RobertPHeller/ESP32-LCC/AtlasLightBoardWiFiLCCTraction_Sound/firmware/doc/Images/LEDPolarity.png

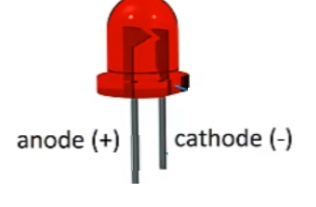
AtlasLightBoardWiFiLCCTraction_Sound/firmware/doc/Images/LEDPolarity.png
