RobertPHeller/ESP32-LCC/AtlasLightBoardWiFiLCCTraction_Sound/firmware/doc/Images/LEDPolaritySymbol.png

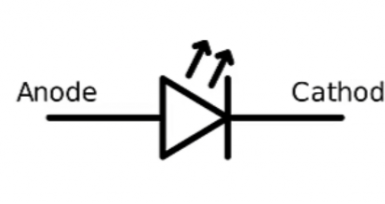
AtlasLightBoardWiFiLCCTraction_Sound/firmware/doc/Images/LEDPolaritySymbol.png
