RobertPHeller/ESP32-LCC/ESP32-Feather-6B6L-SMD/ESP32-Feather-6B6L-SMD.png

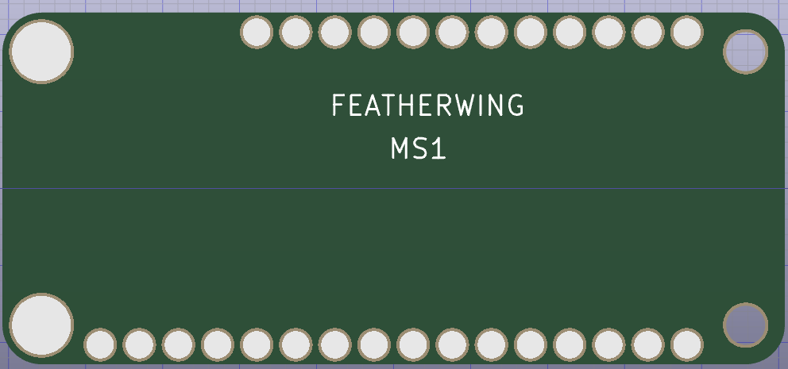
ESP32-Feather-6B6L-SMD/ESP32-Feather-6B6L-SMD.png
