RobertPHeller/ESP32-LCC/ESP32-Mini32-OctalBuffer/KitBooklet/images/8ballsignhookup.png

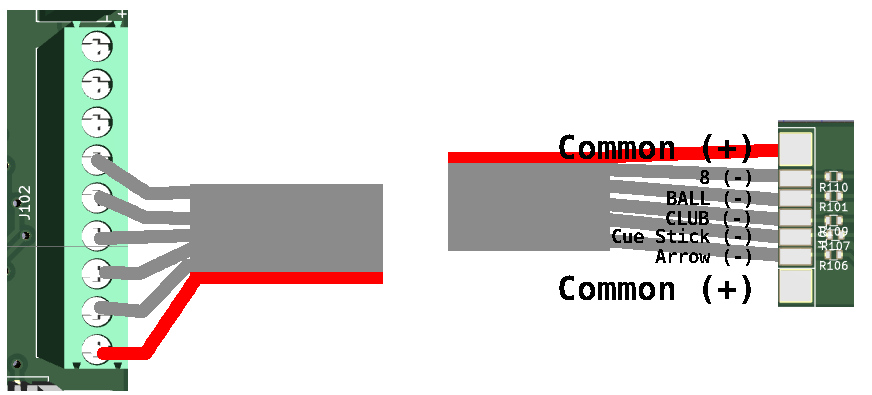
ESP32-Mini32-OctalBuffer/KitBooklet/images/8ballsignhookup.png
