RobertPHeller/ESP32-LCC/ESP32-T7S3-ArduinoBase/firmware/doc/images/StandardRes1Track.png

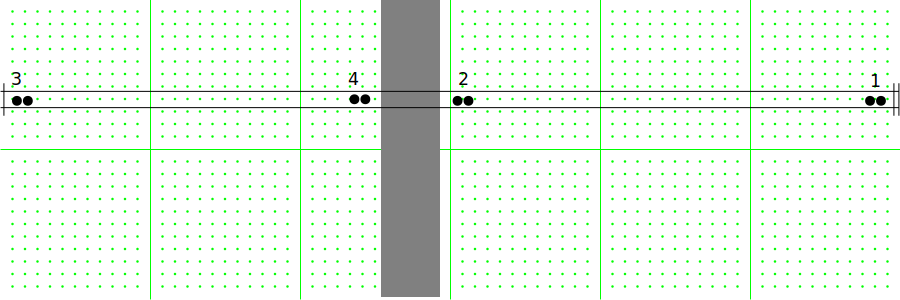
ESP32-T7S3-ArduinoBase/firmware/doc/images/StandardRes1Track.png
