RobertPHeller/ESP32-LCC/ESP32-T7S3-TextDisplaySign/firmware/doc/images/ESP32-T7S3-TextDisplaySign-cut.png

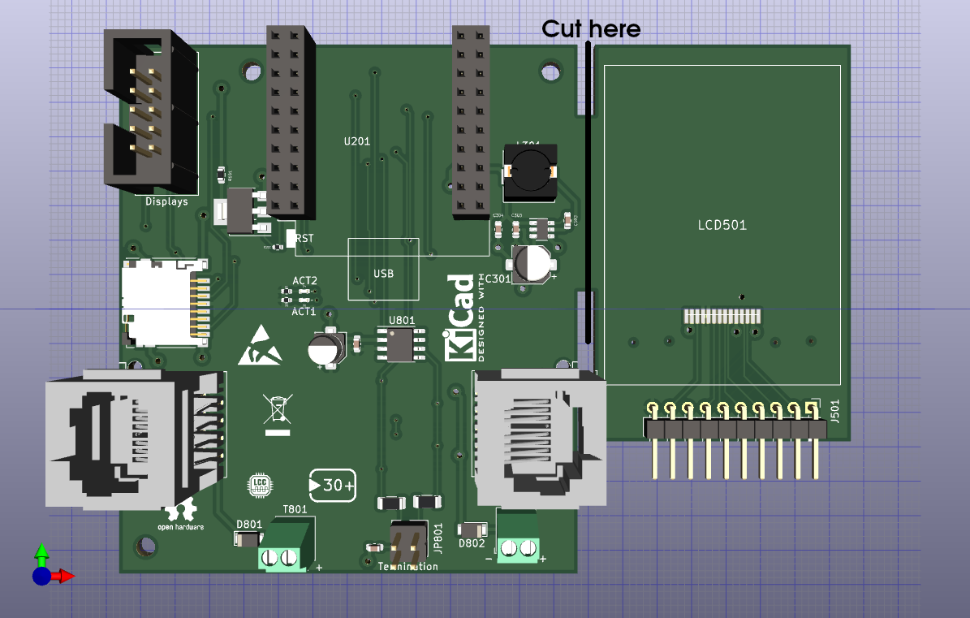
ESP32-T7S3-TextDisplaySign/firmware/doc/images/ESP32-T7S3-TextDisplaySign-cut.png
