RobertPHeller/ESP32-LCC/P9WiFiLCCTraction_Sound/firmware/doc/Images/P9WiFiLCCTraction_Sound_Top3D.png

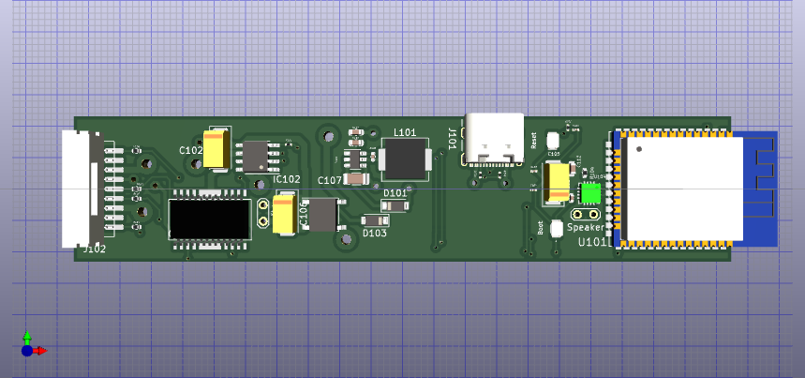
P9WiFiLCCTraction_Sound/firmware/doc/Images/P9WiFiLCCTraction_Sound_Top3D.png
