RobertPHeller/ESP32-LCC/T7S3-MiniDisplay/firmware/doc/Images/4210-00.jpg

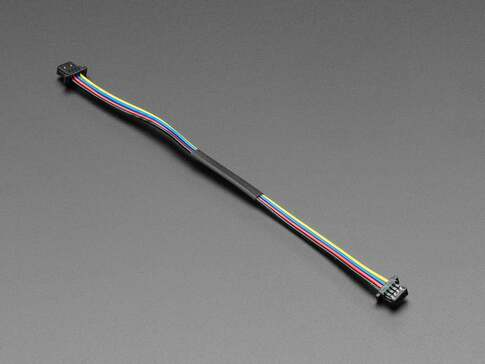
T7S3-MiniDisplay/firmware/doc/Images/4210-00.jpg
