RobertPHeller/ESP32-LCC/T7S3-MiniDisplay/firmware/doc/Images/4440-07.jpg

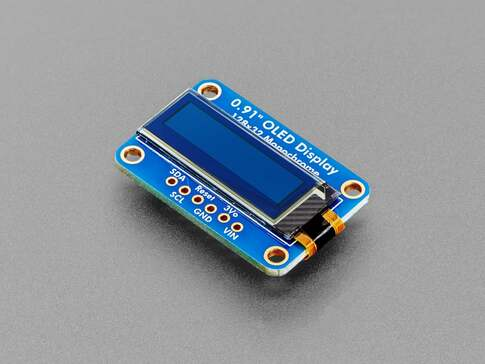
T7S3-MiniDisplay/firmware/doc/Images/4440-07.jpg
