RobertPHeller/ESP32-LCC/T7S3-MiniDisplay/firmware/doc/Images/T7S3MiniDisplay_Top3D.png

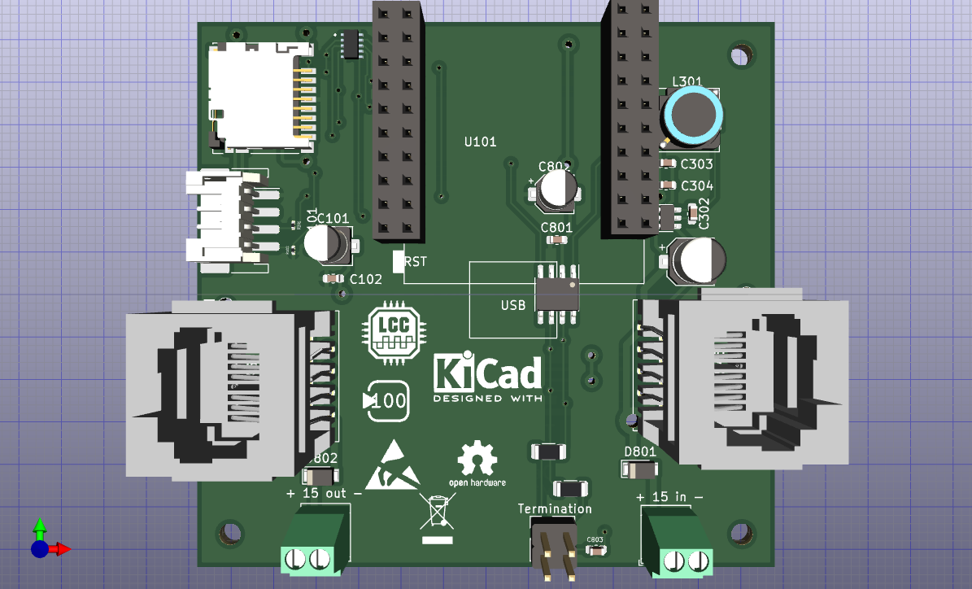
T7S3-MiniDisplay/firmware/doc/Images/T7S3MiniDisplay_Top3D.png
