RobertPHeller/ESP32-LCC/ESP32-T7S3-MultiFunctionUniversalTurnout/SC-DaughterBoard.kicad_pcb

## KiCad design ESP32-T7S3-MultiFunctionUniversalTurnout/SC-DaughterBoard.kicad_pcb (2023-03-05)

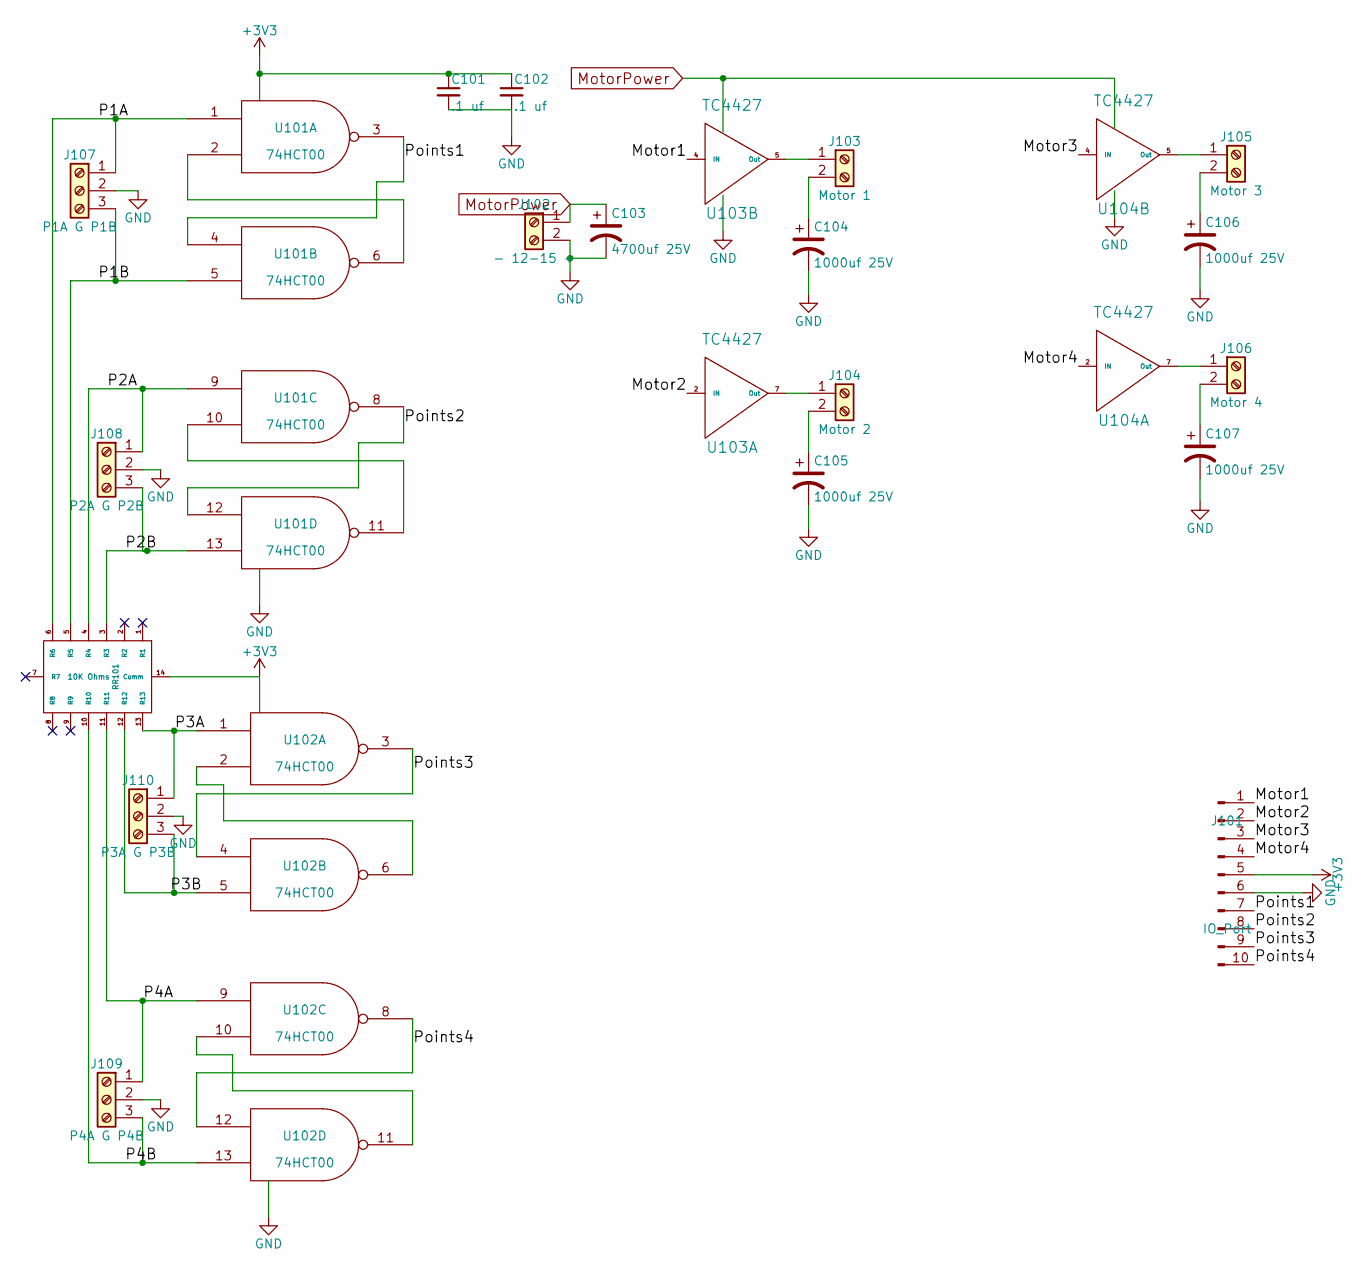
[picture p74: schematic SC-DaughterBoard.sch, ESP32 S3 Multifunction Board SC Daughter Board]

Parts:
C101, C102: .1 uf; C_0603; Mouser Part Number 710-885012206095
C103: 4700uf 25V; EEEFK0J133SM; Mouser Part Number 667-EEE-FK1E472SM
C104, C105, C106, C107: 1000uf 25V; CP_Elec_10x10.5; Mouser Part Number 661-EMZS250ARA102MJA
J101: IO_Port; Pin_Header_Straight_1x10_Pitch2.54mm
J102: - 12-15 +; TerminalBlock_Pheonix_PT-3.5mm_2pol
J103: Motor 1; TerminalBlock_Pheonix_PT-3.5mm_2pol
J104: Motor 2; TerminalBlock_Pheonix_PT-3.5mm_2pol
J105: Motor 3; TerminalBlock_Pheonix_PT-3.5mm_2pol
J106: Motor 4; TerminalBlock_Pheonix_PT-3.5mm_2pol
J107: P1A G P1B; TerminalBlock_Pheonix_MPT-2.54mm_3pol
J108: P2A G P2B; TerminalBlock_Pheonix_MPT-2.54mm_3pol
J109: P4A G P4B; TerminalBlock_Pheonix_MPT-2.54mm_3pol
J110: P3A G P3B; TerminalBlock_Pheonix_MPT-2.54mm_3pol
RR101: 10K Ohms; 4814P; Mouser Part Number 652-4814P-2LF-10K
U101, U102: 74HCT00; SOIC-14_3.9x8.7mm_Pitch1.27mm; Mouser Part Number 595-SN74AHC00D
U103, U104: TC4427; SOIC-8_3.9x4.9mm_Pitch1.27mm

Connections:
+3V3: C101.1, C102.1, J101.5, RR101.14 (Comm), U101.14 (VCC), U102.14 (VCC)
/Motor1: J101.1, U103.4 (IN)
/Motor2: J101.2, U103.2 (IN)
/Motor3: J101.3, U104.4 (IN)
/Motor4: J101.4, U104.2 (IN)
/P1A: J107.1, RR101.6 (R6), U101.1
/P1B: J107.3, RR101.5 (R5), U101.5
/P2A: J108.1, RR101.4 (R4), U101.9
/P2B: J108.3, RR101.3 (R3), U101.13
/P3A: J110.1, RR101.13 (R13), U102.1
/P3B: J110.3, RR101.12 (R12), U102.5
/P4A: J109.1, RR101.11 (R11), U102.9
/P4B: J109.3, RR101.10 (R10), U102.13
/Points1: J101.7, U101.3, U101.4
/Points2: J101.8, U101.8, U101.12
/Points3: J101.9, U102.3, U102.4
/Points4: J101.10, U102.8, U102.12
GND: C101.2, C102.2, C103.2, C104.2, C105.2, C106.2, C107.2, J101.6, J102.2, J107.2, J108.2, J109.2, J110.2, U101.7 (GND), U102.7 (GND), U103.3 (GND), U104.3 (GND)
MotorPower: C103.1, J102.1, U103.6 (Vdd), U104.6 (Vdd)
unnamed: C104.1, J103.2
unnamed: C105.1, J104.2
unnamed: C106.1, J105.2
unnamed: C107.1, J106.2
unnamed: J103.1, U103.5 (Out)
unnamed: J104.1, U103.7 (Out)
unnamed: J105.1, U104.5 (Out)
unnamed: J106.1, U104.7 (Out)
unnamed: U101.2, U101.6
unnamed: U101.10, U101.11
unnamed: U102.2, U102.6
unnamed: U102.10, U102.11

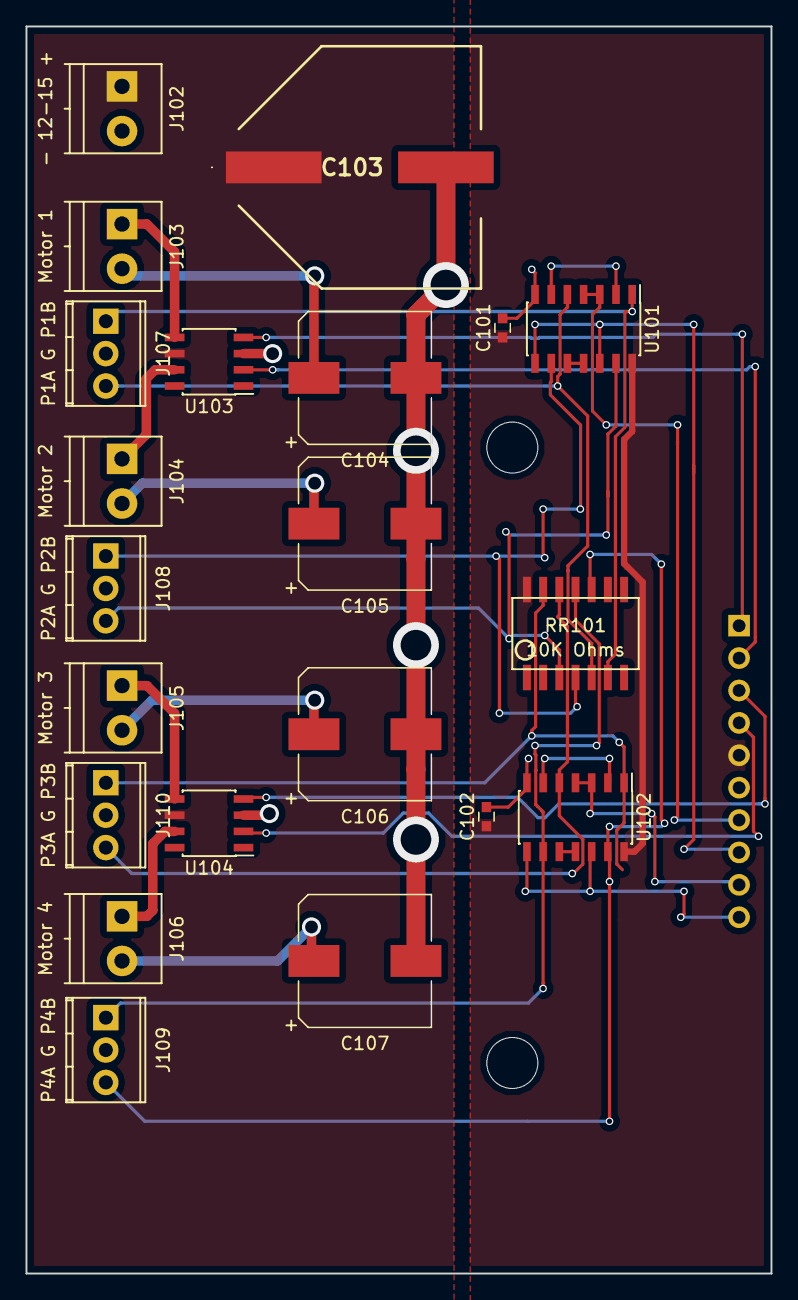
[picture p75: board SC-DaughterBoard.kicad_pcb from above]

Board: 2 copper layers, 58.4 x 97.8 mm, 22 parts (1 on the bottom side), 31 nets.
