RobertPHeller/ESP32-LCC/ESP32-T7S3-MultiFunctionUniversalTurnout/TS-DaughterBoard.kicad_pcb

## KiCad design ESP32-T7S3-MultiFunctionUniversalTurnout/TS-DaughterBoard.kicad_pcb (2023-03-04)

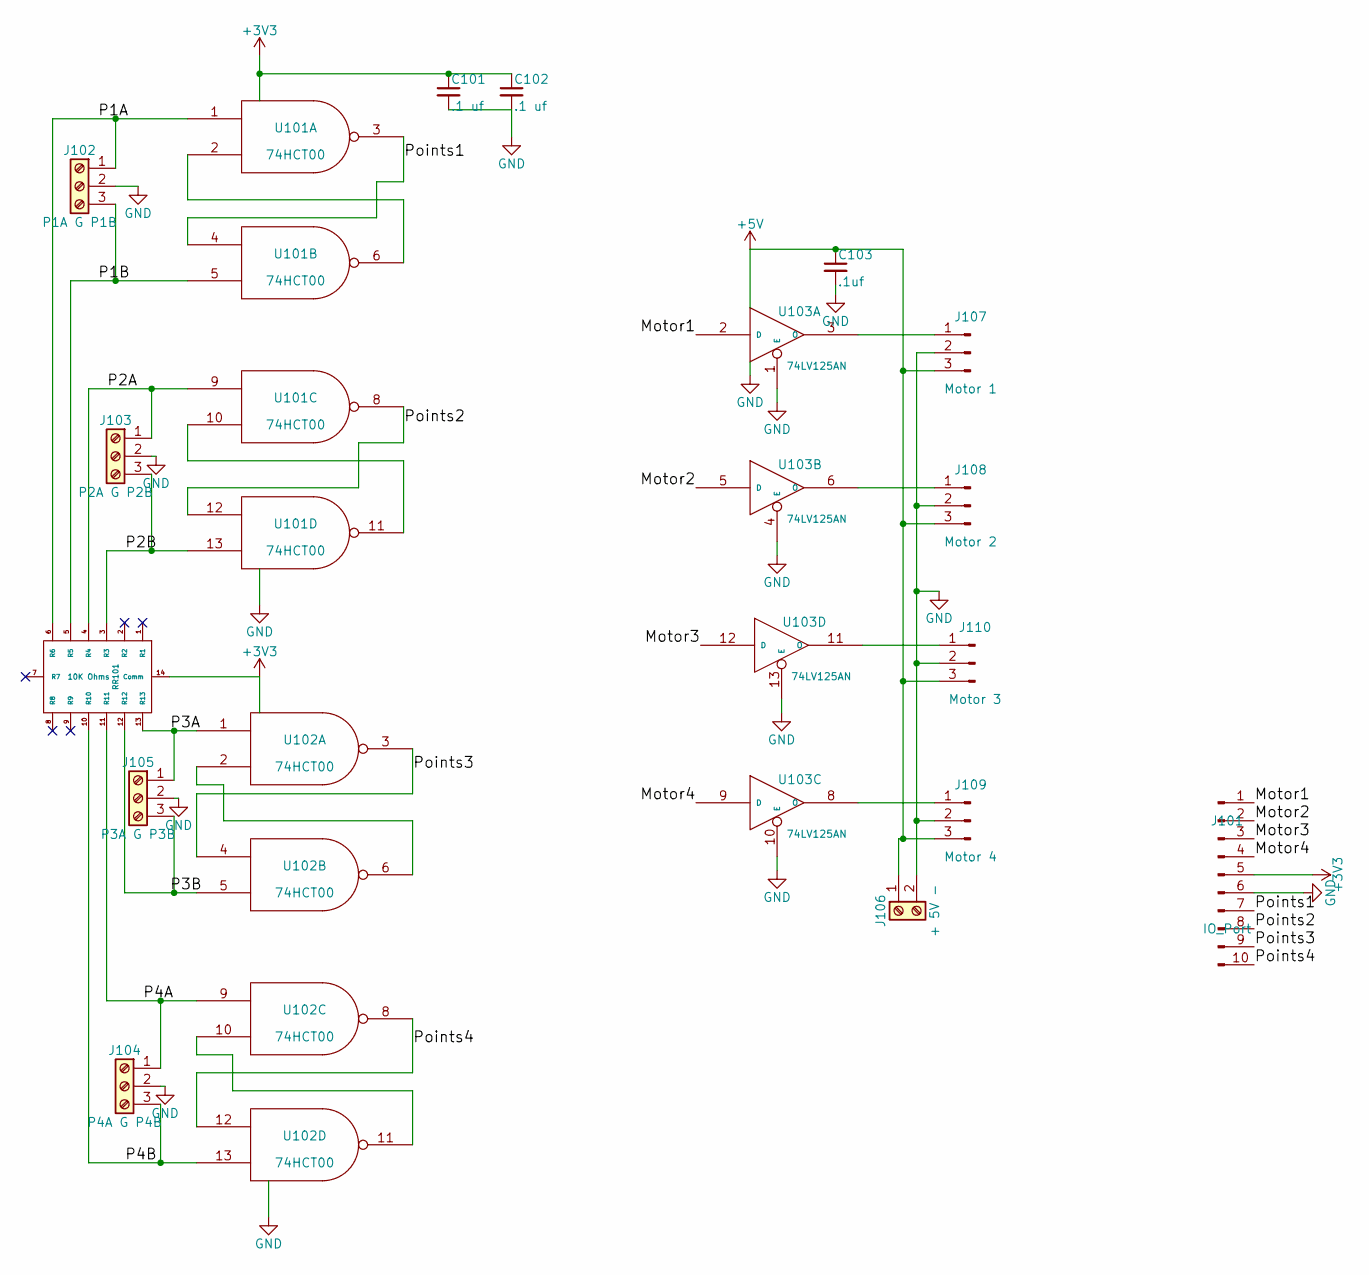
[picture p76: schematic TS-DaughterBoard.sch, ESP32 S3 Multifunction Board]

Parts:
C101, C102: .1 uf; C_0603; Mouser Part Number 710-885012206095
C103: .1uf; C_0603
J101: IO_Port; Pin_Header_Straight_1x10_Pitch2.54mm
J102: P1A G P1B; TerminalBlock_Pheonix_MPT-2.54mm_3pol
J103: P2A G P2B; TerminalBlock_Pheonix_MPT-2.54mm_3pol
J104: P4A G P4B; TerminalBlock_Pheonix_MPT-2.54mm_3pol
J105: P3A G P3B; TerminalBlock_Pheonix_MPT-2.54mm_3pol
J106: + 5V -; TerminalBlock_Pheonix_PT-3.5mm_2pol
J107: Motor 1; Pin_Header_Straight_1x03_Pitch2.54mm
J108: Motor 2; Pin_Header_Straight_1x03_Pitch2.54mm
J109: Motor 4; Pin_Header_Straight_1x03_Pitch2.54mm
J110: Motor 3; Pin_Header_Straight_1x03_Pitch2.54mm
RR101: 10K Ohms; 4814P; Mouser Part Number 652-4814P-2LF-10K
U101, U102: 74HCT00; SOIC-14_3.9x8.7mm_Pitch1.27mm; Mouser Part Number 595-SN74AHC00D
U103: 74LV125AN; SOIC-14_3.9x8.7mm_Pitch1.27mm; Mouser Part Number 771-AHCT125D118

Connections:
+3V3: C101.1, C102.1, J101.5, RR101.14 (Comm), U101.14 (VCC), U102.14 (VCC)
+5V: C103.1, J106.1, J107.3, J108.3, J109.3, J110.3, U103.14 (VXX)
/Motor1: J101.1, U103.2 (D)
/Motor2: J101.2, U103.5 (D)
/Motor3: J101.3, U103.12 (D)
/Motor4: J101.4, U103.9 (D)
/P1A: J102.1, RR101.6 (R6), U101.1
/P1B: J102.3, RR101.5 (R5), U101.5
/P2A: J103.1, RR101.4 (R4), U101.9
/P2B: J103.3, RR101.3 (R3), U101.13
/P3A: J105.1, RR101.13 (R13), U102.1
/P3B: J105.3, RR101.12 (R12), U102.5
/P4A: J104.1, RR101.11 (R11), U102.9
/P4B: J104.3, RR101.10 (R10), U102.13
/Points1: J101.7, U101.3, U101.4
/Points2: J101.8, U101.8, U101.12
/Points3: J101.9, U102.3, U102.4
/Points4: J101.10, U102.8, U102.12
GND: C101.2, C102.2, C103.2, J101.6, J102.2, J103.2, J104.2, J105.2, J106.2, J107.2, J108.2, J109.2, J110.2, U101.7 (GND), U102.7 (GND), U103.1 (E), U103.4 (E), U103.7 (GND), U103.10 (E), U103.13 (E)
unnamed: J107.1, U103.3 (O)
unnamed: J108.1, U103.6 (O)
unnamed: J109.1, U103.8 (O)
unnamed: J110.1, U103.11 (O)
unnamed: U101.2, U101.6
unnamed: U101.10, U101.11
unnamed: U102.2, U102.6
unnamed: U102.10, U102.11

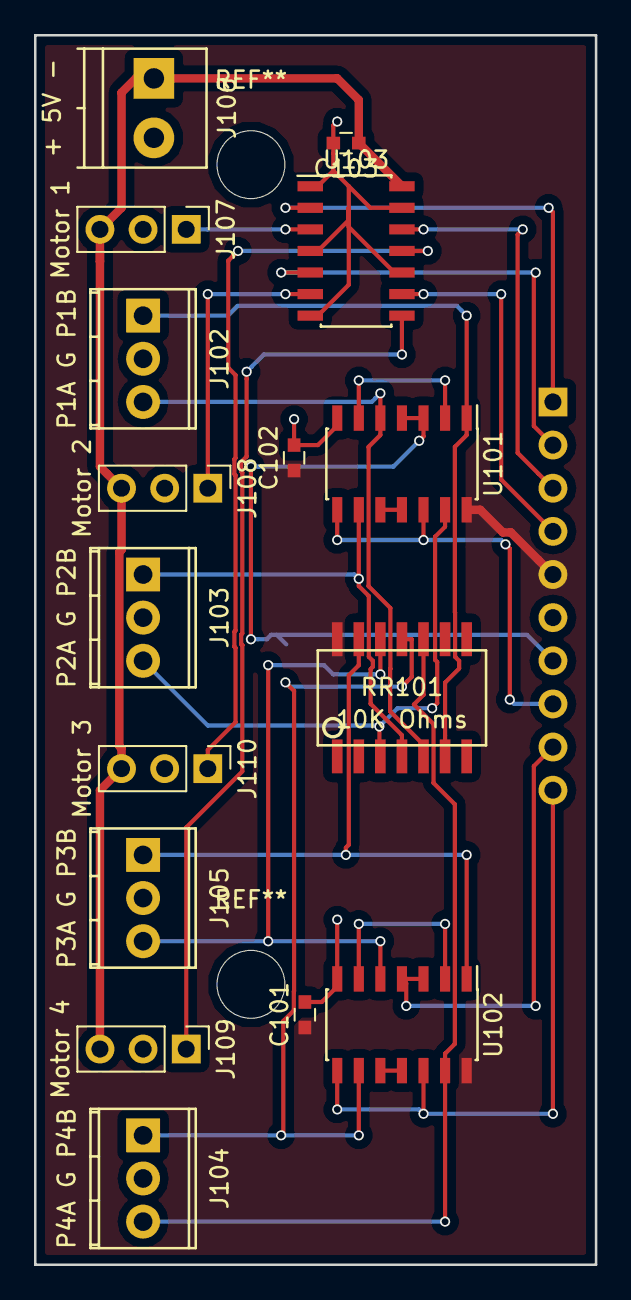
[picture p77: board TS-DaughterBoard.kicad_pcb from above]

Board: 2 copper layers, 33.0 x 72.4 mm, 17 parts (1 on the bottom side), 27 nets.
