RobertPHeller/ESP32-LCC/ESP32-T7S3-MultiFunctionUniversalTurnout/SM-DaughterBoard.kicad_pcb

## KiCad design ESP32-T7S3-MultiFunctionUniversalTurnout/SM-DaughterBoard.kicad_pcb (2023-03-04)

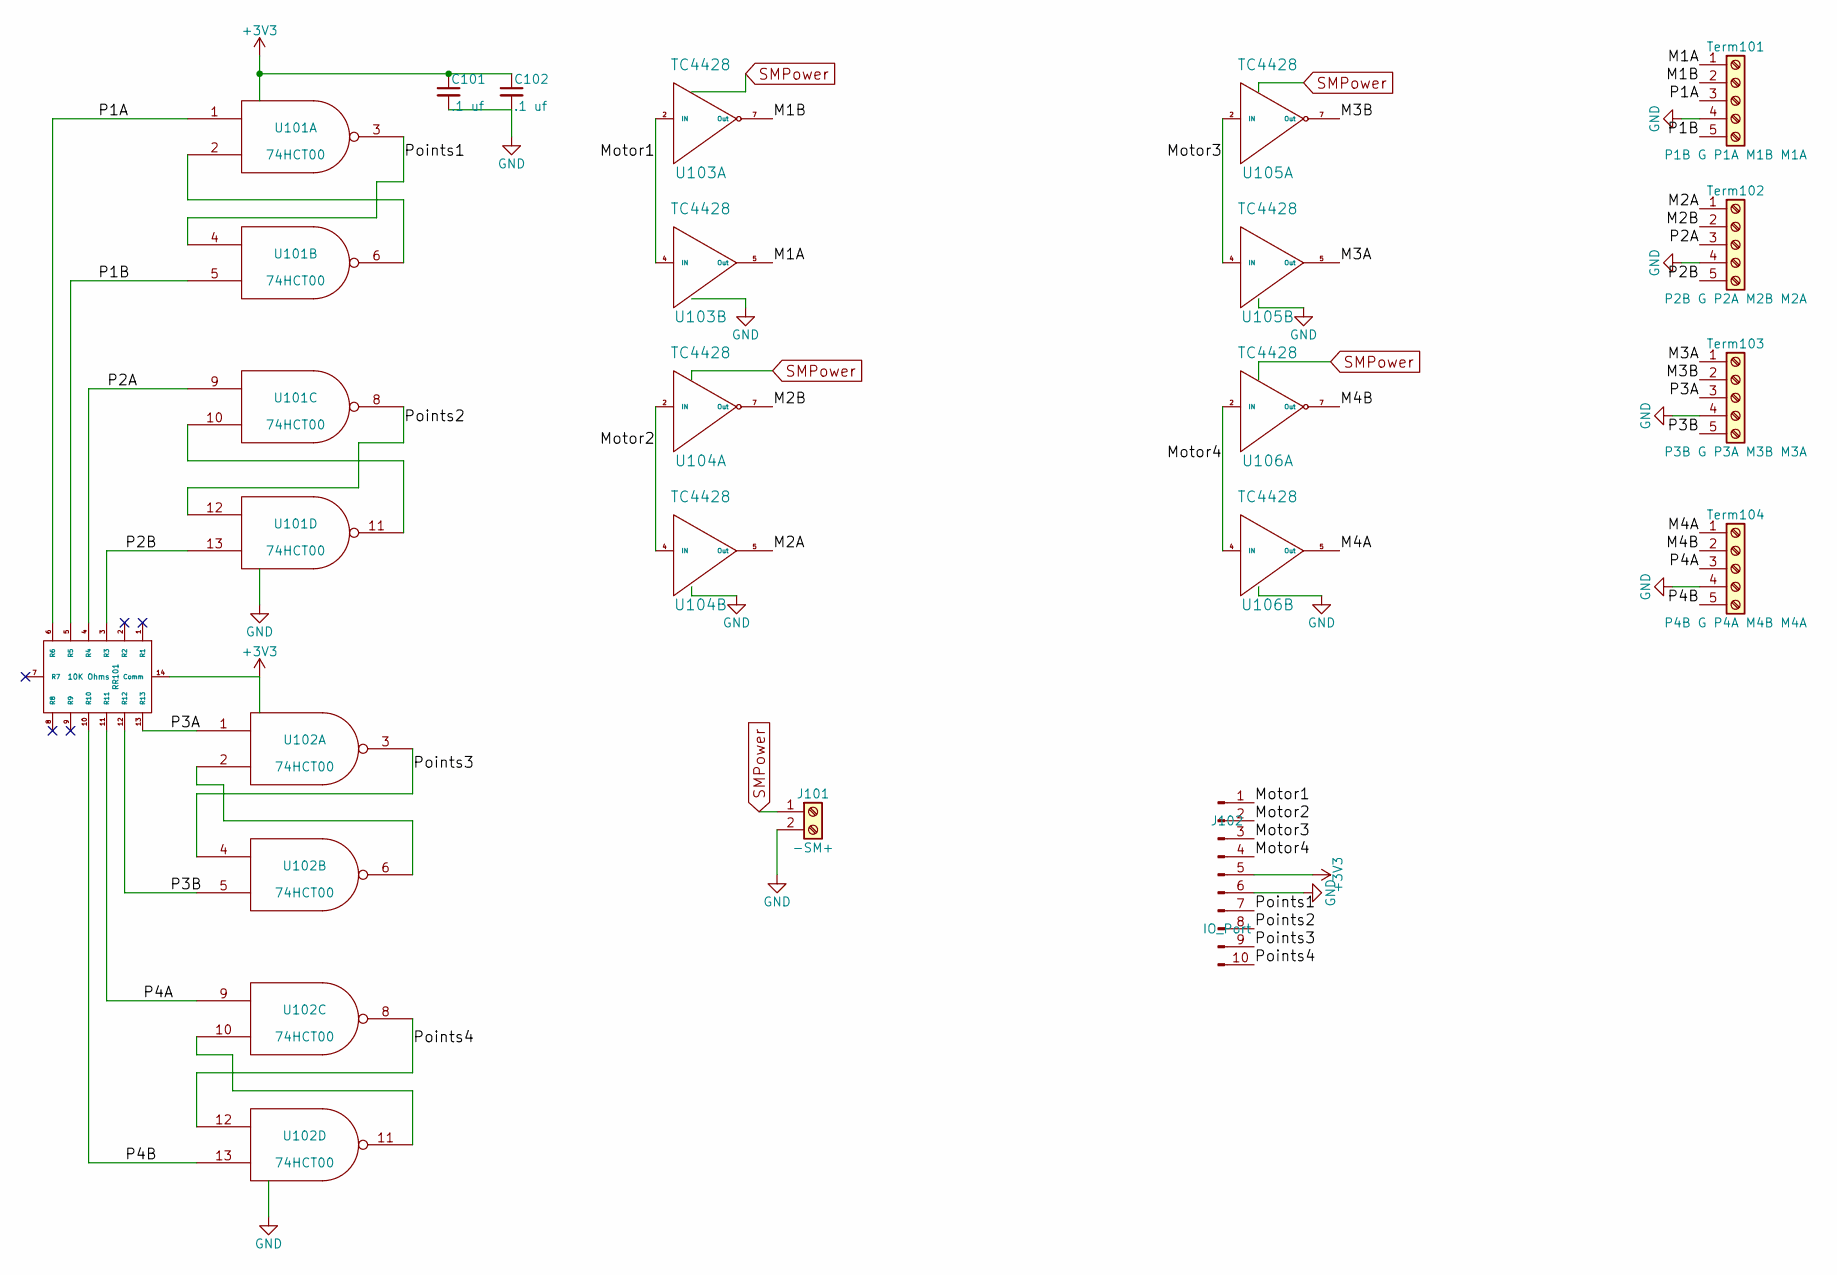
[picture p78: schematic SM-DaughterBoard.sch, ESP32 S3 Multifunction Board]

Parts:
C101, C102: .1 uf; C_0603; Mouser Part Number 710-885012206095
J101: -SM+; TerminalBlock_Pheonix_MPT-2.54mm_2pol; Mouser Part Number 651-172565
J102: IO_Port; Pin_Header_Straight_1x10_Pitch2.54mm
RR101: 10K Ohms; 4814P; Mouser Part Number 652-4814P-2LF-10K
Term101: P1B G P1A M1B M1A; TerminalBlock_Pheonix_MPT-2.54mm_5pol; Mouser Part Number 651-1725685
Term102: P2B G P2A M2B M2A; TerminalBlock_Pheonix_MPT-2.54mm_5pol; Mouser Part Number 651-1725685
Term103: P3B G P3A M3B M3A; TerminalBlock_Pheonix_MPT-2.54mm_5pol; Mouser Part Number 651-1725685
Term104: P4B G P4A M4B M4A; TerminalBlock_Pheonix_MPT-2.54mm_5pol; Mouser Part Number 651-1725685
U101, U102: 74HCT00; SOIC-14_3.9x8.7mm_Pitch1.27mm; Mouser Part Number 595-SN74AHC00D
U103, U104, U105, U106: TC4428; SOIC-8_3.9x4.9mm_Pitch1.27mm; Mouser Part Number 579-TC4428VOA

Connections:
+3V3: C101.1, C102.1, J102.5, RR101.14 (Comm), U101.14 (VCC), U102.14 (VCC)
/M1A: Term101.1, U103.5 (Out)
/M1B: Term101.2, U103.7 (Out)
/M2A: Term102.1, U104.5 (Out)
/M2B: Term102.2, U104.7 (Out)
/M3A: Term103.1, U105.5 (Out)
/M3B: Term103.2, U105.7 (Out)
/M4A: Term104.1, U106.5 (Out)
/M4B: Term104.2, U106.7 (Out)
/Motor1: J102.1, U103.2 (IN), U103.4 (IN)
/Motor2: J102.2, U104.2 (IN), U104.4 (IN)
/Motor3: J102.3, U105.2 (IN), U105.4 (IN)
/Motor4: J102.4, U106.2 (IN), U106.4 (IN)
/P1A: RR101.6 (R6), Term101.3, U101.1
/P1B: RR101.5 (R5), Term101.5, U101.5
/P2A: RR101.4 (R4), Term102.3, U101.9
/P2B: RR101.3 (R3), Term102.5, U101.13
/P3A: RR101.13 (R13), Term103.3, U102.1
/P3B: RR101.12 (R12), Term103.5, U102.5
/P4A: RR101.11 (R11), Term104.3, U102.9
/P4B: RR101.10 (R10), Term104.5, U102.13
/Points1: J102.7, U101.3, U101.4
/Points2: J102.8, U101.8, U101.12
/Points3: J102.9, U102.3, U102.4
/Points4: J102.10, U102.8, U102.12
GND: C101.2, C102.2, J101.2, J102.6, Term101.4, Term102.4, Term103.4, Term104.4, U101.7 (GND), U102.7 (GND), U103.3 (GND), U104.3 (GND), U105.3 (GND), U106.3 (GND)
unnamed: U101.2, U101.6
unnamed: U101.10, U101.11
unnamed: U102.2, U102.6
unnamed: U102.10, U102.11
SMPower: J101.1, U103.6 (Vdd), U104.6 (Vdd), U105.6 (Vdd), U106.6 (Vdd)

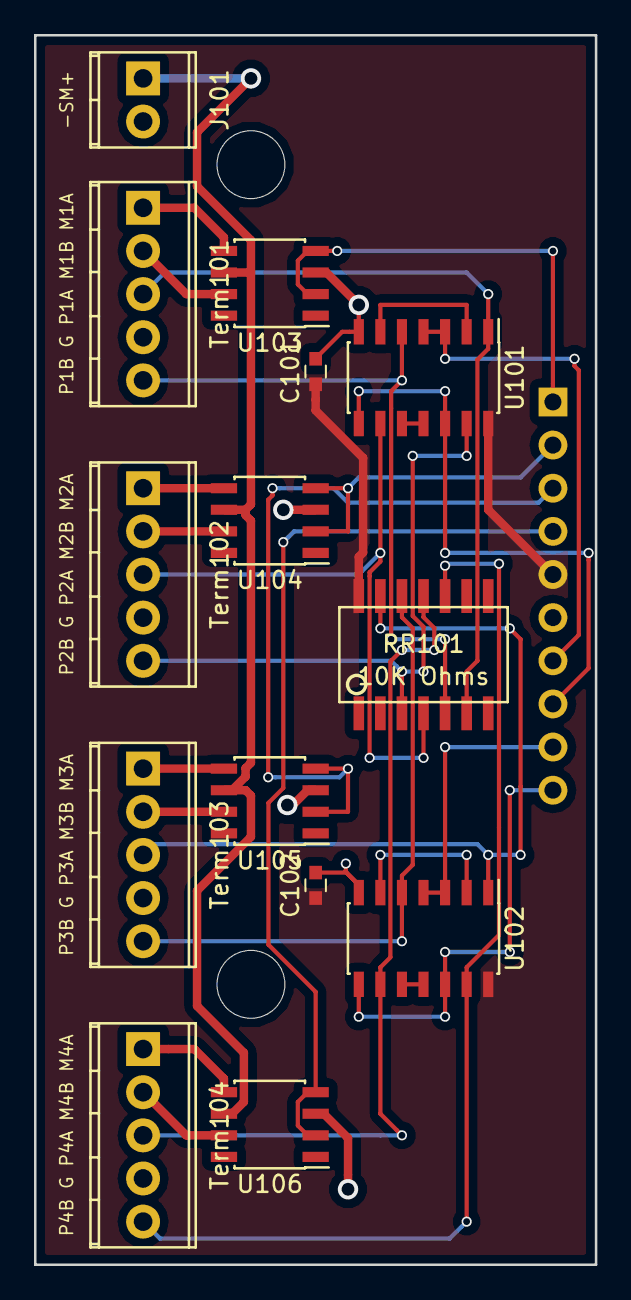
[picture p79: board SM-DaughterBoard.kicad_pcb from above]

Board: 2 copper layers, 33.0 x 72.4 mm, 15 parts (1 on the bottom side), 31 nets.
