RobertPHeller/ESP32-LCC/ESP32-S3DK-OctalServo/ESP32-S3DK-OctalServo.kicad_pcb

## KiCad design ESP32-S3DK-OctalServo/ESP32-S3DK-OctalServo.kicad_pcb (2023-02-02)

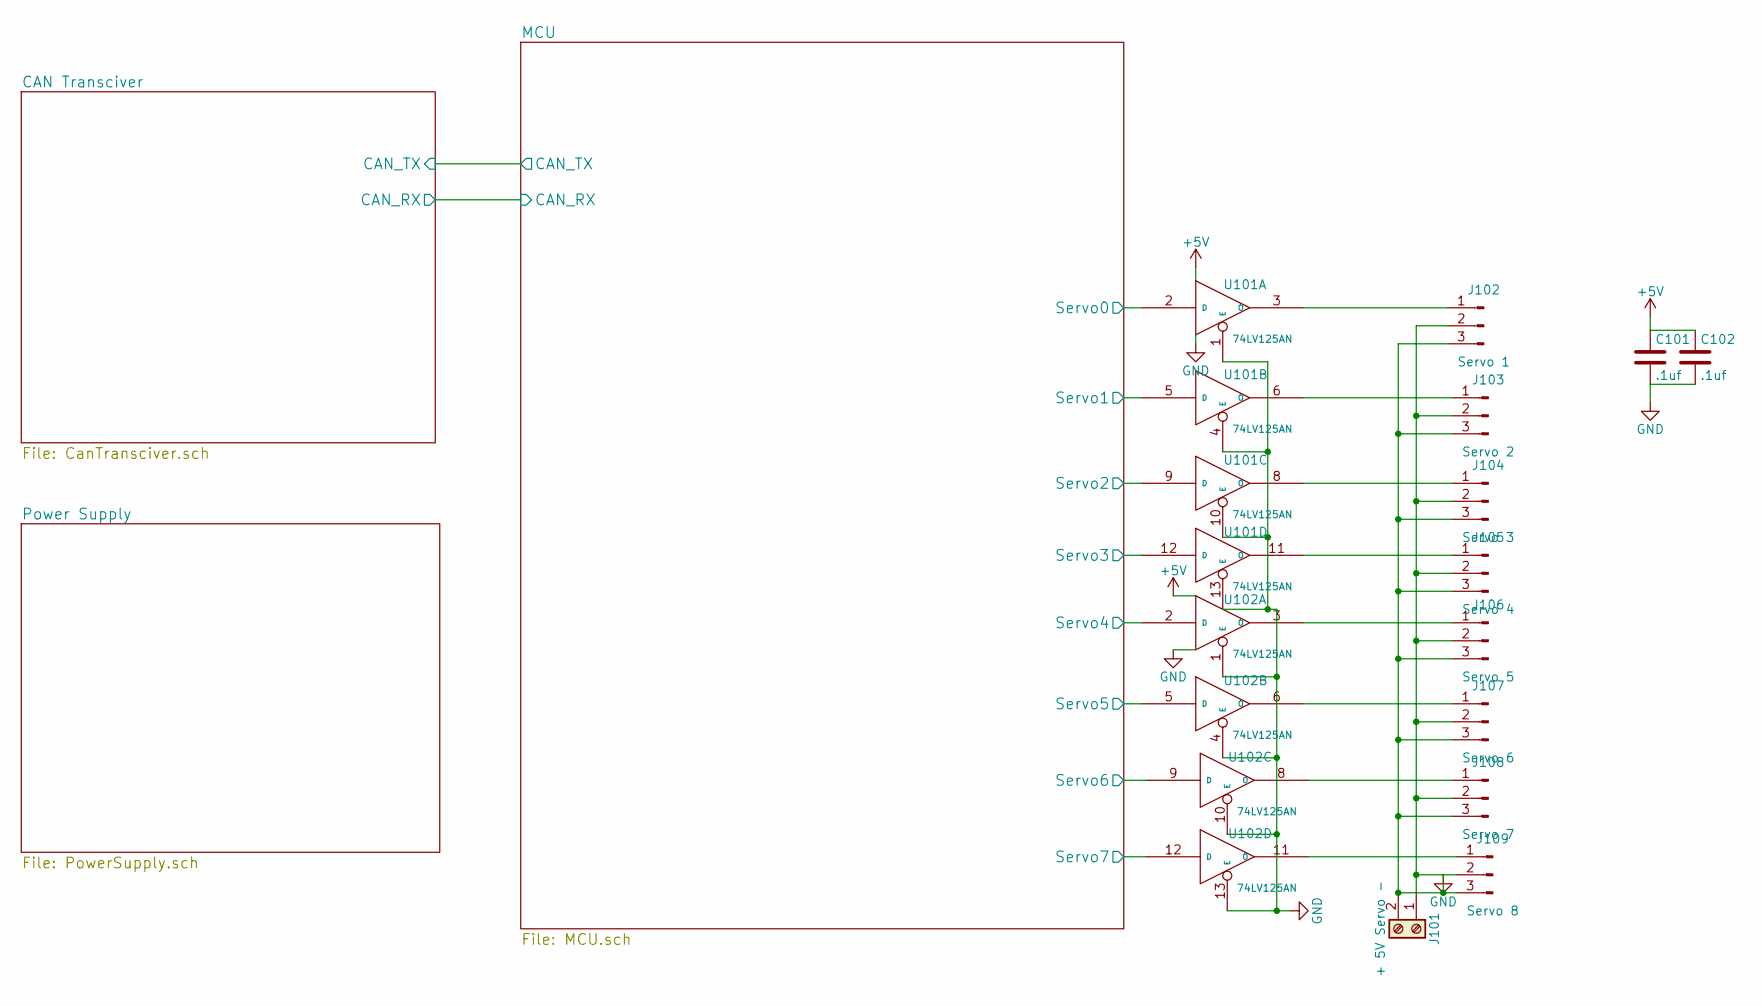
[picture p80: schematic ESP32-S3DK-OctalServo.sch]

Parts:
C101, C102: .1uf; C_0603
J101: + 5V Servo -; TerminalBlock_Pheonix_PT-3.5mm_2pol
J102: Servo 1; Pin_Header_Straight_1x03_Pitch2.54mm
J103: Servo 2; Pin_Header_Straight_1x03_Pitch2.54mm
J104: Servo 3; Pin_Header_Straight_1x03_Pitch2.54mm
J105: Servo 4; Pin_Header_Straight_1x03_Pitch2.54mm
J106: Servo 5; Pin_Header_Straight_1x03_Pitch2.54mm
J107: Servo 6; Pin_Header_Straight_1x03_Pitch2.54mm
J108: Servo 7; Pin_Header_Straight_1x03_Pitch2.54mm
J109: Servo 8; Pin_Header_Straight_1x03_Pitch2.54mm
U101, U102: 74LV125AN; SOIC-14_3.9x8.7mm_Pitch1.27mm; Mouser Part Number 771-AHCT125D118

Connections:
+5V: C101.1, C102.1, U101.14 (VCC), U102.14 (VCC); also elsewhere on the board
/MCU/Servo0: U101.2 (D); also elsewhere on the board
/MCU/Servo1: U101.5 (D); also elsewhere on the board
/MCU/Servo2: U101.9 (D); also elsewhere on the board
/MCU/Servo3: U101.12 (D); also elsewhere on the board
/MCU/Servo4: U102.2 (D); also elsewhere on the board
/MCU/Servo5: U102.5 (D); also elsewhere on the board
/MCU/Servo6: U102.9 (D); also elsewhere on the board
/MCU/Servo7: U102.12 (D); also elsewhere on the board
unnamed: J102.1, U101.3 (O)
unnamed: J103.1, U101.6 (O)
unnamed: J104.1, U101.8 (O)
unnamed: J105.1, U101.11 (O)
unnamed: J106.1, U102.3 (O)
unnamed: J107.1, U102.6 (O)
unnamed: J108.1, U102.8 (O)
unnamed: J109.1, U102.11 (O)

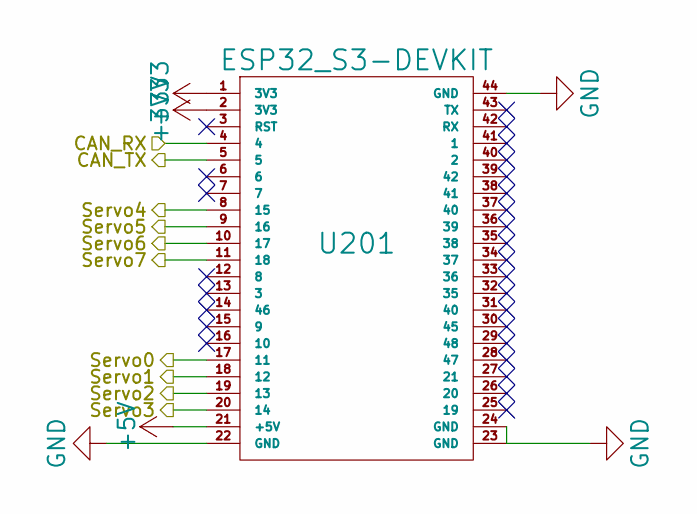
[picture p81: schematic MCU.sch]

Parts:
U201: ESP32_S3-DEVKIT; ESP32-S3-Devkit-C

Connections:
+3V3: U201.1 (3V3), U201.2 (3V3); also elsewhere on the board
+5V: U201.21 (+5V); also elsewhere on the board
/CAN Transciver/CAN_RX: U201.4; also elsewhere on the board
/CAN Transciver/CAN_TX: U201.5; also elsewhere on the board
/MCU/Servo0: U201.17 (11); also elsewhere on the board
/MCU/Servo1: U201.18 (12); also elsewhere on the board
/MCU/Servo2: U201.19 (13); also elsewhere on the board
/MCU/Servo3: U201.20 (14); also elsewhere on the board
/MCU/Servo4: U201.8 (15); also elsewhere on the board
/MCU/Servo5: U201.9 (16); also elsewhere on the board
/MCU/Servo6: U201.10 (17); also elsewhere on the board
/MCU/Servo7: U201.11 (18); also elsewhere on the board
