RobertPHeller/ESP32-LCC/ESP32-S3DK-OctalServo/ESP32-S3DK-OctalServo.kicad_pcb

## KiCad design ESP32-S3DK-OctalServo/ESP32-S3DK-OctalServo.kicad_pcb (continued)

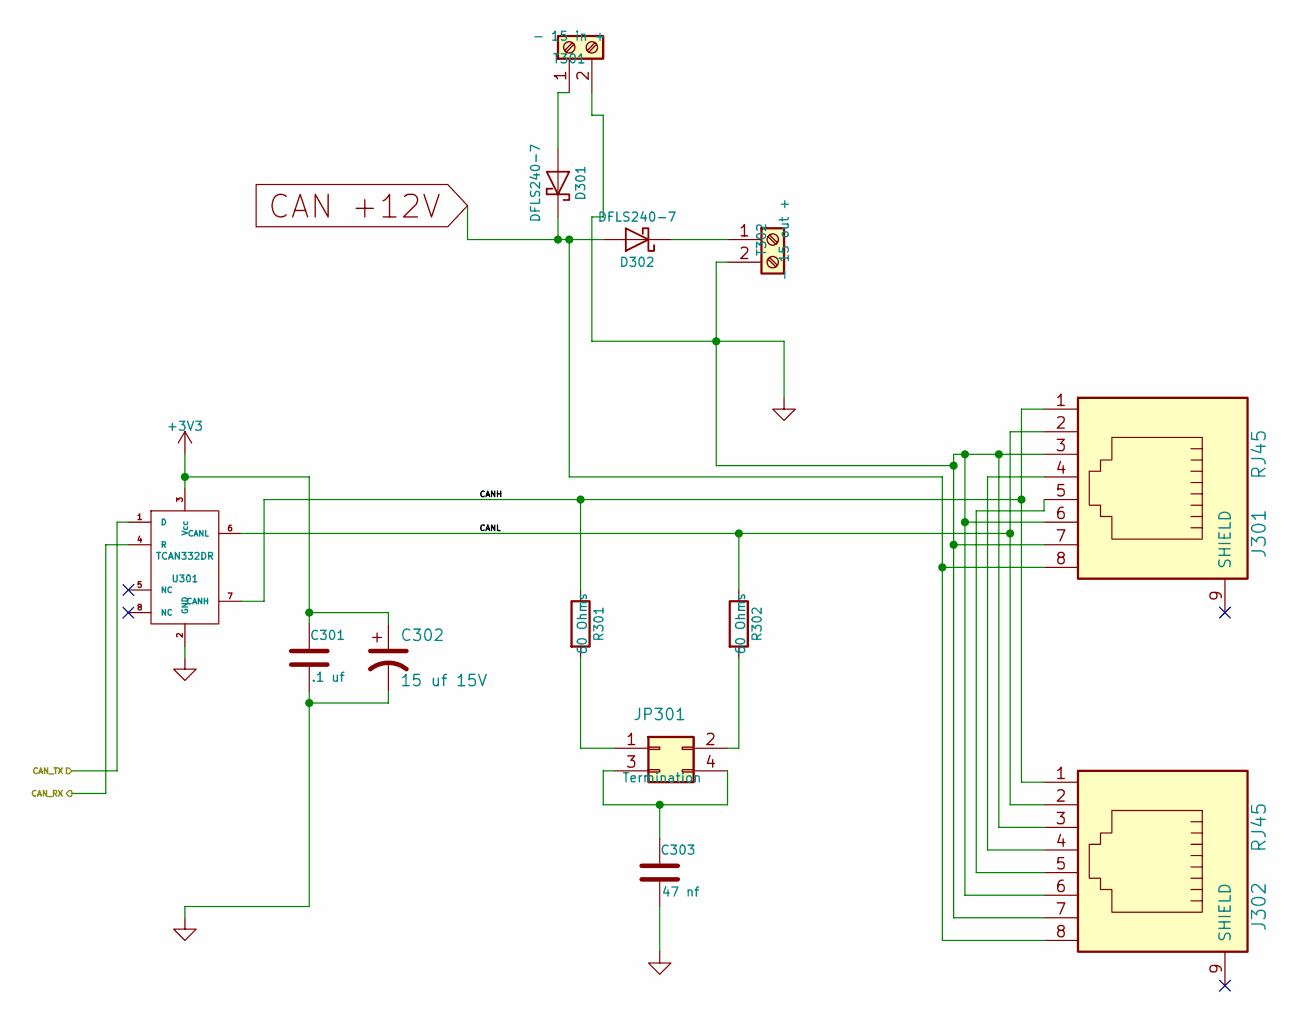
[picture p82: schematic CanTransciver.sch, ESP32 S3 Multifunction Board]

Parts:
C301: .1 uf; C_0603; Mouser Part Number 710-885012206095
C302: 15 uf 15V; CP_Elec_4x5.7; Mouser Part Number 647-UUD1C150MCL
C303: 47 nf; C_0603; Mouser Part Number 710-885012206093
D301, D302: DFLS240-7; D_PowerDI-123; Mouser Part Number 621-DFLS240-7
J301, J302: RJ45; RJ45_8N-S; Mouser Part Number 710-615008144221
JP301: Termination; Pin_Header_Straight_2x02_Pitch2.54mm; Mouser Part Number 649-67997-404HLF
R301, R302: 60 Ohms; R_1206; Mouser Part Number 71-CRCW120660R0KNAIF
T301: - 15 in +; TerminalBlock_Pheonix_MPT-2.54mm_2pol; Mouser Part Number 651-1725656
T302: - 15 out +; TerminalBlock_Pheonix_MPT-2.54mm_2pol; Mouser Part Number 651-1725656
U301: TCAN332DR; SOIC-8_3.9x4.9mm_Pitch1.27mm; Mouser Part Number 595-TCAN332DR

Connections:
+3V3: C301.1, C302.1, U301.3 (Vcc); also elsewhere on the board
/CAN Transciver/CANH: J301.1, J302.1, R301.1, U301.7 (CANH)
/CAN Transciver/CANL: J301.2, J302.2, R302.1, U301.6 (CANL)
/CAN Transciver/CAN_RX: U301.4 (R); also elsewhere on the board
/CAN Transciver/CAN_TX: U301.1 (D); also elsewhere on the board
CAN +12V: D301.1 (K), D302.2 (A), J301.8, J302.8; also elsewhere on the board
unnamed: C303.1, JP301.3, JP301.4
unnamed: D301.2 (A), T301.1
unnamed: D302.1 (K), T302.1
unnamed: J301.4, J302.4
unnamed: J301.5, J302.5
unnamed: JP301.1, R301.2
unnamed: JP301.2, R302.2

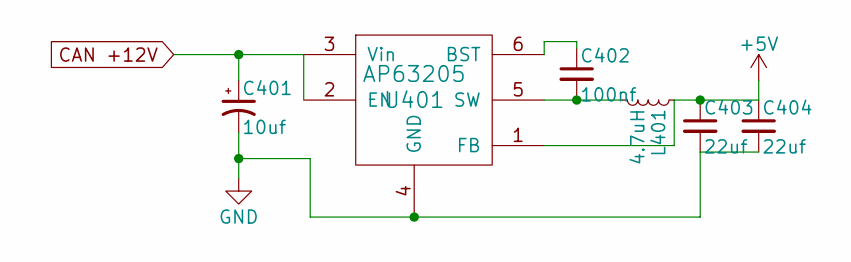
[picture p83: schematic PowerSupply.sch, ESP32 S3 Multifunction Board]

Parts:
C401: 10uf; CP_Elec_5x5.3; Mouser Part Number 710-865230542002
C402: 100nf; C_0603; Mouser Part Number 710-885012206020
C403, C404: 22uf; C_0603; Mouser Part Number 603-CC0603MRX6S5B226
L401: 4.7uH; L_7.3x7.3_H4.5; Mouser Part Number 81-B1047AS-4R7NP3
U401: AP63205; TSOT-23-6_MK06A; Mouser Part Number 621-AP63205WU-7

Connections:
+5V: C403.1, C404.1, L401.1, U401.1 (FB); also elsewhere on the board
CAN +12V: C401.1, U401.2 (EN), U401.3 (Vin); also elsewhere on the board
unnamed: C402.1, U401.6 (BST)
unnamed: C402.2, L401.2, U401.5 (SW)

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
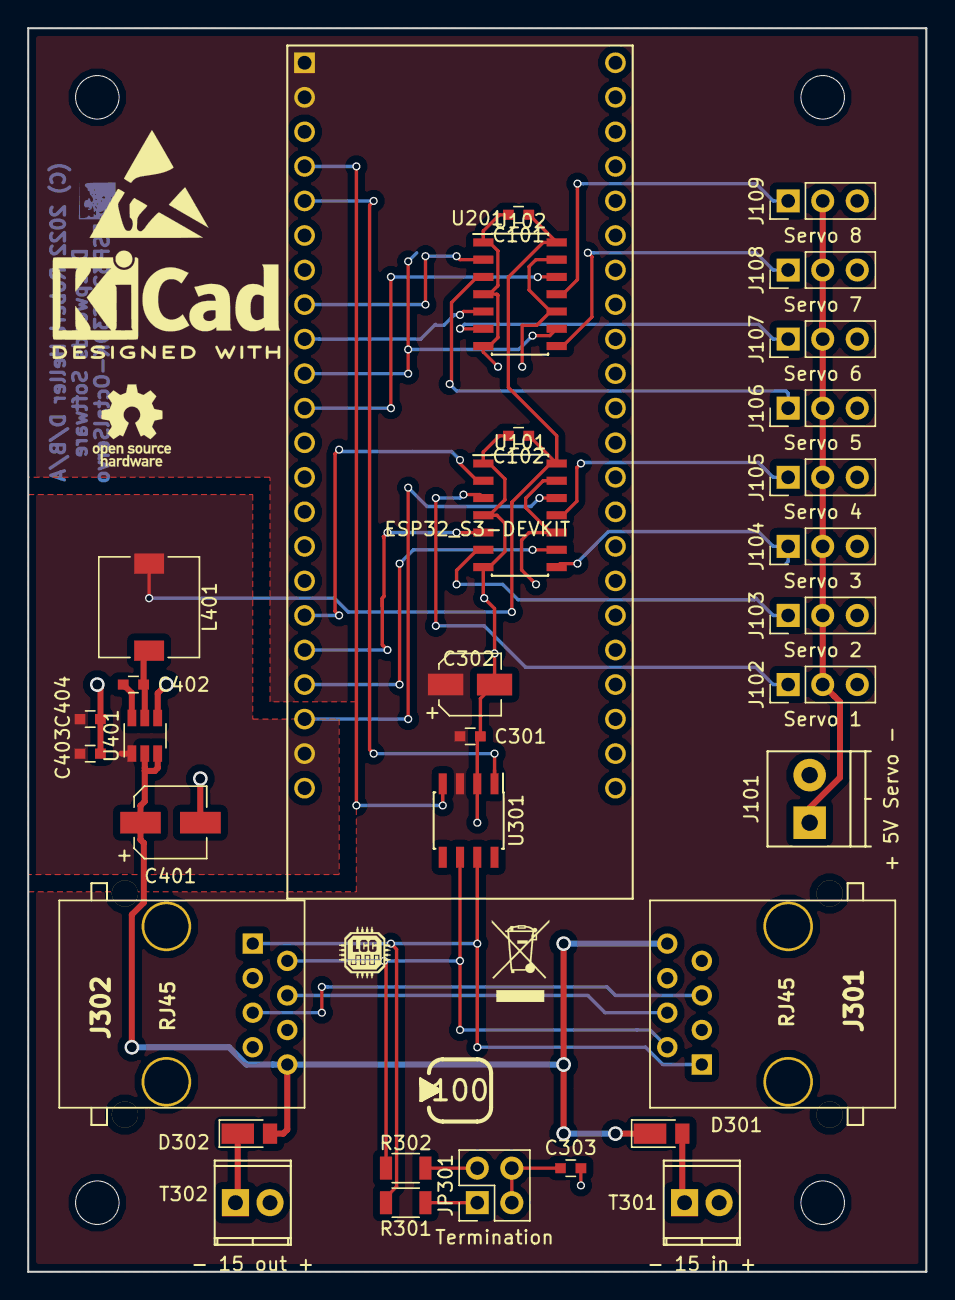
[picture p84: board ESP32-S3DK-OctalServo.kicad_pcb from above]

Board: 2 copper layers, 66.0 x 91.4 mm, 33 parts (0 on the bottom side), 34 nets.
