RobertPHeller/ESP32-LCC/ESP32-S3DK-OctalTwinCoil/ESP32-S3DK-OctalTwinCoil.kicad_pcb

## KiCad design ESP32-S3DK-OctalTwinCoil/ESP32-S3DK-OctalTwinCoil.kicad_pcb (2023-01-31)

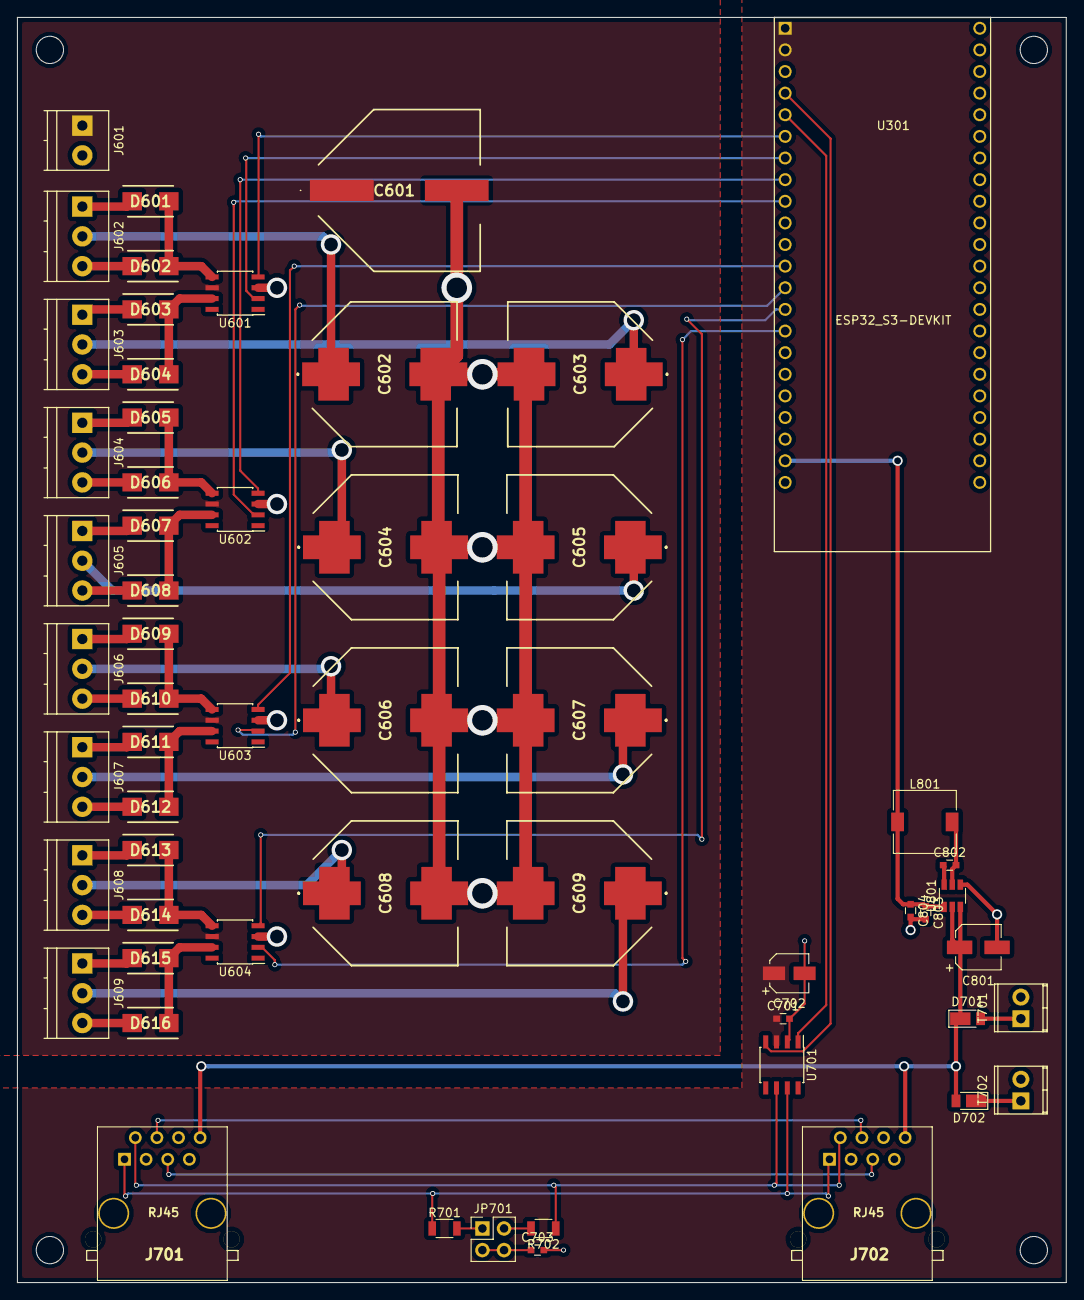
[picture p85: board ESP32-S3DK-OctalTwinCoil.kicad_pcb from above]

Board: 2 copper layers, 123.2 x 148.6 mm, 58 parts (0 on the bottom side), 58 nets.

Parts:
C601: 4700uf 25V; EEEFK0J133SM
C602, C603, C604, C605, C606, C607, C608, C609: 2200uF 25V; EEEFK0J682AV
C701: .1 uf; C_0603
C702: 15 uf 15V; CP_Elec_4x5.7
C703: 47 nf; C_0603
C801: 10uf; CP_Elec_5x5.3
C802: 100nf; C_0603
C803, C804: 22uf; C_0603
D601, D602, D603, D604, D605, D606, D607, D608, D609, D610, D611, D612, D613, D614, D615, D616: S2A; DIOM5336X245N
D701, D702: DFLS240-7; D_PowerDI-123
J601: - 12-15 +; TerminalBlock_Pheonix_PT-3.5mm_2pol
J602: Motor 1; TerminalBlock_Pheonix_PT-3.5mm_3pol
J603: Motor 2; TerminalBlock_Pheonix_PT-3.5mm_3pol
J604: Motor 3; TerminalBlock_Pheonix_PT-3.5mm_3pol
J605: Motor 4; TerminalBlock_Pheonix_PT-3.5mm_3pol
J606: Motor 5; TerminalBlock_Pheonix_PT-3.5mm_3pol
J607: Motor 6; TerminalBlock_Pheonix_PT-3.5mm_3pol
J608: Motor 7; TerminalBlock_Pheonix_PT-3.5mm_3pol
J609: Motor 8; TerminalBlock_Pheonix_PT-3.5mm_3pol
J701, J702: RJ45; RJ45_8N-S
JP701: Termination; Pin_Header_Straight_2x02_Pitch2.54mm
L801: 4.7uH; L_7.3x7.3_H4.5
R701, R702: 60 Ohms; R_1206
T701: + 15 in -; TerminalBlock_Pheonix_MPT-2.54mm_2pol
T702: + 15 out -; TerminalBlock_Pheonix_MPT-2.54mm_2pol
U301: ESP32_S3-DEVKIT; ESP32-S3-Devkit-C
U601, U602, U603, U604: TC4427; SOIC-8_3.9x4.9mm_Pitch1.27mm
U701: TCAN332DR; SOIC-8_3.9x4.9mm_Pitch1.27mm
U801: AP63205; TSOT-23-6_MK06A

Connections:
+3V3: C701.1, C702.1, U301.1, U301.2, U701.3
+5V: C803.1, C804.1, L801.1, U301.21, U801.1
/CAN Transciver/CANH: J701.1, J702.1, R701.1, U701.7
/CAN Transciver/CANL: J701.2, J702.2, R702.1, U701.6
/CAN Transciver/CAN_RX: U301.4, U701.4
/CAN Transciver/CAN_TX: U301.5, U701.1
/MCU/GPIO3/Motor6: U301.13, U603.2
/MCU/GPIO6/Motor1: U301.6, U601.4
/MCU/GPIO7/Motor2: U301.7, U601.2
/MCU/GPIO8/Motor5: U301.12, U603.4
/MCU/GPIO9/Motor8: U301.15, U604.2
/MCU/GPIO15/Motor3: U301.8, U602.4
/MCU/GPIO16/Motor4: U301.9, U602.2
/MCU/GPIO46/Motor7: U301.14, U604.4
CAN +12V: C801.1, D701.1, D702.2, J701.8, J702.8, U801.2, U801.3
GND: C601.2, C602.2, C603.2, C604.2, C605.2, C606.2, C607.2, C608.2, C609.2, C701.2, C702.2, C703.2, C801.2, C803.2, C804.2, J601.2, J701.3, J701.6, J701.7, J702.3, J702.6, J702.7, T701.2, T702.2, U301.22, U301.23, U301.24, U301.44, U601.3, U602.3, U603.3, U604.3, U701.2, U801.4
MotorPower: C601.1, J601.1, U601.6, U602.6, U603.6, U604.6
unnamed: C602.1, J602.2
unnamed: C603.1, J603.2
unnamed: C604.1, J604.2
unnamed: C605.1, J605.2
unnamed: C606.1, J606.2
unnamed: C607.1, J607.2
unnamed: C608.1, J608.2
unnamed: C609.1, J609.2
unnamed: C703.1, JP701.3, JP701.4
unnamed: C802.1, U801.6
unnamed: C802.2, L801.2, U801.5
unnamed: D601.1, J602.1
unnamed: D601.2, D602.1, U601.5
unnamed: D602.2, J602.3
unnamed: D603.1, J603.1
unnamed: D603.2, D604.1, U601.7
unnamed: D604.2, J603.3
unnamed: D605.1, J604.1
unnamed: D605.2, D606.1, U602.5
unnamed: D606.2, J604.3
unnamed: D607.1, J605.1
unnamed: D607.2, D608.1, U602.7
unnamed: D608.2, J605.3
unnamed: D609.1, J606.1
unnamed: D609.2, D610.1, U603.5
unnamed: D610.2, J606.3
unnamed: D611.1, J607.1
unnamed: D611.2, D612.1, U603.7
unnamed: D612.2, J607.3
unnamed: D613.1, J608.1
unnamed: D613.2, D614.1, U604.5
unnamed: D614.2, J608.3
unnamed: D615.1, J609.1
unnamed: D615.2, D616.1, U604.7
unnamed: D616.2, J609.3
unnamed: D701.2, T701.1
unnamed: D702.1, T702.1
unnamed: J701.4, J702.4
unnamed: J701.5, J702.5
unnamed: JP701.1, R701.2
unnamed: JP701.2, R702.2
