RobertPHeller/ESP32-LCC/ESP32-S3-MegaMultiFunction/ESP32-S3-MegaMultiFunction.kicad_pcb

## KiCad design ESP32-S3-MegaMultiFunction/ESP32-S3-MegaMultiFunction.kicad_pcb (2022-10-24)

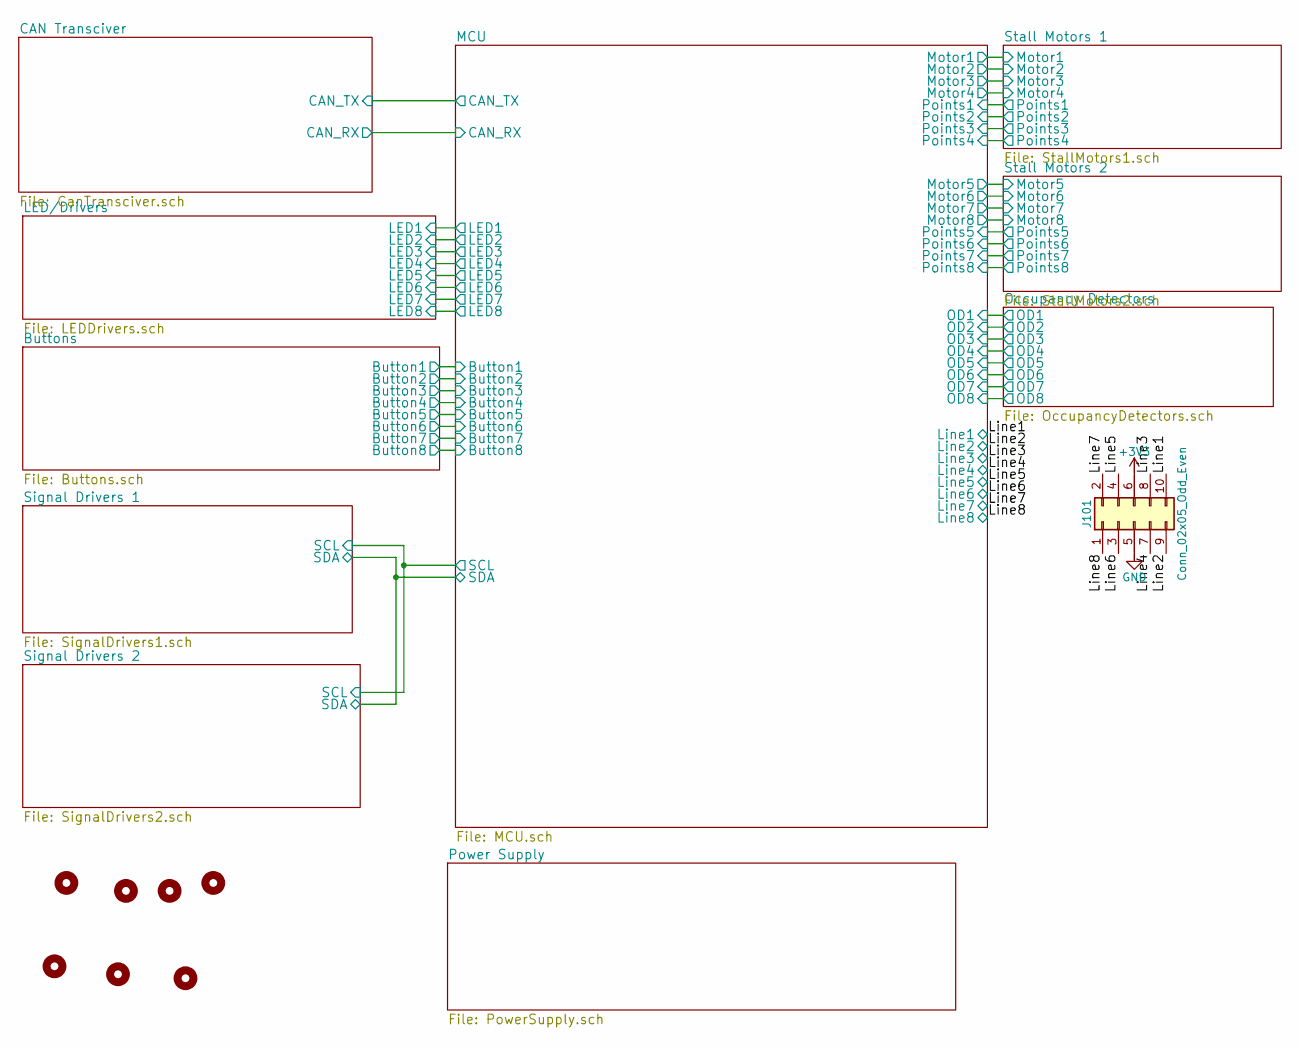
[picture p86: schematic ESP32-S3-MegaMultiFunction.sch]

Parts:
FD101, FD102, FD103: Fiduial; Fiducial_Modern_SilkscreenTop
J101: Conn_02x05_Odd_Even; IDC_Header_Straight_10pins
MK101, MK102, MK103, MK104: Mounting_Hole; MountingHole_3.5mm

Connections:
/Line1: J101.10; also elsewhere on the board
/Line2: J101.9; also elsewhere on the board
/Line3: J101.8; also elsewhere on the board
/Line4: J101.7; also elsewhere on the board
/Line5: J101.4; also elsewhere on the board
/Line6: J101.3; also elsewhere on the board
/Line7: J101.2; also elsewhere on the board
/Line8: J101.1; also elsewhere on the board
GND: J101.5; also elsewhere on the board

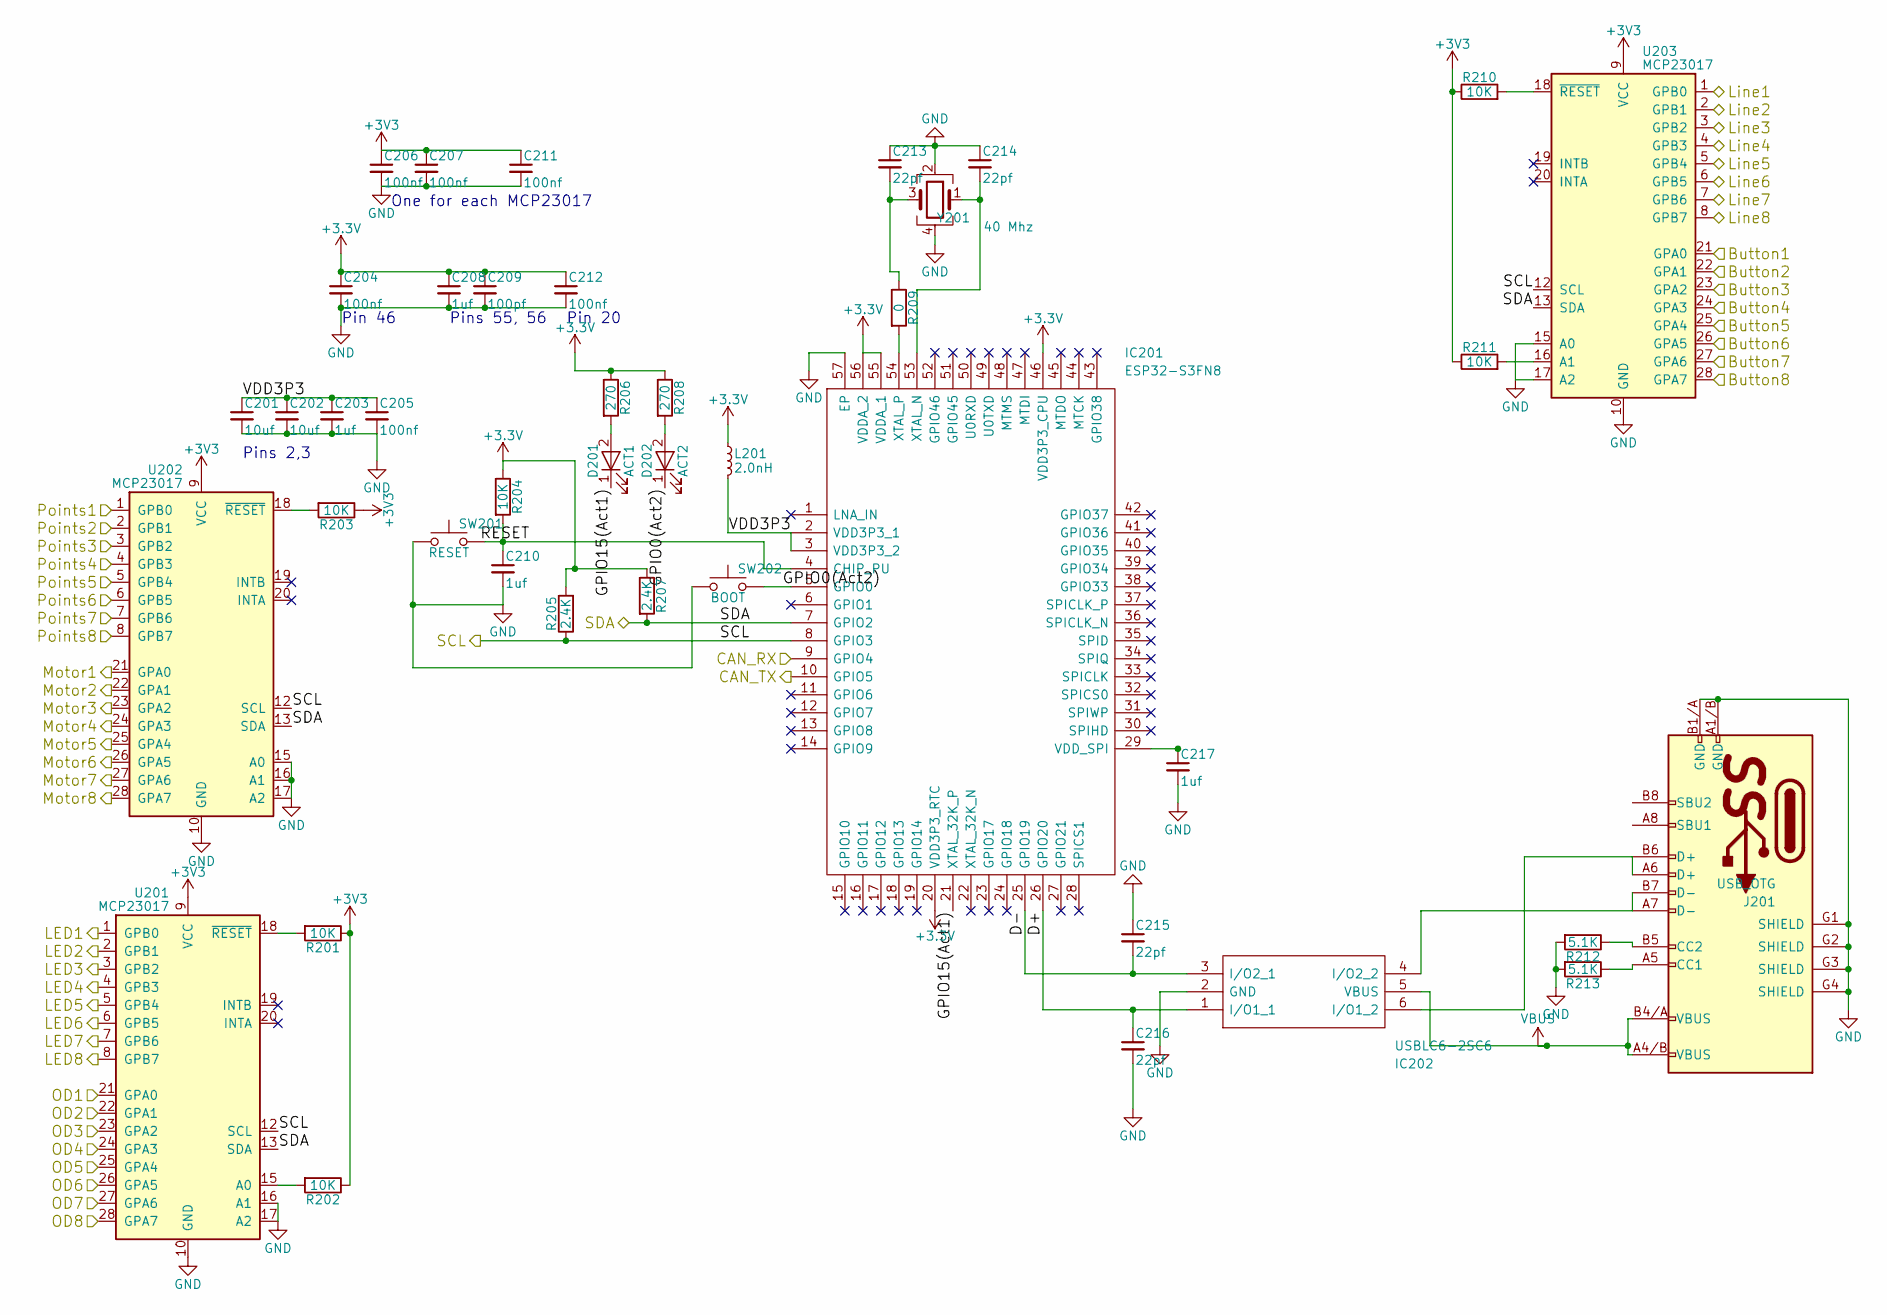
[picture p87: schematic MCU.sch, ESP32 S3 Multifunction Board]

Parts:
C201, C202: 10uf; C_0805; Mouser Part Number 187-CL21A106MQFNNNE
C203, C208, C210, C217: 1uf; C_0402; Mouser Part Number 80-C0402C101K8RAUTO
C204, C205, C206, C207, C211, C212: 100nf; C_0402; Mouser Part Number 710-885012105001
C209: 100pf; C_0402; Mouser Part Number 80-C0402C101K3RAUTO
C213, C214, C215, C216: 22pf; C_0402; Mouser Part Number 187-CL05C220JB5NNND
D201: ACT1; LED_0402; Mouser Part Number 710-150040GS73220
D202: ACT2; LED_0402; Mouser Part Number 710-150040SS73220
IC201: ESP32-S3FN8; QFN-56-1EP_7x7mm_Pitch0.4mm; Manufacturer_Part_Number ESP32-S3FN8; Mouser Part Number 356-ESP32-S3FN8
IC202: USBLC6-2SC6; SOT-23-6; Mouser Part Number 511-USBLC6-2SC6
J201: USB_OTG; GCT_USB4105-GF-A; Mouser Part Number 640-USB4105-GF-A-120
L201: 2.0nH; L_0402; Mouser Part Number 810-MLG1005S2N0ST000
R201, R202, R203, R204, R210, R211: 10K; R_0402; Mouser Part Number 603-RC0402JR-1310KL
R205, R207: 2.4K; R_0402; Mouser Part Number 71-CRCW06032K40JNEAC
R206, R208: 270; R_0402; Mouser Part Number 754-RR0510P-271D
R209: 0; R_0402; Mouser Part Number 71-CRCW04020000Z0EDC
R212, R213: 5.1K; R_0402
SW201: RESET; SW_SPST_B3U-1000P-B; Mouser Part Number 653-B3U-1000P-B
SW202: BOOT; SW_SPST_B3U-1000P-B; Mouser Part Number 653-B3U-1000P-B
U201, U202, U203: MCP23017; SOIC-28W_7.5x17.9mm_Pitch1.27mm
Y201: 40 Mhz; FA20_H; Mouser Part Number 732-FA-20H40MF10Z-W3

Connections:
/Buttons/Button1: U203.21 (GPA0); also elsewhere on the board
/Buttons/Button2: U203.22 (GPA1); also elsewhere on the board
/Buttons/Button3: U203.23 (GPA2); also elsewhere on the board
/Buttons/Button4: U203.24 (GPA3); also elsewhere on the board
/Buttons/Button5: U203.25 (GPA4); also elsewhere on the board
/Buttons/Button6: U203.26 (GPA5); also elsewhere on the board
/Buttons/Button7: U203.27 (GPA6); also elsewhere on the board
/Buttons/Button8: U203.28 (GPA7); also elsewhere on the board
/CAN Transciver/CAN_RX: IC201.9 (GPIO4); also elsewhere on the board
/CAN Transciver/CAN_TX: IC201.10 (GPIO5); also elsewhere on the board
/LED/Drivers/LED1: U201.1 (GPB0); also elsewhere on the board
/LED/Drivers/LED2: U201.2 (GPB1); also elsewhere on the board
/LED/Drivers/LED3: U201.3 (GPB2); also elsewhere on the board
/LED/Drivers/LED4: U201.4 (GPB3); also elsewhere on the board
/LED/Drivers/LED5: U201.5 (GPB4); also elsewhere on the board
/LED/Drivers/LED6: U201.6 (GPB5); also elsewhere on the board
/LED/Drivers/LED7: U201.7 (GPB6); also elsewhere on the board
/LED/Drivers/LED8: U201.8 (GPB7); also elsewhere on the board
/Line1: U203.1 (GPB0); also elsewhere on the board
/Line2: U203.2 (GPB1); also elsewhere on the board
/Line3: U203.3 (GPB2); also elsewhere on the board
/Line4: U203.4 (GPB3); also elsewhere on the board
/Line5: U203.5 (GPB4); also elsewhere on the board
/Line6: U203.6 (GPB5); also elsewhere on the board
/Line7: U203.7 (GPB6); also elsewhere on the board
/Line8: U203.8 (GPB7); also elsewhere on the board
/MCU/D+: C216.1, IC201.26 (GPIO20), IC202.1 (I/O1_1)
/MCU/D-: C215.2, IC201.25 (GPIO19), IC202.3 (I/O2_1)
/MCU/GPIO0(Act2): D202.1 (K), IC201.5 (GPIO0), SW202.2
/MCU/GPIO15(Act1): D201.1 (K), IC201.21 (XTAL_32K_P)
/MCU/Motor1: U202.21 (GPA0); also elsewhere on the board
/MCU/Motor2: U202.22 (GPA1); also elsewhere on the board
/MCU/Motor3: U202.23 (GPA2); also elsewhere on the board
/MCU/Motor4: U202.24 (GPA3); also elsewhere on the board
/MCU/Motor5: U202.25 (GPA4); also elsewhere on the board
/MCU/Motor6: U202.26 (GPA5); also elsewhere on the board
/MCU/Motor7: U202.27 (GPA6); also elsewhere on the board
/MCU/Motor8: U202.28 (GPA7); also elsewhere on the board
/MCU/OD1: U201.21 (GPA0); also elsewhere on the board
/MCU/OD2: U201.22 (GPA1); also elsewhere on the board
/MCU/OD3: U201.23 (GPA2); also elsewhere on the board
/MCU/OD4: U201.24 (GPA3); also elsewhere on the board
/MCU/OD5: U201.25 (GPA4); also elsewhere on the board
/MCU/OD6: U201.26 (GPA5); also elsewhere on the board
/MCU/OD7: U201.27 (GPA6); also elsewhere on the board
/MCU/OD8: U201.28 (GPA7); also elsewhere on the board
/MCU/Points1: U202.1 (GPB0); also elsewhere on the board
/MCU/Points2: U202.2 (GPB1); also elsewhere on the board
/MCU/Points3: U202.3 (GPB2); also elsewhere on the board
/MCU/Points4: U202.4 (GPB3); also elsewhere on the board
/MCU/Points5: U202.5 (GPB4); also elsewhere on the board
/MCU/Points6: U202.6 (GPB5); also elsewhere on the board
/MCU/Points7: U202.7 (GPB6); also elsewhere on the board
/MCU/Points8: U202.8 (GPB7); also elsewhere on the board
/MCU/RESET: C210.1, IC201.4 (CHIP_PU), R204.2, SW201.2
/MCU/SCL: IC201.8 (GPIO3), R205.1, U201.12 (SCL), U202.12 (SCL), U203.12 (SCL); also elsewhere on the board
/MCU/SDA: IC201.7 (GPIO2), R207.2, U201.13 (SDA), U202.13 (SDA), U203.13 (SDA); also elsewhere on the board
/MCU/VDD3P3: C201.1, C202.1, C203.1, C205.1, IC201.2 (VDD3P3_1), IC201.3 (VDD3P3_2), L201.2
GND: C201.2, C202.2, C203.2, C204.2, C205.2, C206.2, C207.2, C208.2, C209.2, C210.2, C211.2, C212.2, C213.1, C214.1, C215.1, C216.2, C217.2, IC201.57 (EP), IC202.2 (GND), J201.A1/B (GND), J201.B1/A (GND), J201.G1 (SHIELD), J201.G2 (SHIELD), J201.G3 (SHIELD), J201.G4 (SHIELD), R212.2, R213.2, SW201.1, SW202.1, U201.10 (GND), U201.16 (A1), U201.17 (A2), U202.10 (GND), U202.15 (A0), U202.16 (A1), U202.17 (A2), U203.10 (GND), U203.15 (A0), U203.17 (A2), Y201.2, Y201.4; also elsewhere on the board
unnamed: C213.2, R209.1, Y201.3
unnamed: C214.2, IC201.53 (XTAL_N), Y201.1
unnamed: C217.1, IC201.29 (VDD_SPI)
unnamed: D201.2 (A), R206.2
unnamed: D202.2 (A), R208.2
unnamed: IC201.54 (XTAL_P), R209.2
unnamed: IC202.4 (I/O2_2), J201.A7 (D-), J201.B7 (D-)
unnamed: IC202.6 (I/O1_2), J201.A6 (D+), J201.B6 (D+)
unnamed: J201.A5 (CC1), R213.1
unnamed: J201.B5 (CC2), R212.1
unnamed: R201.2, U201.18 (~RESET)
unnamed: R202.2, U201.15 (A0)
unnamed: R203.2, U202.18 (~RESET)
unnamed: R210.2, U203.18 (~RESET)
unnamed: R211.2, U203.16 (A1)
VBUS: IC202.5 (VBUS), J201.A4/B (VBUS), J201.B4/A (VBUS); also elsewhere on the board

Notes on the sheet:
Pins 2,3
Pin 46
Pins 55, 56
Pin 20
One for each MCP23017


Parts:
C301: .1 uf; C_0603; Mouser Part Number 710-885012206095
C302: 15 uf 15V; CP_Elec_4x5.7; Mouser Part Number 647-UUD1C150MCL
C303: 47 nf; C_0603; Mouser Part Number 710-885012206093
D301, D302: DFLS240-7; D_PowerDI-123; Mouser Part Number 621-DFLS240-7
J301, J302: RJ45; RJ45_8N-S; Mouser Part Number 710-615008144221
JP301: Termination; Pin_Header_Straight_2x02_Pitch2.54mm; Mouser Part Number 649-67997-404HLF
R301, R302: 60 Ohms; R_1206; Mouser Part Number 71-CRCW120660R0KNAIF
T301: - 15 in +; TerminalBlock_Pheonix_MPT-2.54mm_2pol; Mouser Part Number 651-1725656
T302: - 15 out +; TerminalBlock_Pheonix_MPT-2.54mm_2pol; Mouser Part Number 651-1725656
U301: TCAN332DR; SOIC-8_3.9x4.9mm_Pitch1.27mm; Mouser Part Number 595-TCAN332DR

Connections:
/CAN Transciver/CANH: J301.1, J302.1, R301.1, U301.7 (CANH)
/CAN Transciver/CANL: J301.2, J302.2, R302.1, U301.6 (CANL)
/CAN Transciver/CAN_RX: U301.4 (R); also elsewhere on the board
/CAN Transciver/CAN_TX: U301.1 (D); also elsewhere on the board
CAN +12V: D301.1 (K), D302.2 (A), J301.8, J302.8; also elsewhere on the board
GND: C301.2, C302.2, C303.2, J301.3, J301.6, J301.7, J302.3, J302.6, J302.7, T301.2, T302.2, U301.2 (GND); also elsewhere on the board
unnamed: C303.1, JP301.3, JP301.4
unnamed: D301.2 (A), T301.1
unnamed: D302.1 (K), T302.1
unnamed: J301.4, J302.4
unnamed: J301.5, J302.5
unnamed: JP301.1, R301.2
unnamed: JP301.2, R302.2

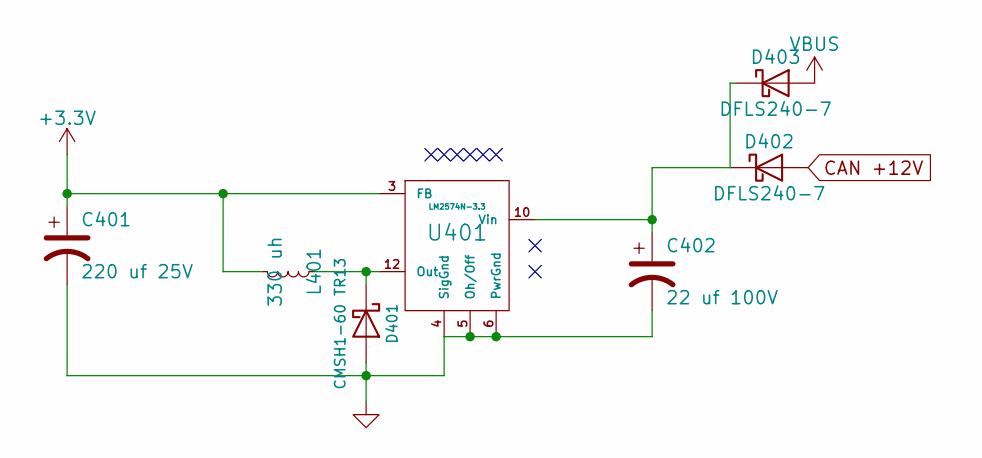
[picture p88: schematic PowerSupply.sch, ESP32 S3 Multifunction Board]

Parts:
C401: 220 uf 25V; CP_Elec_8x10; Mouser Part Number 647-UWT1E221MNL1GS
C402: 22 uf 100V; CP_Elec_8x10; Mouser Part Number 647-UUX2A220MNL6GS
D401: CMSH1-60 TR13; D_SMB; Mouser Part Number 610-CMSH1-60TR13
D402, D403: DFLS240-7; D_PowerDI-123; Mouser Part Number 621-DFLS240-7
L401: 330 uh; SRN1060; Mouser Part Number 652-SRN1060-331M
U401: LM2574N-3.3; SOIC-14_7.4x8.7mm_Pitch1.27mm; Mouser Part Number 926-LM2574MX33NOPB

Connections:
CAN +12V: D402.2 (A); also elsewhere on the board
GND: C401.2, C402.2, D401.2 (A), U401.4 (SigGnd), U401.5 (Oh/Off), U401.6 (PwrGnd); also elsewhere on the board
unnamed: C402.1, D402.1 (K), D403.1 (K), U401.10 (Vin)
unnamed: D401.1 (K), L401.1, U401.12 (Out)
VBUS: D403.2 (A); also elsewhere on the board

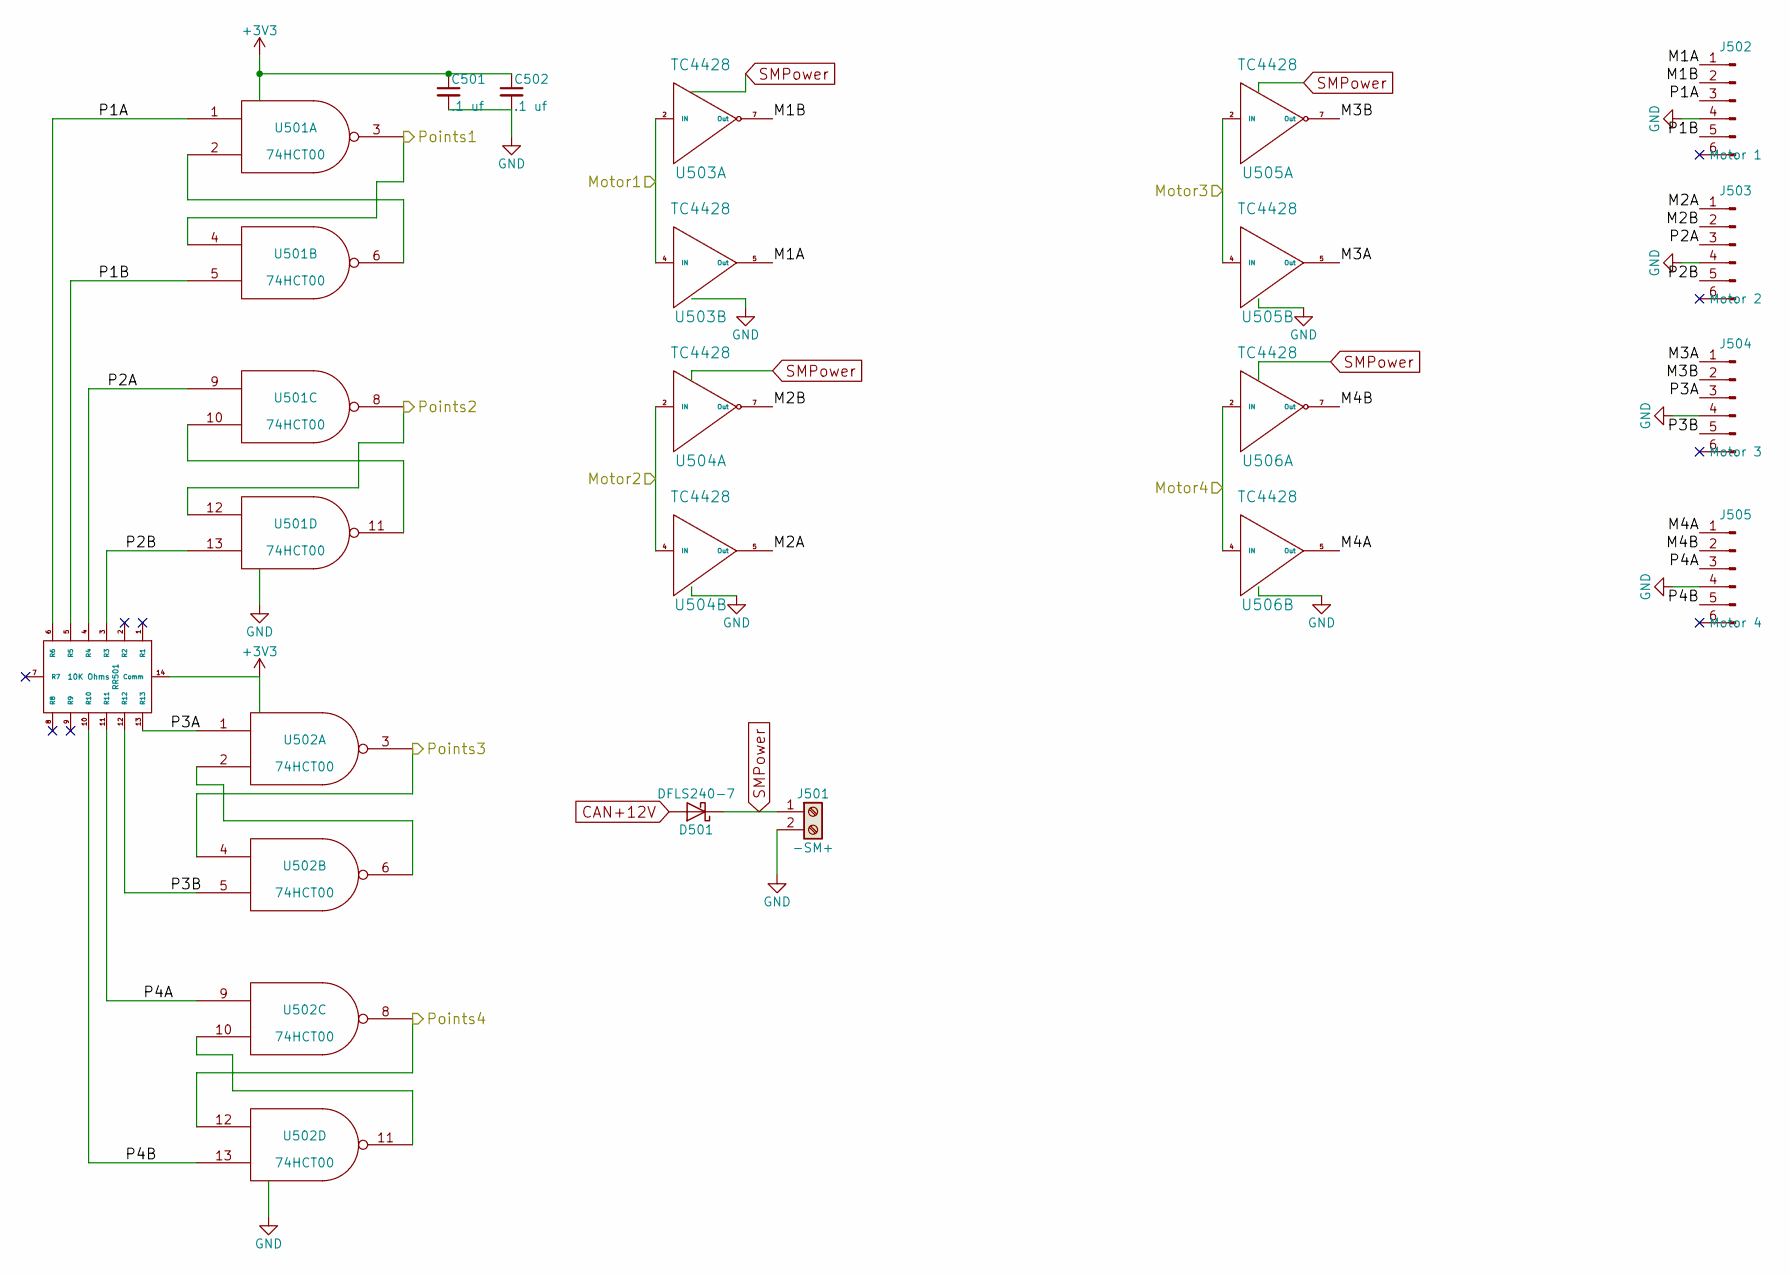
[picture p89: schematic StallMotors1.sch, ESP32 S3 Multifunction Board]

Parts:
C501, C502: .1 uf; C_0603; Mouser Part Number 710-885012206095
D501: DFLS240-7; D_PowerDI-123; Mouser Part Number 621-DFLS240-7
J501: -SM+; TerminalBlock_Pheonix_MPT-2.54mm_2pol; Mouser Part Number 651-172565
J502: Motor 1; 474817; Mouser Part Number 305-474817
J503: Motor 2; 474817; Mouser Part Number 305-474817
J504: Motor 3; 474817; Mouser Part Number 305-474817
J505: Motor 4; 474817; Mouser Part Number 305-474817
RR501: 10K Ohms; 4814P; Mouser Part Number 652-4814P-2LF-10K
U501, U502: 74HCT00; SOIC-14_3.9x8.7mm_Pitch1.27mm; Mouser Part Number 595-SN74AHC00D
U503, U504, U505, U506: TC4428; SOIC-8_3.9x4.9mm_Pitch1.27mm; Mouser Part Number 579-TC4428VOA

Connections:
/MCU/Motor1: U503.2 (IN), U503.4 (IN); also elsewhere on the board
/MCU/Motor2: U504.2 (IN), U504.4 (IN); also elsewhere on the board
/MCU/Motor3: U505.2 (IN), U505.4 (IN); also elsewhere on the board
/MCU/Motor4: U506.2 (IN), U506.4 (IN); also elsewhere on the board
/MCU/Points1: U501.3, U501.4; also elsewhere on the board
/MCU/Points2: U501.8, U501.12; also elsewhere on the board
/MCU/Points3: U502.3, U502.4; also elsewhere on the board
/MCU/Points4: U502.8, U502.12; also elsewhere on the board
/Stall Motors 1/M1A: J502.1, U503.5 (Out)
/Stall Motors 1/M1B: J502.2, U503.7 (Out)
/Stall Motors 1/M2A: J503.1, U504.5 (Out)
/Stall Motors 1/M2B: J503.2, U504.7 (Out)
/Stall Motors 1/M3A: J504.1, U505.5 (Out)
/Stall Motors 1/M3B: J504.2, U505.7 (Out)
/Stall Motors 1/M4A: J505.1, U506.5 (Out)
/Stall Motors 1/M4B: J505.2, U506.7 (Out)
/Stall Motors 1/P1A: J502.3, RR501.6 (R6), U501.1
/Stall Motors 1/P1B: J502.5, RR501.5 (R5), U501.5
/Stall Motors 1/P2A: J503.3, RR501.4 (R4), U501.9
/Stall Motors 1/P2B: J503.5, RR501.3 (R3), U501.13
/Stall Motors 1/P3A: J504.3, RR501.13 (R13), U502.1
/Stall Motors 1/P3B: J504.5, RR501.12 (R12), U502.5
/Stall Motors 1/P4A: J505.3, RR501.11 (R11), U502.9
/Stall Motors 1/P4B: J505.5, RR501.10 (R10), U502.13
CAN +12V: D501.2 (A); also elsewhere on the board
GND: C501.2, C502.2, J501.2, J502.4, J503.4, J504.4, J505.4, U501.7 (GND), U502.7 (GND), U503.3 (GND), U504.3 (GND), U505.3 (GND), U506.3 (GND); also elsewhere on the board
unnamed: U501.2, U501.6
unnamed: U501.10, U501.11
unnamed: U502.2, U502.6
unnamed: U502.10, U502.11
SMPower: D501.1 (K), J501.1, U503.6 (Vdd), U504.6 (Vdd), U505.6 (Vdd), U506.6 (Vdd); also elsewhere on the board
