RobertPHeller/ESP32-LCC/ESP32-S3-MegaMultiFunction/ESP32-S3-MegaMultiFunction.kicad_pcb

## KiCad design ESP32-S3-MegaMultiFunction/ESP32-S3-MegaMultiFunction.kicad_pcb (continued)

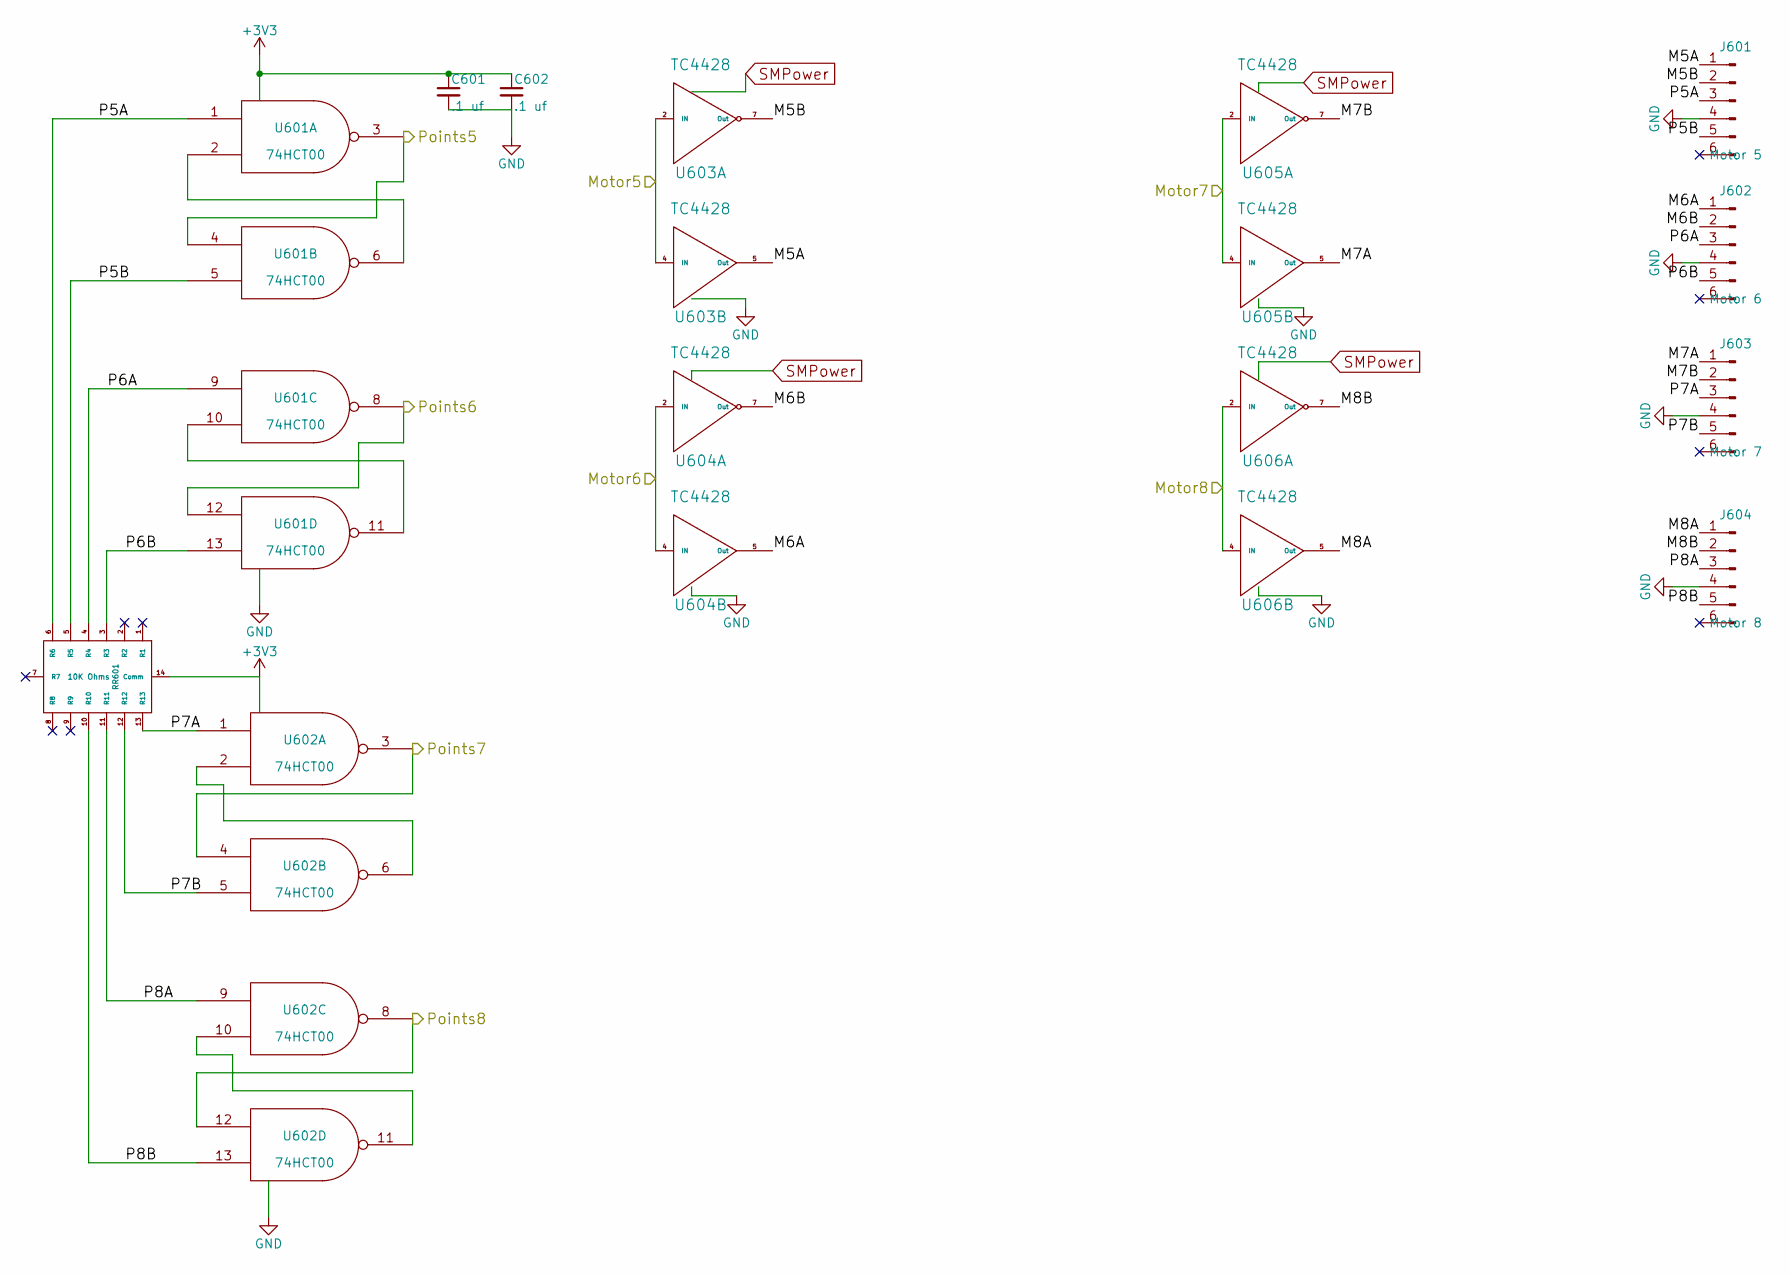
[picture p90: schematic StallMotors2.sch, ESP32 S3 Multifunction Board]

Parts:
C601, C602: .1 uf; C_0603; Mouser Part Number 710-885012206095
J601: Motor 5; 474817; Mouser Part Number 305-474817
J602: Motor 6; 474817; Mouser Part Number 305-474817
J603: Motor 7; 474817; Mouser Part Number 305-474817
J604: Motor 8; 474817; Mouser Part Number 305-474817
RR601: 10K Ohms; 4814P; Mouser Part Number 652-4814P-2LF-10K
U601, U602: 74HCT00; SOIC-14_3.9x8.7mm_Pitch1.27mm; Mouser Part Number 595-SN74AHC00D
U603, U604, U605, U606: TC4428; SOIC-8_3.9x4.9mm_Pitch1.27mm; Mouser Part Number 579-TC4428VOA

Connections:
/MCU/Motor5: U603.2 (IN), U603.4 (IN); also elsewhere on the board
/MCU/Motor6: U604.2 (IN), U604.4 (IN); also elsewhere on the board
/MCU/Motor7: U605.2 (IN), U605.4 (IN); also elsewhere on the board
/MCU/Motor8: U606.2 (IN), U606.4 (IN); also elsewhere on the board
/MCU/Points5: U601.3, U601.4; also elsewhere on the board
/MCU/Points6: U601.8, U601.12; also elsewhere on the board
/MCU/Points7: U602.3, U602.4; also elsewhere on the board
/MCU/Points8: U602.8, U602.12; also elsewhere on the board
/Stall Motors 2/M5A: J601.1, U603.5 (Out)
/Stall Motors 2/M5B: J601.2, U603.7 (Out)
/Stall Motors 2/M6A: J602.1, U604.5 (Out)
/Stall Motors 2/M6B: J602.2, U604.7 (Out)
/Stall Motors 2/M7A: J603.1, U605.5 (Out)
/Stall Motors 2/M7B: J603.2, U605.7 (Out)
/Stall Motors 2/M8A: J604.1, U606.5 (Out)
/Stall Motors 2/M8B: J604.2, U606.7 (Out)
/Stall Motors 2/P5A: J601.3, RR601.6 (R6), U601.1
/Stall Motors 2/P5B: J601.5, RR601.5 (R5), U601.5
/Stall Motors 2/P6A: J602.3, RR601.4 (R4), U601.9
/Stall Motors 2/P6B: J602.5, RR601.3 (R3), U601.13
/Stall Motors 2/P7A: J603.3, RR601.13 (R13), U602.1
/Stall Motors 2/P7B: J603.5, RR601.12 (R12), U602.5
/Stall Motors 2/P8A: J604.3, RR601.11 (R11), U602.9
/Stall Motors 2/P8B: J604.5, RR601.10 (R10), U602.13
GND: C601.2, C602.2, J601.4, J602.4, J603.4, J604.4, U601.7 (GND), U602.7 (GND), U603.3 (GND), U604.3 (GND), U605.3 (GND), U606.3 (GND); also elsewhere on the board
unnamed: U601.2, U601.6
unnamed: U601.10, U601.11
unnamed: U602.2, U602.6
unnamed: U602.10, U602.11
SMPower: U603.6 (Vdd), U604.6 (Vdd), U605.6 (Vdd), U606.6 (Vdd); also elsewhere on the board

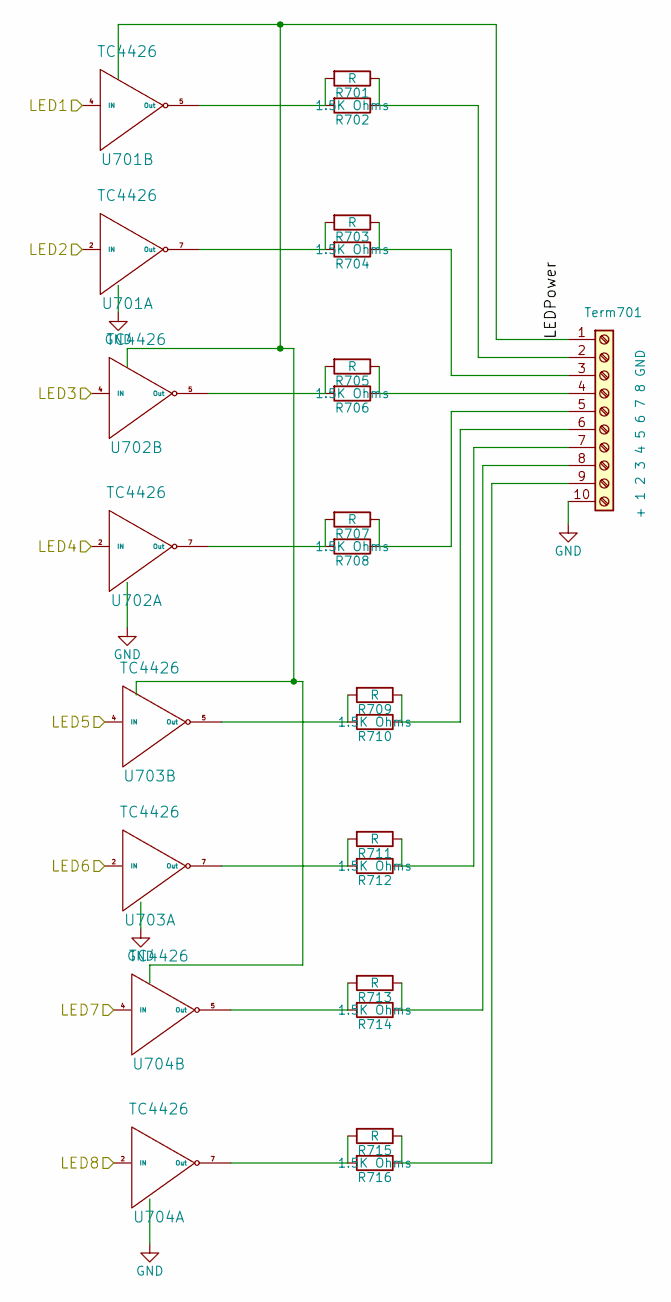
[picture p91: schematic LEDDrivers.sch, ESP32 S3 Multifunction Board]

Parts:
R701, R703, R705, R707, R709, R711, R713, R715: R; R_Axial_DIN0207_L6.3mm_D2.5mm_P7.62mm_Horizontal
R702, R704, R706, R708, R710, R712, R714, R716: 1.5K Ohms; R_0603; Mouser Part Number 71-CRCW06031K50JNEAC
Term701: + 1 2 3 4 5 6 7 8 GND; TerminalBlock_Pheonix_MPT-2.54mm_10pol; Mouser Part Number 651-1725737
U701, U702, U703, U704: TC4426; SOIC-8_3.9x4.9mm_Pitch1.27mm; Mouser Part Number 579-TC1426COA713

Connections:
/LED/Drivers/LED1: U701.4 (IN); also elsewhere on the board
/LED/Drivers/LED2: U701.2 (IN); also elsewhere on the board
/LED/Drivers/LED3: U702.4 (IN); also elsewhere on the board
/LED/Drivers/LED4: U702.2 (IN); also elsewhere on the board
/LED/Drivers/LED5: U703.4 (IN); also elsewhere on the board
/LED/Drivers/LED6: U703.2 (IN); also elsewhere on the board
/LED/Drivers/LED7: U704.4 (IN); also elsewhere on the board
/LED/Drivers/LED8: U704.2 (IN); also elsewhere on the board
GND: Term701.10, U701.3 (GND), U702.3 (GND), U703.3 (GND), U704.3 (GND); also elsewhere on the board
unnamed: R701.1, R702.1, Term701.2
unnamed: R701.2, R702.2, U701.5 (Out)
unnamed: R703.1, R704.1, Term701.3
unnamed: R703.2, R704.2, U701.7 (Out)
unnamed: R705.1, R706.1, Term701.4
unnamed: R705.2, R706.2, U702.5 (Out)
unnamed: R707.1, R708.1, Term701.5
unnamed: R707.2, R708.2, U702.7 (Out)
unnamed: R709.1, R710.1, Term701.6
unnamed: R709.2, R710.2, U703.5 (Out)
unnamed: R711.1, R712.1, Term701.7
unnamed: R711.2, R712.2, U703.7 (Out)
unnamed: R713.1, R714.1, Term701.8
unnamed: R713.2, R714.2, U704.5 (Out)
unnamed: R715.1, R716.1, Term701.9
unnamed: R715.2, R716.2, U704.7 (Out)
VPower: Term701.1, U701.6 (VPower), U702.6 (VPower), U703.6 (VPower), U704.6 (VPower)

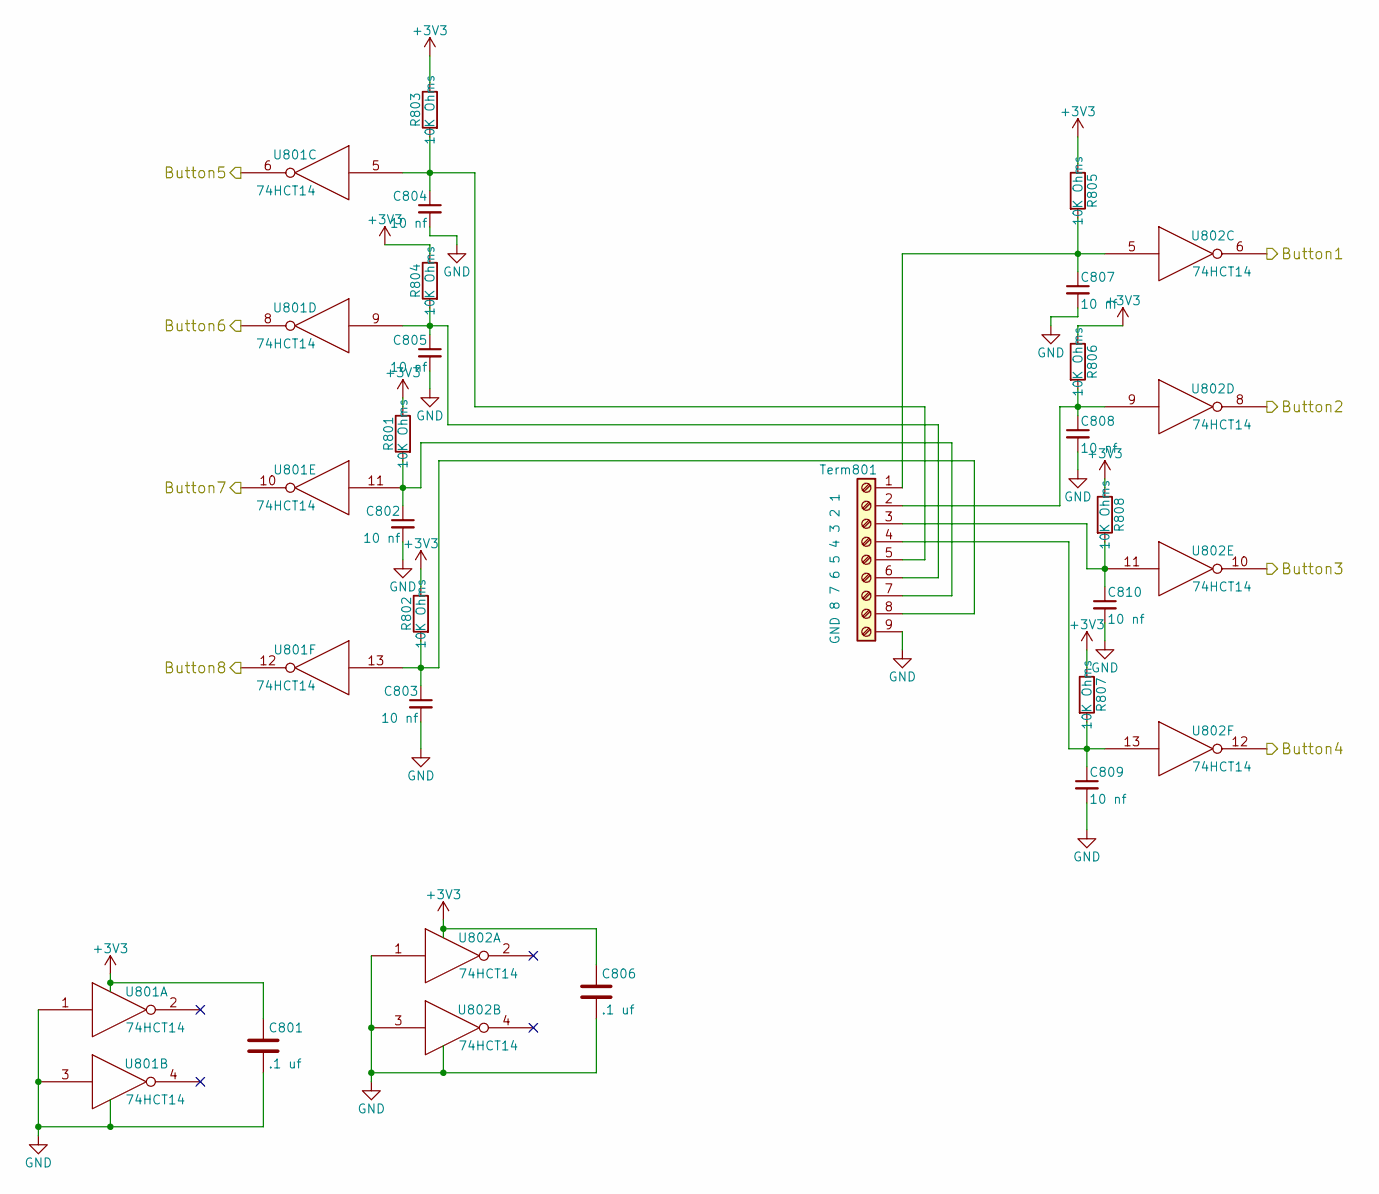
[picture p92: schematic Buttons.sch, ESP32 S3 Multifunction Board]

Parts:
C801, C806: .1 uf; C_0603; Mouser Part Number 710-885012206095
C802, C803, C804, C805, C807, C808, C809, C810: 10 nf; C_0603; Mouser Part Number 710-885382206002
R801, R802, R803, R804, R805, R806, R807, R808: 10K Ohms; R_0603; Mouser Part Number 71-CRCW060310K0JNEBC
Term801: GND 8 7 6 5 4 3 2 1; TerminalBlock_Pheonix_MPT-2.54mm_9pol; Mouser Part Number 651-1725724
U801: 74HCT14; SOIC-14_3.9x8.7mm_Pitch1.27mm
U802: 74HCT14; SOIC-14_3.9x8.7mm_Pitch1.27mm; Mouser Part Number 595-CD74HC14M

Connections:
/Buttons/Button1: U802.6; also elsewhere on the board
/Buttons/Button2: U802.8; also elsewhere on the board
/Buttons/Button3: U802.10; also elsewhere on the board
/Buttons/Button4: U802.12; also elsewhere on the board
/Buttons/Button5: U801.6; also elsewhere on the board
/Buttons/Button6: U801.8; also elsewhere on the board
/Buttons/Button7: U801.10; also elsewhere on the board
/Buttons/Button8: U801.12; also elsewhere on the board
GND: C801.2, C802.2, C803.2, C804.2, C805.2, C806.2, C807.2, C808.2, C809.2, C810.2, Term801.9, U801.1, U801.3, U801.7 (GND), U802.1, U802.3, U802.7 (GND); also elsewhere on the board
unnamed: C802.1, R801.2, Term801.7, U801.11
unnamed: C803.1, R802.2, Term801.8, U801.13
unnamed: C804.1, R803.2, Term801.5, U801.5
unnamed: C805.1, R804.2, Term801.6, U801.9
unnamed: C807.1, R805.2, Term801.1, U802.5
unnamed: C808.1, R806.2, Term801.2, U802.9
unnamed: C809.1, R807.2, Term801.4, U802.13
unnamed: C810.1, R808.2, Term801.3, U802.11

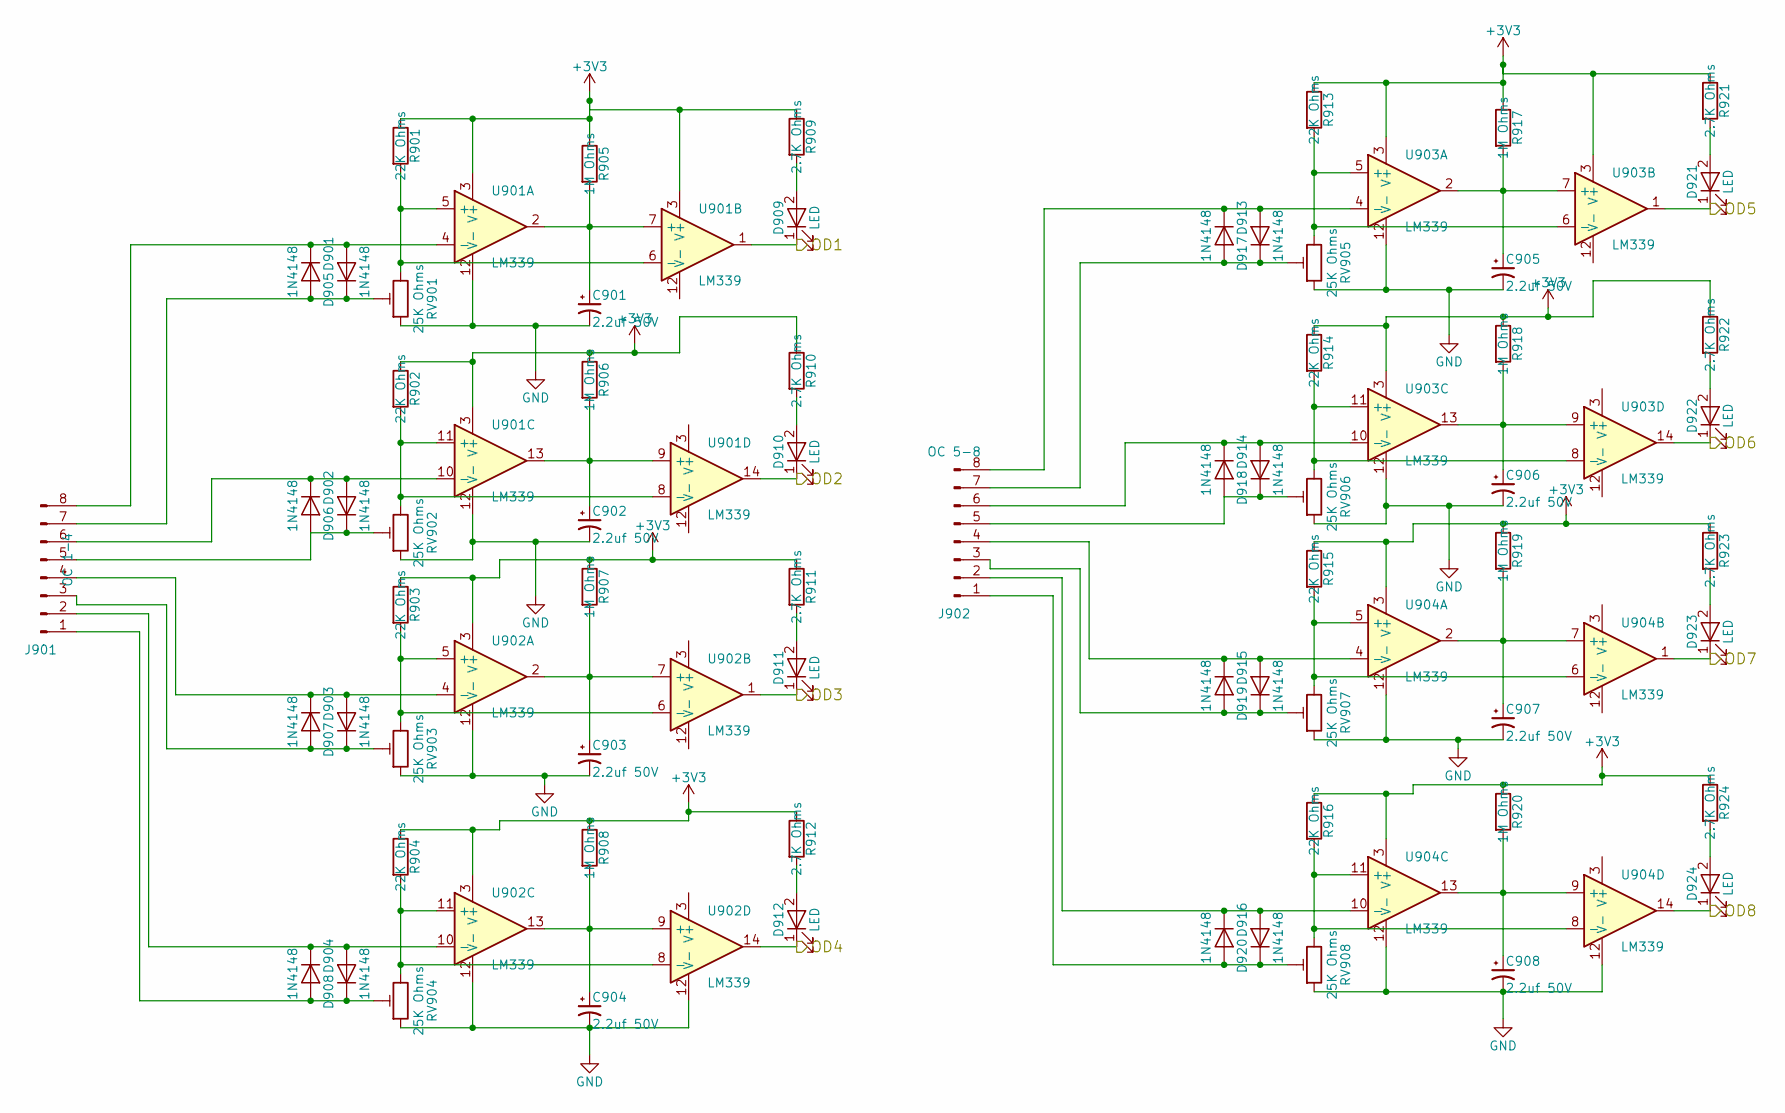
[picture p93: schematic OccupancyDetectors.sch, ESP32 S3 Multifunction Board]

Parts:
C901, C902, C903, C904, C905, C906, C907, C908: 2.2uf 50V; CP_Elec_4x5.7; Mouser Part Number 710-865080140002
D901, D902, D903, D904, D905, D906, D907, D908, D913, D914, D915, D916, D917, D918, D919, D920: 1N4148; D_SOD-323; Mouser Part Number 750-1N4148WS-HF
D909, D910, D911, D912, D921, D922, D923, D924: LED; LED_0603; Mouser Part Number 710-150060SS55040
J901: OC 1-4; 474818; Mouser Part Number 305-474818
J902: OC 5-8; 474818; Mouser Part Number 305-474818
R901, R902, R903, R904, R913, R914, R915, R916: 22K Ohms; R_0603; Mouser Part Number 71-RCG060322K0JNEA
R905, R906, R907, R908, R917, R918, R919, R920: 1M Ohms; R_0603; Mouser Part Number 71-CRCW06031M00JNEAC
R909, R910, R911, R912, R921, R922, R923, R924: 2.7K Ohms; R_0603; Mouser Part Number 71-CRCW06032K70JNEAC
RV901, RV902, RV903, RV904, RV905, RV906, RV907, RV908: 25K Ohms; Potentiometer_Trimmer_Bourns_3214J; Mouser Part Number 652-3314J-1-253E
U901, U903: LM339; SOIC-14_3.9x8.7mm_Pitch1.27mm; Mouser Part Number 595-LM339DR
U902, U904: LM339; SOIC-14_3.9x8.7mm_Pitch1.27mm

Connections:
/MCU/OD1: D909.1 (K), U901.1; also elsewhere on the board
/MCU/OD2: D910.1 (K), U901.14; also elsewhere on the board
/MCU/OD3: D911.1 (K), U902.1; also elsewhere on the board
/MCU/OD4: D912.1 (K), U902.14; also elsewhere on the board
/MCU/OD5: D921.1 (K), U903.1; also elsewhere on the board
/MCU/OD6: D922.1 (K), U903.14; also elsewhere on the board
/MCU/OD7: D923.1 (K), U904.1; also elsewhere on the board
/MCU/OD8: D924.1 (K), U904.14; also elsewhere on the board
GND: C901.2, C902.2, C903.2, C904.2, C905.2, C906.2, C907.2, C908.2, RV901.1, RV902.1, RV903.1, RV904.1, RV905.1, RV906.1, RV907.1, RV908.1, U901.12 (V-), U902.12 (V-), U903.12 (V-), U904.12 (V-); also elsewhere on the board
unnamed: C901.1, R905.2, U901.2, U901.7 (+)
unnamed: C902.1, R906.2, U901.9 (+), U901.13
unnamed: C903.1, R907.2, U902.2, U902.7 (+)
unnamed: C904.1, R908.2, U902.9 (+), U902.13
unnamed: C905.1, R917.2, U903.2, U903.7 (+)
unnamed: C906.1, R918.2, U903.9 (+), U903.13
unnamed: C907.1, R919.2, U904.2, U904.7 (+)
unnamed: C908.1, R920.2, U904.9 (+), U904.13
unnamed: D901.1 (K), D905.2 (A), J901.8, U901.4 (-)
unnamed: D901.2 (A), D905.1 (K), J901.7, RV901.2
unnamed: D902.1 (K), D906.2 (A), J901.6, U901.10 (-)
unnamed: D902.2 (A), D906.1 (K), J901.5, RV902.2
unnamed: D903.1 (K), D907.2 (A), J901.4, U902.4 (-)
unnamed: D903.2 (A), D907.1 (K), J901.3, RV903.2
unnamed: D904.1 (K), D908.2 (A), J901.2, U902.10 (-)
unnamed: D904.2 (A), D908.1 (K), J901.1, RV904.2
unnamed: D909.2 (A), R909.2
unnamed: D910.2 (A), R910.2
unnamed: D911.2 (A), R911.2
unnamed: D912.2 (A), R912.2
unnamed: D913.1 (K), D917.2 (A), J902.8, U903.4 (-)
unnamed: D913.2 (A), D917.1 (K), J902.7, RV905.2
unnamed: D914.1 (K), D918.2 (A), J902.6, U903.10 (-)
unnamed: D914.2 (A), D918.1 (K), J902.5, RV906.2
unnamed: D915.1 (K), D919.2 (A), J902.4, U904.4 (-)
unnamed: D915.2 (A), D919.1 (K), J902.3, RV907.2
unnamed: D916.1 (K), D920.2 (A), J902.2, U904.10 (-)
unnamed: D916.2 (A), D920.1 (K), J902.1, RV908.2
unnamed: D921.2 (A), R921.2
unnamed: D922.2 (A), R922.2
unnamed: D923.2 (A), R923.2
unnamed: D924.2 (A), R924.2
unnamed: R901.2, RV901.3, U901.5 (+), U901.6 (-)
unnamed: R902.2, RV902.3, U901.8 (-), U901.11 (+)
unnamed: R903.2, RV903.3, U902.5 (+), U902.6 (-)
unnamed: R904.2, RV904.3, U902.8 (-), U902.11 (+)
unnamed: R913.2, RV905.3, U903.5 (+), U903.6 (-)
unnamed: R914.2, RV906.3, U903.8 (-), U903.11 (+)
unnamed: R915.2, RV907.3, U904.5 (+), U904.6 (-)
unnamed: R916.2, RV908.3, U904.8 (-), U904.11 (+)

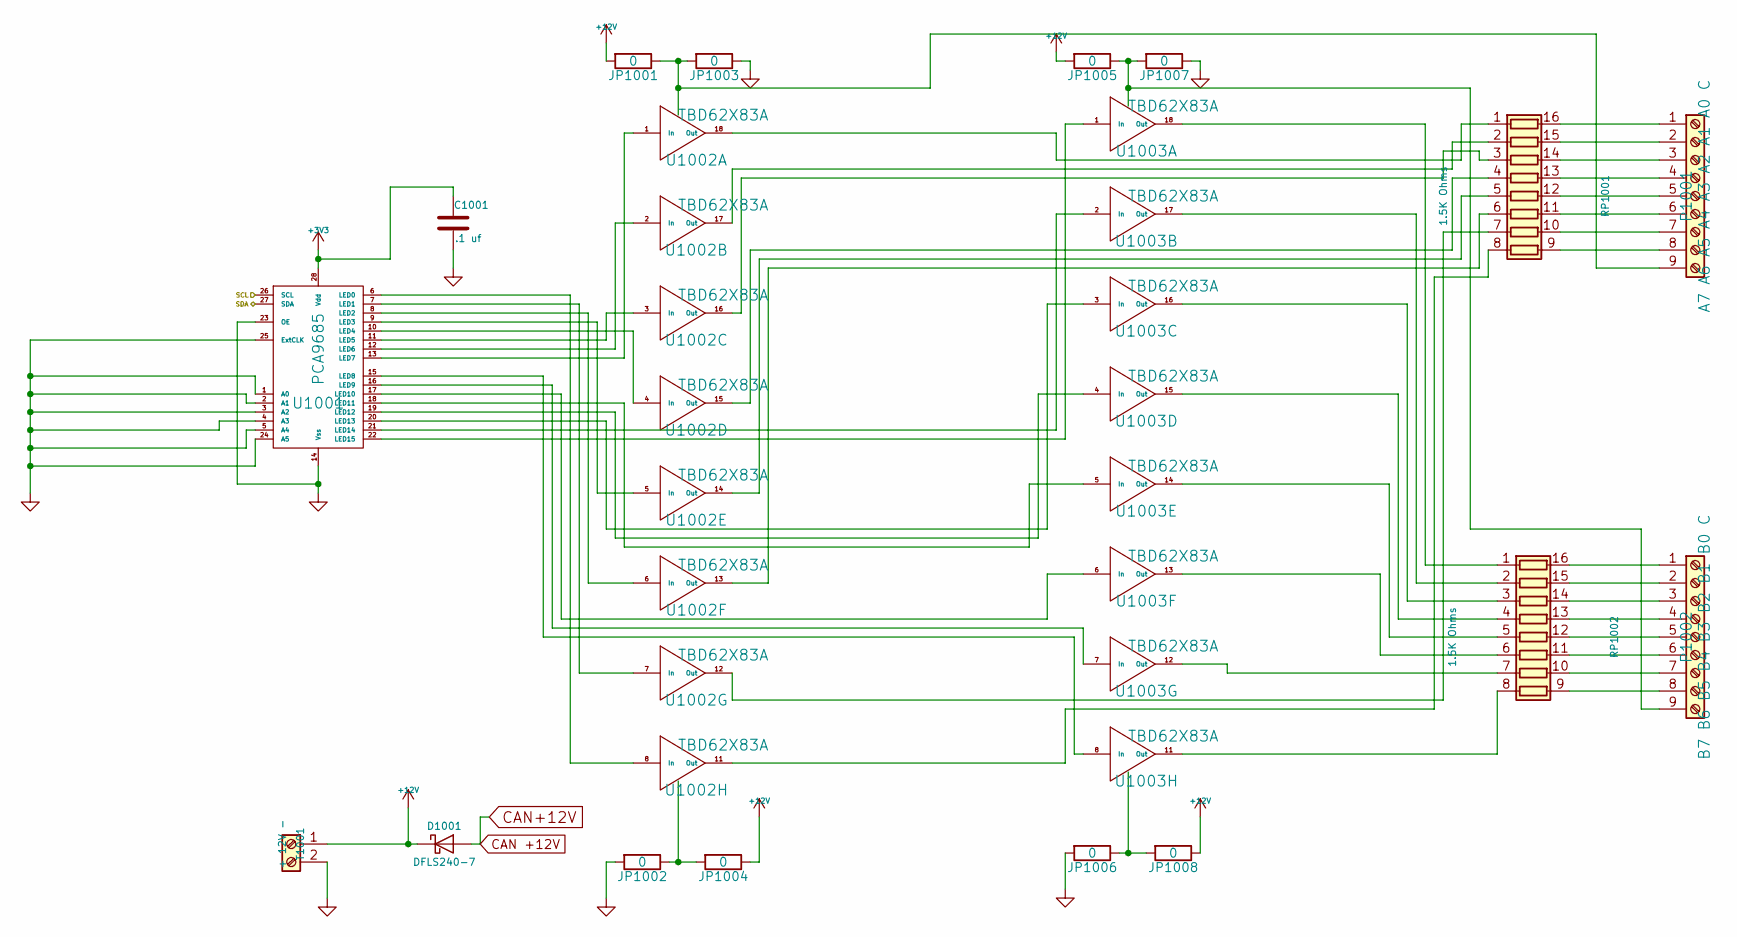
[picture p94: schematic SignalDrivers1.sch, ESP32 S3 Multifunction Board]

Parts:
C1001: .1 uf; C_0603; Mouser Part Number 710-885012206095
D1001: DFLS240-7; D_PowerDI-123; Mouser Part Number 621-DFLS240-7
JP1001, JP1002, JP1003, JP1004, JP1005, JP1006, JP1007, JP1008: 0; R_1206; Mouser Part Number 71-CRCW12060000Z0EBC
P1001: A7 A6 A5 A4 A3 A2 A1 A0 C; TerminalBlock_Pheonix_MPT-2.54mm_9pol; Mouser Part Number 651-1725724
P1002: B7 B6 B5 B4 B3 B2 B1 B0 C; TerminalBlock_Pheonix_MPT-2.54mm_9pol; Mouser Part Number 651-1725724
RP1001, RP1002: 1.5K Ohms; 4816P; Mouser Part Number 652-4816P-T1LF-1.5K
T1001: + 12V -; TerminalBlock_Pheonix_MPT-2.54mm_2pol; Mouser Part Number 651-1725656
U1001: PCA9685; TSSOP-28_4.4x9.7mm_Pitch0.65mm; Mouser Part Number 771-PCA9685PW,118
U1002, U1003: TBD62X83A; SOIC-18W_7.5x11.6mm_Pitch1.27mm; Mouser Part Number 757-TBD62083AFG or 757-TBD62783AFG

Connections:
+12V: D1001.1 (K), JP1001.2, JP1004.1, JP1005.2, JP1008.1, T1001.1; also elsewhere on the board
/MCU/SCL: U1001.26 (SCL); also elsewhere on the board
/MCU/SDA: U1001.27 (SDA); also elsewhere on the board
CAN +12V: D1001.2 (A); also elsewhere on the board
GND: C1001.2, JP1002.2, JP1003.1, JP1006.2, JP1007.1, T1001.2, U1001.1 (A0), U1001.2 (A1), U1001.3 (A2), U1001.4 (A3), U1001.5 (A4), U1001.14 (Vss), U1001.23 (OE), U1001.24 (A5), U1001.25 (ExtCLK); also elsewhere on the board
unnamed: JP1001.1, JP1003.2, P1001.9, U1002.10 (OC)
unnamed: JP1002.1, JP1004.2, U1002.9 (IC)
unnamed: JP1005.1, JP1007.2, P1002.9, U1003.10 (OC)
unnamed: JP1006.1, JP1008.2, U1003.9 (IC)
unnamed: P1001.1, RP1001.16 (R1.2)
unnamed: P1001.2, RP1001.15 (R2.2)
unnamed: P1001.3, RP1001.14 (R3.2)
unnamed: P1001.4, RP1001.13 (R4.2)
unnamed: P1001.5, RP1001.12 (R5.2)
unnamed: P1001.6, RP1001.11 (R6.2)
unnamed: P1001.7, RP1001.10 (R7.2)
unnamed: P1001.8, RP1001.9 (R8.2)
unnamed: P1002.1, RP1002.16 (R1.2)
unnamed: P1002.2, RP1002.15 (R2.2)
unnamed: P1002.3, RP1002.14 (R3.2)
unnamed: P1002.4, RP1002.13 (R4.2)
unnamed: P1002.5, RP1002.12 (R5.2)
unnamed: P1002.6, RP1002.11 (R6.2)
unnamed: P1002.7, RP1002.10 (R7.2)
unnamed: P1002.8, RP1002.9 (R8.2)
unnamed: RP1001.1 (R1.1), U1002.18 (Out)
unnamed: RP1001.2 (R2.1), U1002.17 (Out)
unnamed: RP1001.3 (R3.1), U1002.16 (Out)
unnamed: RP1001.4 (R4.1), U1002.15 (Out)
unnamed: RP1001.5 (R5.1), U1002.14 (Out)
unnamed: RP1001.6 (R6.1), U1002.13 (Out)
unnamed: RP1001.7 (R7.1), U1002.12 (Out)
unnamed: RP1001.8 (R8.1), U1002.11 (Out)
unnamed: RP1002.1 (R1.1), U1003.18 (Out)
unnamed: RP1002.2 (R2.1), U1003.17 (Out)
unnamed: RP1002.3 (R3.1), U1003.16 (Out)
unnamed: RP1002.4 (R4.1), U1003.15 (Out)
unnamed: RP1002.5 (R5.1), U1003.14 (Out)
unnamed: RP1002.6 (R6.1), U1003.13 (Out)
unnamed: RP1002.7 (R7.1), U1003.12 (Out)
unnamed: RP1002.8 (R8.1), U1003.11 (Out)
unnamed: U1001.6 (LED0), U1002.8 (In)
unnamed: U1001.7 (LED1), U1002.7 (In)
unnamed: U1001.8 (LED2), U1002.6 (In)
unnamed: U1001.9 (LED3), U1002.5 (In)
unnamed: U1001.10 (LED4), U1002.4 (In)
unnamed: U1001.11 (LED5), U1002.3 (In)
unnamed: U1001.12 (LED6), U1002.2 (In)
unnamed: U1001.13 (LED7), U1002.1 (In)
unnamed: U1001.15 (LED8), U1003.8 (In)
unnamed: U1001.16 (LED9), U1003.7 (In)
unnamed: U1001.17 (LED10), U1003.6 (In)
unnamed: U1001.18 (LED11), U1003.5 (In)
unnamed: U1001.19 (LED12), U1003.4 (In)
unnamed: U1001.20 (LED13), U1003.3 (In)
unnamed: U1001.21 (LED14), U1003.2 (In)
unnamed: U1001.22 (LED15), U1003.1 (In)

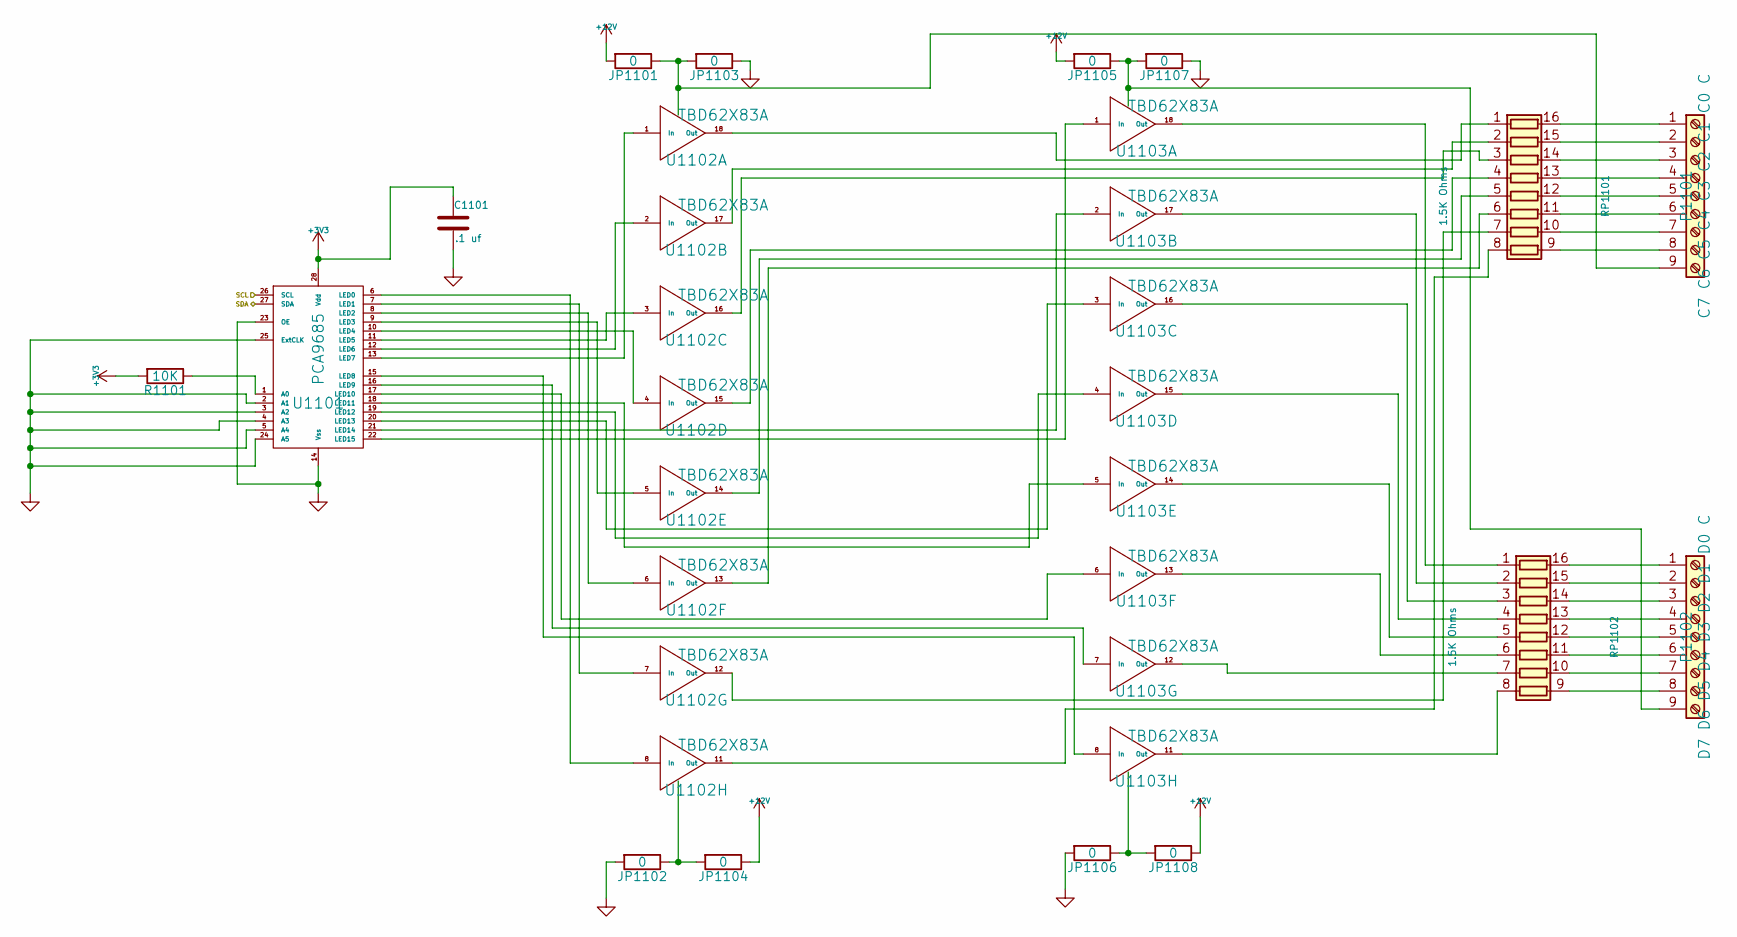
[picture p95: schematic SignalDrivers2.sch, ESP32 S3 Multifunction Board]

Parts:
C1101: .1 uf; C_0603; Mouser Part Number 710-885012206095
JP1101, JP1102, JP1103, JP1104, JP1105, JP1106, JP1107, JP1108: 0; R_1206; Mouser Part Number 71-CRCW12060000Z0EBC
P1101: C7 C6 C5 C4 C3 C2 C1 C0 C; TerminalBlock_Pheonix_MPT-2.54mm_9pol; Mouser Part Number 651-1725724
P1102: D7 D6 D5 D4 D3 D2 D1 D0 C; TerminalBlock_Pheonix_MPT-2.54mm_9pol; Mouser Part Number 651-1725724
R1101: 10K; R_0402
RP1101, RP1102: 1.5K Ohms; 4816P; Mouser Part Number 652-4816P-T1LF-1.5K
U1101: PCA9685; TSSOP-28_4.4x9.7mm_Pitch0.65mm; Mouser Part Number 771-PCA9685PW,118
U1102, U1103: TBD62X83A; SOIC-18W_7.5x11.6mm_Pitch1.27mm; Mouser Part Number 757-TBD62083AFG or 757-TBD62783AFG

Connections:
+12V: JP1101.2, JP1104.1, JP1105.2, JP1108.1; also elsewhere on the board
/MCU/SCL: U1101.26 (SCL); also elsewhere on the board
/MCU/SDA: U1101.27 (SDA); also elsewhere on the board
GND: C1101.2, JP1102.2, JP1103.1, JP1106.2, JP1107.1, U1101.2 (A1), U1101.3 (A2), U1101.4 (A3), U1101.5 (A4), U1101.14 (Vss), U1101.23 (OE), U1101.24 (A5), U1101.25 (ExtCLK); also elsewhere on the board
unnamed: JP1101.1, JP1103.2, P1101.9, U1102.10 (OC)
unnamed: JP1102.1, JP1104.2, U1102.9 (IC)
unnamed: JP1105.1, JP1107.2, P1102.9, U1103.10 (OC)
unnamed: JP1106.1, JP1108.2, U1103.9 (IC)
unnamed: P1101.1, RP1101.16 (R1.2)
unnamed: P1101.2, RP1101.15 (R2.2)
unnamed: P1101.3, RP1101.14 (R3.2)
unnamed: P1101.4, RP1101.13 (R4.2)
unnamed: P1101.5, RP1101.12 (R5.2)
unnamed: P1101.6, RP1101.11 (R6.2)
unnamed: P1101.7, RP1101.10 (R7.2)
unnamed: P1101.8, RP1101.9 (R8.2)
unnamed: P1102.1, RP1102.16 (R1.2)
unnamed: P1102.2, RP1102.15 (R2.2)
unnamed: P1102.3, RP1102.14 (R3.2)
unnamed: P1102.4, RP1102.13 (R4.2)
unnamed: P1102.5, RP1102.12 (R5.2)
unnamed: P1102.6, RP1102.11 (R6.2)
unnamed: P1102.7, RP1102.10 (R7.2)
unnamed: P1102.8, RP1102.9 (R8.2)
unnamed: R1101.1, U1101.1 (A0)
unnamed: RP1101.1 (R1.1), U1102.18 (Out)
unnamed: RP1101.2 (R2.1), U1102.17 (Out)
unnamed: RP1101.3 (R3.1), U1102.16 (Out)
unnamed: RP1101.4 (R4.1), U1102.15 (Out)
unnamed: RP1101.5 (R5.1), U1102.14 (Out)
unnamed: RP1101.6 (R6.1), U1102.13 (Out)
unnamed: RP1101.7 (R7.1), U1102.12 (Out)
unnamed: RP1101.8 (R8.1), U1102.11 (Out)
unnamed: RP1102.1 (R1.1), U1103.18 (Out)
unnamed: RP1102.2 (R2.1), U1103.17 (Out)
unnamed: RP1102.3 (R3.1), U1103.16 (Out)
unnamed: RP1102.4 (R4.1), U1103.15 (Out)
unnamed: RP1102.5 (R5.1), U1103.14 (Out)
unnamed: RP1102.6 (R6.1), U1103.13 (Out)
unnamed: RP1102.7 (R7.1), U1103.12 (Out)
unnamed: RP1102.8 (R8.1), U1103.11 (Out)
unnamed: U1101.6 (LED0), U1102.8 (In)
unnamed: U1101.7 (LED1), U1102.7 (In)
unnamed: U1101.8 (LED2), U1102.6 (In)
unnamed: U1101.9 (LED3), U1102.5 (In)
unnamed: U1101.10 (LED4), U1102.4 (In)
unnamed: U1101.11 (LED5), U1102.3 (In)
unnamed: U1101.12 (LED6), U1102.2 (In)
unnamed: U1101.13 (LED7), U1102.1 (In)
unnamed: U1101.15 (LED8), U1103.8 (In)
unnamed: U1101.16 (LED9), U1103.7 (In)
unnamed: U1101.17 (LED10), U1103.6 (In)
unnamed: U1101.18 (LED11), U1103.5 (In)
unnamed: U1101.19 (LED12), U1103.4 (In)
unnamed: U1101.20 (LED13), U1103.3 (In)
unnamed: U1101.21 (LED14), U1103.2 (In)
unnamed: U1101.22 (LED15), U1103.1 (In)

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
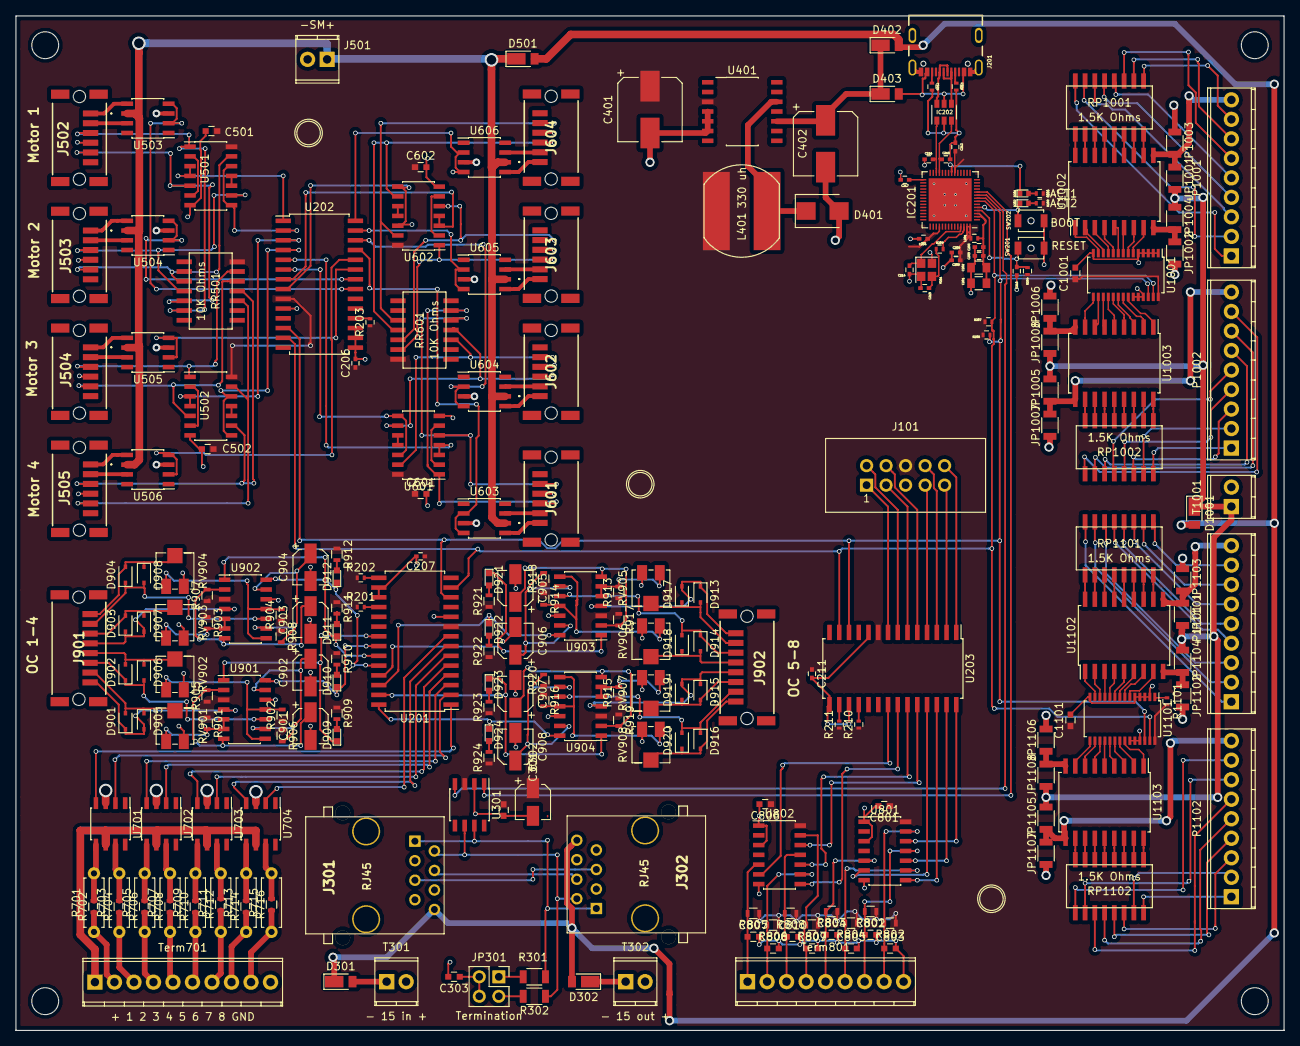
[picture p96: board ESP32-S3-MegaMultiFunction.kicad_pcb from above]

Board: 2 copper layers, 165.1 x 132.1 mm, 245 parts (0 on the bottom side), 300 nets.
