RobertPHeller/ESP32-LCC/ESP32-S3-MultiIO/ESP32-S3-MultiIO.kicad_pcb

## KiCad design ESP32-S3-MultiIO/ESP32-S3-MultiIO.kicad_pcb (2022-10-09)

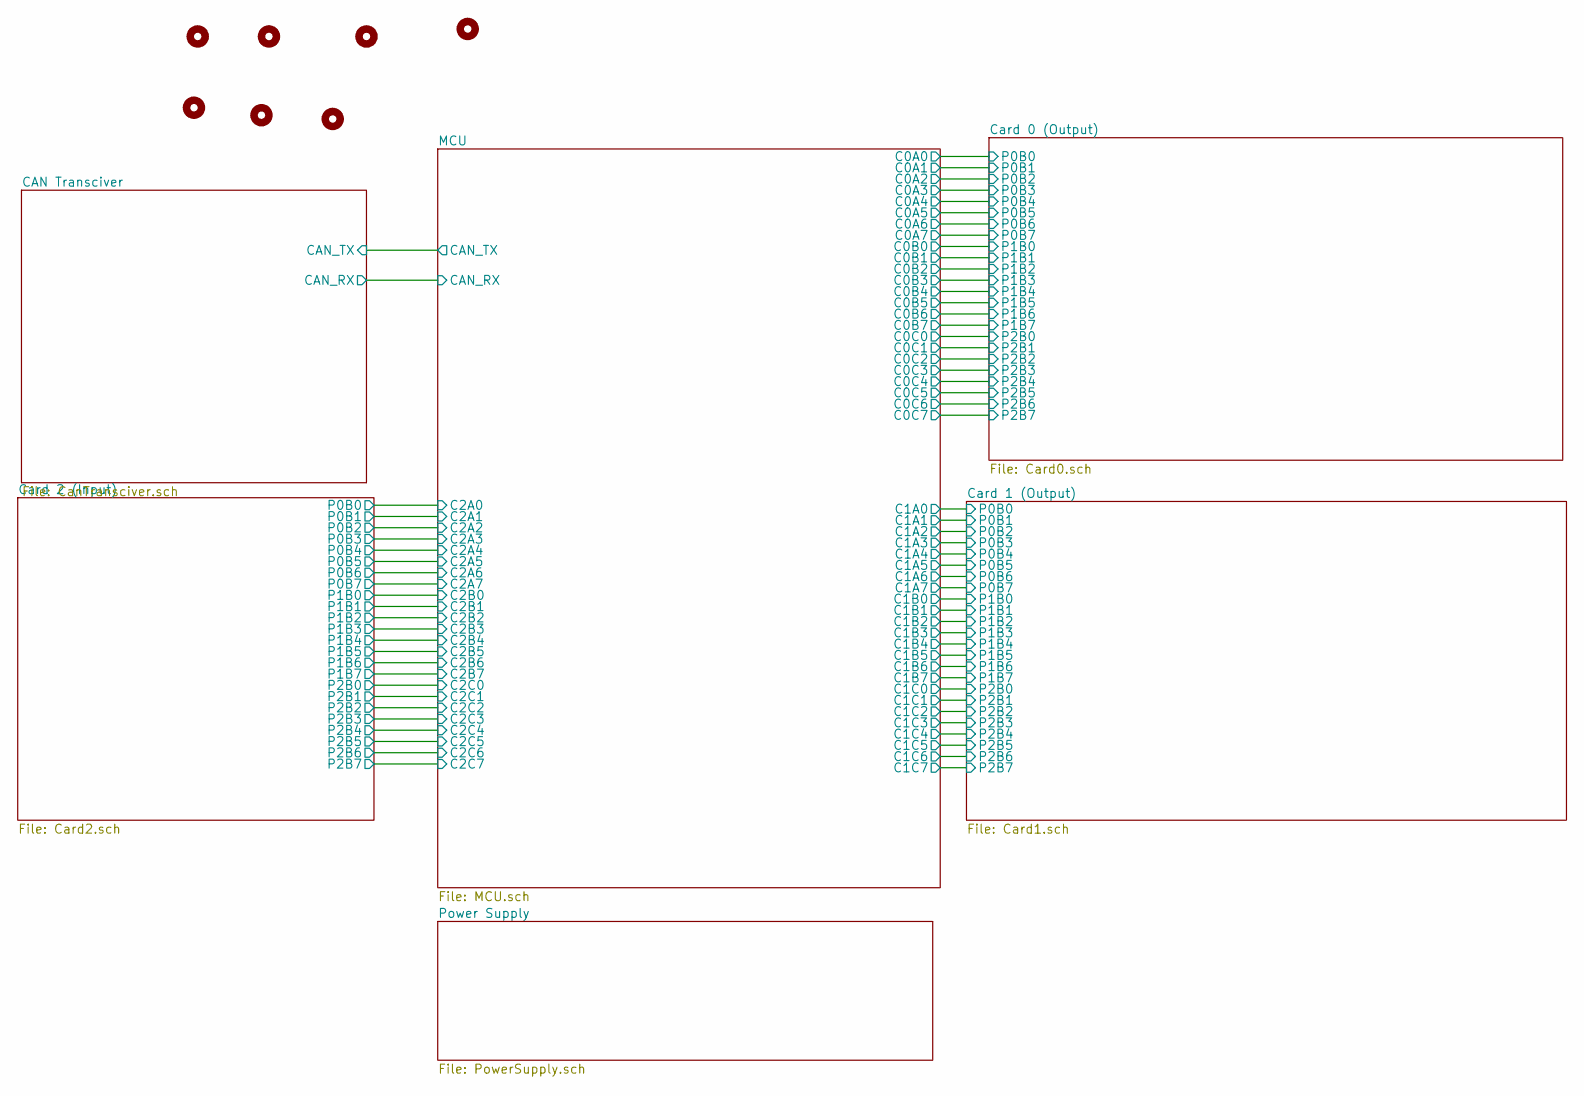
[picture p97: schematic ESP32-S3-MultiIO.sch]

Parts:
FD101, FD102, FD103: Fid Mark; Fiducial_Modern_SilkscreenTop
MK101, MK102, MK103, MK104: Mounting_Hole; MountingHole_3.5mm
