RobertPHeller/ESP32-LCC/ESP32-S3-MultiIO/ESP32-S3-MultiIO.kicad_pcb

## KiCad design ESP32-S3-MultiIO/ESP32-S3-MultiIO.kicad_pcb (continued)

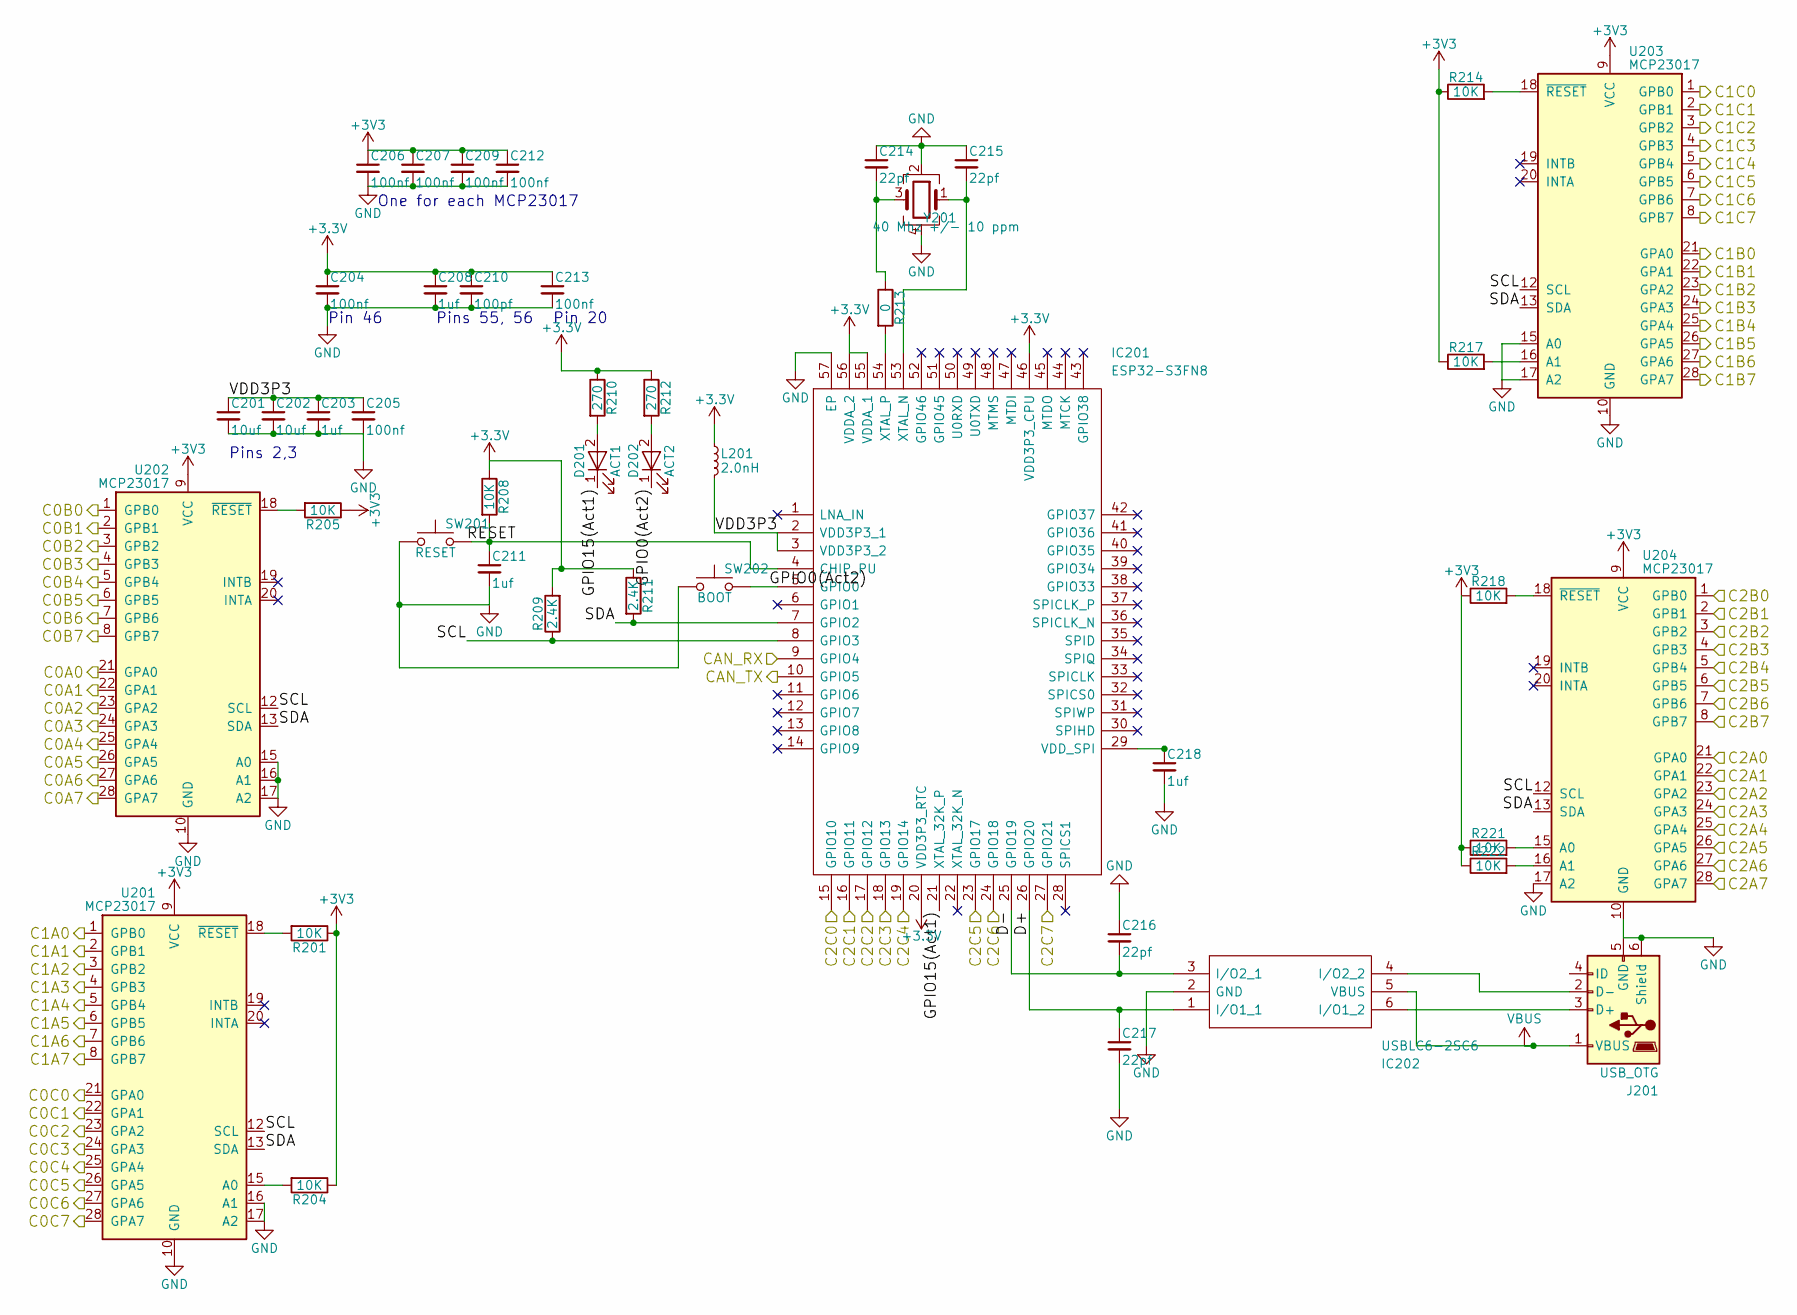
[picture p98: schematic MCU.sch, ESP32 S3 Multifunction Board]

Parts:
C201, C202: 10uf; C_0805; Mouser Part Number 187-CL21A106MQFNNNE
C203, C208, C211, C218: 1uf; C_0402; Mouser Part Number 80-C0402C101K8RAUTO
C204, C205, C206, C207, C209, C212, C213: 100nf; C_0402; Mouser Part Number 710-885012105001
C210: 100pf; C_0402; Mouser Part Number 80-C0402C101K3RAUTO
C214, C215, C216, C217: 22pf; C_0402; Mouser Part Number 187-CL05C220JB5NNND
D201: ACT1; LED_0402; Mouser Part Number 710-150040GS73220
D202: ACT2; LED_0402; Mouser Part Number 710-150040SS73220
IC201: ESP32-S3FN8; QFN-56-1EP_7x7mm_Pitch0.4mm; Manufacturer_Part_Number ESP32-S3FN8; Mouser Part Number 356-ESP32-S3FN8
IC202: USBLC6-2SC6; SOT-23-6; Mouser Part Number 511-USBLC6-2SC6
J201: USB_OTG; USB_Micro-B_Molex_47346-0001; Mouser Part Number 538-47346-0001
L201: 2.0nH; L_0402; Mouser Part Number 810-MLG1005S2N0ST000
R201, R204, R205, R208, R214, R217, R218, R221, R222: 10K; R_0402; Mouser Part Number 603-RC0402JR-1310KL
R209, R211: 2.4K; R_0402; Mouser Part Number 71-CRCW06032K40JNEAC
R210, R212: 270; R_0402; Mouser Part Number 754-RR0510P-271D
R213: 0; R_0402; Mouser Part Number 71-CRCW04020000Z0EDC
SW201: RESET; PTS647SM38SMTR2LFS; Mouser Part Number 611-PTS647SN70SMTR2L
SW202: BOOT; PTS647SM38SMTR2LFS; Mouser Part Number 611-PTS647SN70SMTR2L
U201, U202, U203, U204: MCP23017; SOIC-28W_7.5x17.9mm_Pitch1.27mm
Y201: 40 Mhz +/- 10 ppm; FA20_H; Mouser Part Number 732-FA-20H40MF10Z-W3

Connections:
/CAN Transciver/CAN_RX: IC201.9 (GPIO4); also elsewhere on the board
/CAN Transciver/CAN_TX: IC201.10 (GPIO5); also elsewhere on the board
/MCU/C0A0: U202.21 (GPA0); also elsewhere on the board
/MCU/C0A1: U202.22 (GPA1); also elsewhere on the board
/MCU/C0A2: U202.23 (GPA2); also elsewhere on the board
/MCU/C0A3: U202.24 (GPA3); also elsewhere on the board
/MCU/C0A4: U202.25 (GPA4); also elsewhere on the board
/MCU/C0A5: U202.26 (GPA5); also elsewhere on the board
/MCU/C0A6: U202.27 (GPA6); also elsewhere on the board
/MCU/C0A7: U202.28 (GPA7); also elsewhere on the board
/MCU/C0B0: U202.1 (GPB0); also elsewhere on the board
/MCU/C0B1: U202.2 (GPB1); also elsewhere on the board
/MCU/C0B2: U202.3 (GPB2); also elsewhere on the board
/MCU/C0B3: U202.4 (GPB3); also elsewhere on the board
/MCU/C0B4: U202.5 (GPB4); also elsewhere on the board
/MCU/C0B5: U202.6 (GPB5); also elsewhere on the board
/MCU/C0B6: U202.7 (GPB6); also elsewhere on the board
/MCU/C0B7: U202.8 (GPB7); also elsewhere on the board
/MCU/C0C0: U201.21 (GPA0); also elsewhere on the board
/MCU/C0C1: U201.22 (GPA1); also elsewhere on the board
/MCU/C0C2: U201.23 (GPA2); also elsewhere on the board
/MCU/C0C3: U201.24 (GPA3); also elsewhere on the board
/MCU/C0C4: U201.25 (GPA4); also elsewhere on the board
/MCU/C0C5: U201.26 (GPA5); also elsewhere on the board
/MCU/C0C6: U201.27 (GPA6); also elsewhere on the board
/MCU/C0C7: U201.28 (GPA7); also elsewhere on the board
/MCU/C1A0: U201.1 (GPB0); also elsewhere on the board
/MCU/C1A1: U201.2 (GPB1); also elsewhere on the board
/MCU/C1A2: U201.3 (GPB2); also elsewhere on the board
/MCU/C1A3: U201.4 (GPB3); also elsewhere on the board
/MCU/C1A4: U201.5 (GPB4); also elsewhere on the board
/MCU/C1A5: U201.6 (GPB5); also elsewhere on the board
/MCU/C1A6: U201.7 (GPB6); also elsewhere on the board
/MCU/C1A7: U201.8 (GPB7); also elsewhere on the board
/MCU/C1B0: U203.21 (GPA0); also elsewhere on the board
/MCU/C1B1: U203.22 (GPA1); also elsewhere on the board
/MCU/C1B2: U203.23 (GPA2); also elsewhere on the board
/MCU/C1B3: U203.24 (GPA3); also elsewhere on the board
/MCU/C1B4: U203.25 (GPA4); also elsewhere on the board
/MCU/C1B5: U203.26 (GPA5); also elsewhere on the board
/MCU/C1B6: U203.27 (GPA6); also elsewhere on the board
/MCU/C1B7: U203.28 (GPA7); also elsewhere on the board
/MCU/C1C0: U203.1 (GPB0); also elsewhere on the board
/MCU/C1C1: U203.2 (GPB1); also elsewhere on the board
/MCU/C1C2: U203.3 (GPB2); also elsewhere on the board
/MCU/C1C3: U203.4 (GPB3); also elsewhere on the board
/MCU/C1C4: U203.5 (GPB4); also elsewhere on the board
/MCU/C1C5: U203.6 (GPB5); also elsewhere on the board
/MCU/C1C6: U203.7 (GPB6); also elsewhere on the board
/MCU/C1C7: U203.8 (GPB7); also elsewhere on the board
/MCU/C2A0: U204.21 (GPA0); also elsewhere on the board
/MCU/C2A1: U204.22 (GPA1); also elsewhere on the board
/MCU/C2A2: U204.23 (GPA2); also elsewhere on the board
/MCU/C2A3: U204.24 (GPA3); also elsewhere on the board
/MCU/C2A4: U204.25 (GPA4); also elsewhere on the board
/MCU/C2A5: U204.26 (GPA5); also elsewhere on the board
/MCU/C2A6: U204.27 (GPA6); also elsewhere on the board
/MCU/C2A7: U204.28 (GPA7); also elsewhere on the board
/MCU/C2B0: U204.1 (GPB0); also elsewhere on the board
/MCU/C2B1: U204.2 (GPB1); also elsewhere on the board
/MCU/C2B2: U204.3 (GPB2); also elsewhere on the board
/MCU/C2B3: U204.4 (GPB3); also elsewhere on the board
/MCU/C2B4: U204.5 (GPB4); also elsewhere on the board
/MCU/C2B5: U204.6 (GPB5); also elsewhere on the board
/MCU/C2B6: U204.7 (GPB6); also elsewhere on the board
/MCU/C2B7: U204.8 (GPB7); also elsewhere on the board
/MCU/C2C0: IC201.15 (GPIO10); also elsewhere on the board
/MCU/C2C1: IC201.16 (GPIO11); also elsewhere on the board
/MCU/C2C2: IC201.17 (GPIO12); also elsewhere on the board
/MCU/C2C3: IC201.18 (GPIO13); also elsewhere on the board
/MCU/C2C4: IC201.19 (GPIO14); also elsewhere on the board
/MCU/C2C5: IC201.23 (GPIO17); also elsewhere on the board
/MCU/C2C6: IC201.24 (GPIO18); also elsewhere on the board
/MCU/C2C7: IC201.27 (GPIO21); also elsewhere on the board
/MCU/D+: C217.1, IC201.26 (GPIO20), IC202.1 (I/O1_1)
/MCU/D-: C216.2, IC201.25 (GPIO19), IC202.3 (I/O2_1)
/MCU/GPIO0(Act2): D202.1 (K), IC201.5 (GPIO0), SW202.2
/MCU/GPIO15(Act1): D201.1 (K), IC201.21 (XTAL_32K_P)
/MCU/RESET: C211.1, IC201.4 (CHIP_PU), R208.2, SW201.2
/MCU/SCL: IC201.8 (GPIO3), R209.1, U201.12 (SCL), U202.12 (SCL), U203.12 (SCL), U204.12 (SCL)
/MCU/SDA: IC201.7 (GPIO2), R211.2, U201.13 (SDA), U202.13 (SDA), U203.13 (SDA), U204.13 (SDA)
/MCU/VDD3P3: C201.1, C202.1, C203.1, C205.1, IC201.2 (VDD3P3_1), IC201.3 (VDD3P3_2), L201.2
GND: C201.2, C202.2, C203.2, C204.2, C205.2, C206.2, C207.2, C208.2, C209.2, C210.2, C211.2, C212.2, C213.2, C214.1, C215.1, C216.1, C217.2, C218.2, IC201.57 (EP), IC202.2 (GND), J201.5 (GND), J201.6 (Shield), SW201.1, SW202.1, U201.10 (GND), U201.16 (A1), U201.17 (A2), U202.10 (GND), U202.15 (A0), U202.16 (A1), U202.17 (A2), U203.10 (GND), U203.15 (A0), U203.17 (A2), U204.10 (GND), U204.17 (A2), Y201.2, Y201.4; also elsewhere on the board
unnamed: C214.2, R213.1, Y201.3
unnamed: C215.2, IC201.53 (XTAL_N), Y201.1
unnamed: C218.1, IC201.29 (VDD_SPI)
unnamed: D201.2 (A), R210.2
unnamed: D202.2 (A), R212.2
unnamed: IC201.54 (XTAL_P), R213.2
unnamed: IC202.4 (I/O2_2), J201.2 (D-)
unnamed: IC202.6 (I/O1_2), J201.3 (D+)
unnamed: R201.2, U201.18 (~RESET)
unnamed: R204.2, U201.15 (A0)
unnamed: R205.2, U202.18 (~RESET)
unnamed: R214.2, U203.18 (~RESET)
unnamed: R217.2, U203.16 (A1)
unnamed: R218.2, U204.18 (~RESET)
unnamed: R221.2, U204.15 (A0)
unnamed: R222.2, U204.16 (A1)
VBUS: IC202.5 (VBUS), J201.1 (VBUS)

Notes on the sheet:
Pins 2,3
Pin 46
Pins 55, 56
Pin 20
One for each MCP23017


Parts:
C301: .1 uf; C_0603; Mouser Part Number 710-885012206095
C302: 15 uf 15V; CP_Elec_4x5.7; Mouser Part Number 647-UUD1C150MCL
C303: 47 nf; C_0603; Mouser Part Number 710-885012206093
D301, D302: DFLS240-7; D_PowerDI-123; Mouser Part Number 621-DFLS240-7
J301, J302: RJ45; RJ45_8N-S; Mouser Part Number 710-615008144221
JP301: Termination; Pin_Header_Straight_2x02_Pitch2.54mm; Mouser Part Number 649-67997-404HLF
R301, R302: 60 Ohms; R_1206; Mouser Part Number 71-CRCW120660R0KNAIF
T301: - 15 in +; TerminalBlock_Pheonix_MPT-2.54mm_2pol; Mouser Part Number 651-1725656
T302: - 15 out +; TerminalBlock_Pheonix_MPT-2.54mm_2pol; Mouser Part Number 651-1725656
U301: TCAN332DR; SOIC-8_3.9x4.9mm_Pitch1.27mm; Mouser Part Number 595-TCAN332DR

Connections:
/CAN Transciver/CANH: J301.1, J302.1, R301.1, U301.7 (CANH)
/CAN Transciver/CANL: J301.2, J302.2, R302.1, U301.6 (CANL)
/CAN Transciver/CAN_RX: U301.4 (R); also elsewhere on the board
/CAN Transciver/CAN_TX: U301.1 (D); also elsewhere on the board
CAN +12V: D301.1 (K), D302.2 (A), J301.8, J302.8; also elsewhere on the board
GND: C301.2, C302.2, C303.2, J301.3, J301.6, J301.7, J302.3, J302.6, J302.7, T301.2, T302.2, U301.2 (GND); also elsewhere on the board
unnamed: C303.1, JP301.3, JP301.4
unnamed: D301.2 (A), T301.1
unnamed: D302.1 (K), T302.1
unnamed: J301.4, J302.4
unnamed: J301.5, J302.5
unnamed: JP301.1, R301.2
unnamed: JP301.2, R302.2

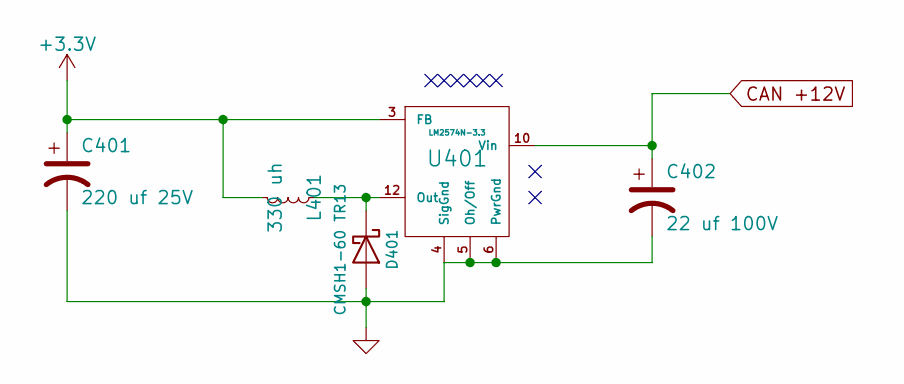
[picture p99: schematic PowerSupply.sch, ESP32 S3 Multifunction Board]

Parts:
C401: 220 uf 25V; CP_Elec_8x10; Mouser Part Number 647-UWT1E221MNL1GS
C402: 22 uf 100V; CP_Elec_8x10; Mouser Part Number 647-UUX2A220MNL6GS
D401: CMSH1-60 TR13; D_SMB; Mouser Part Number 610-CMSH1-60TR13
L401: 330 uh; SRN1060; Mouser Part Number 652-SRN1060-331M
U401: LM2574N-3.3; SOIC-14_7.4x8.7mm_Pitch1.27mm; Mouser Part Number 926-LM2574MX33NOPB

Connections:
CAN +12V: C402.1, U401.10 (Vin); also elsewhere on the board
GND: C401.2, C402.2, D401.2 (A), U401.4 (SigGnd), U401.5 (Oh/Off), U401.6 (PwrGnd); also elsewhere on the board
unnamed: D401.1 (K), L401.1, U401.12 (Out)

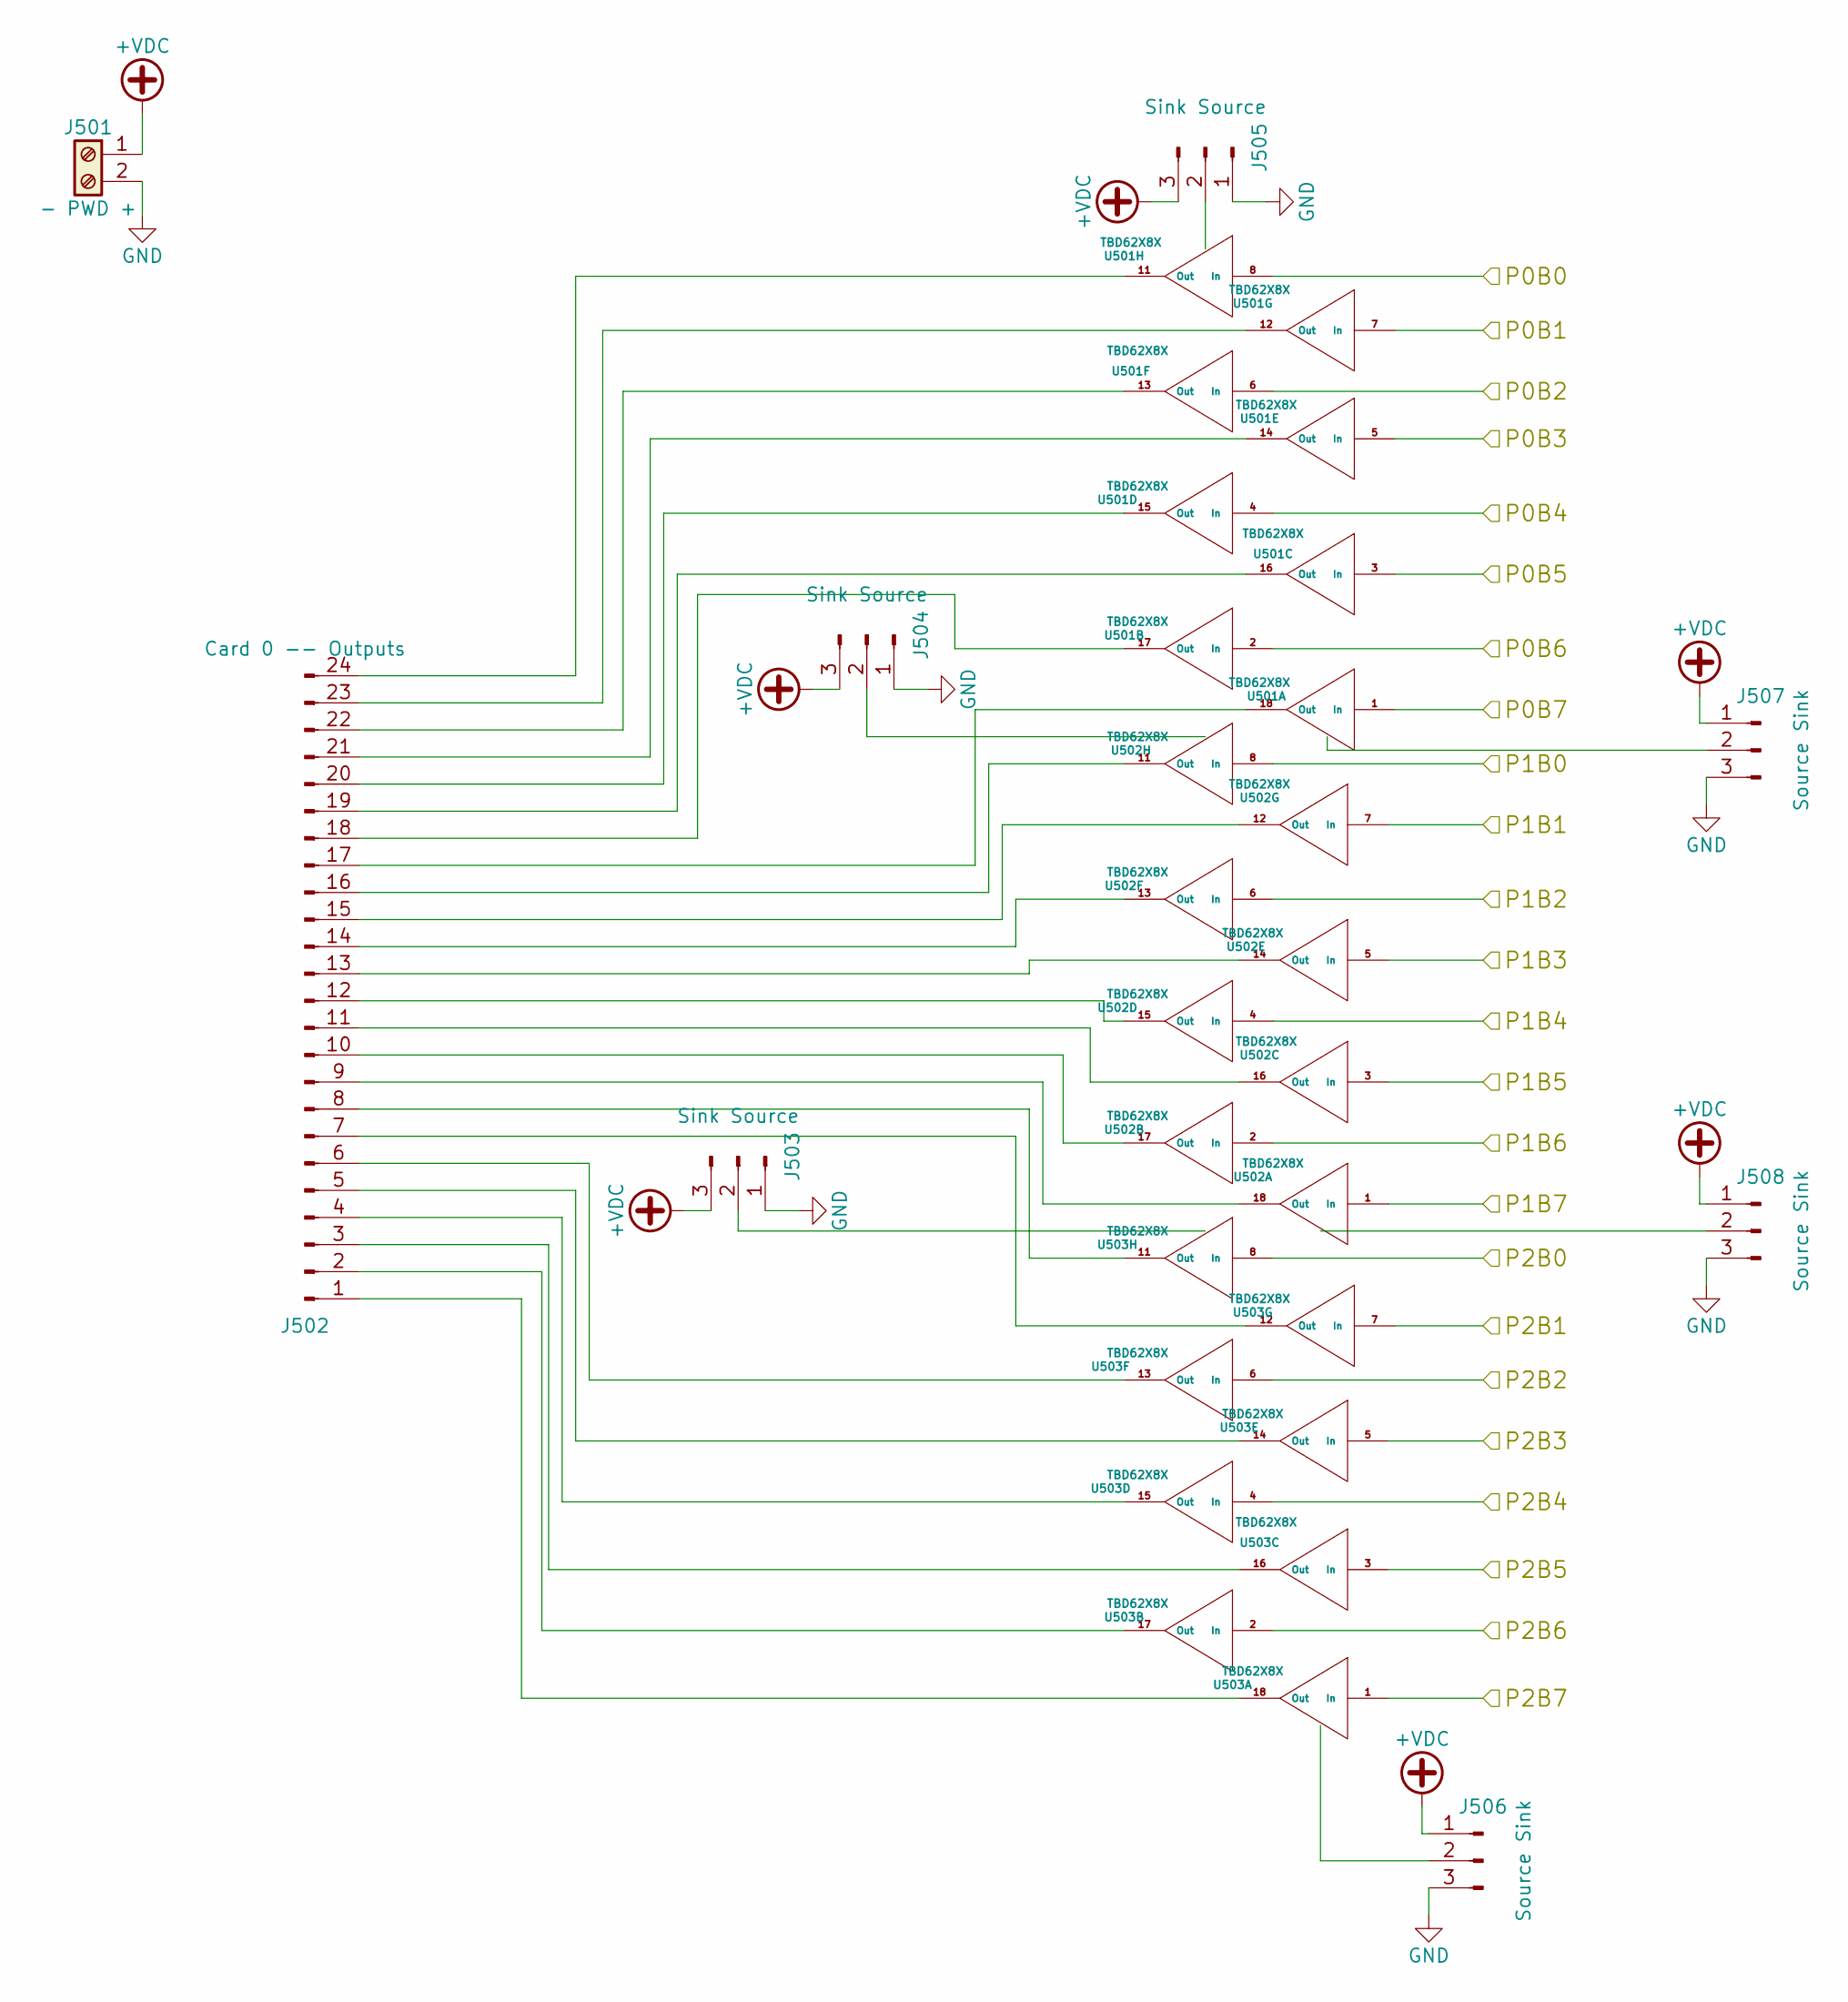
[picture p100: schematic Card0.sch]

Parts:
J501: - PWD +; TerminalBlock_Pheonix_MPT-2.54mm_2pol
J502: Card 0 -- Outputs; Molex_KK_396_01x24_3.96mm_RightAngle; Mouser Part Number 538-26-48-1242
J503, J504, J505: Sink Source; Pin_Header_Straight_1x03_Pitch2.54mm
J506, J507, J508: Source Sink; Pin_Header_Straight_1x03_Pitch2.54mm
U501, U502, U503: TBD62X8X; DIP-18_W7.62mm; Mouser Part Number 571-1-2199298-5

Connections:
+VDC: J501.1, J503.3, J504.3, J505.3, J506.1, J507.1, J508.1; also elsewhere on the board
/MCU/C0A0: U501.8 (In); also elsewhere on the board
/MCU/C0A1: U501.7 (In); also elsewhere on the board
/MCU/C0A2: U501.6 (In); also elsewhere on the board
/MCU/C0A3: U501.5 (In); also elsewhere on the board
/MCU/C0A4: U501.4 (In); also elsewhere on the board
/MCU/C0A5: U501.3 (In); also elsewhere on the board
/MCU/C0A6: U501.2 (In); also elsewhere on the board
/MCU/C0A7: U501.1 (In); also elsewhere on the board
/MCU/C0B0: U502.8 (In); also elsewhere on the board
/MCU/C0B1: U502.7 (In); also elsewhere on the board
/MCU/C0B2: U502.6 (In); also elsewhere on the board
/MCU/C0B3: U502.5 (In); also elsewhere on the board
/MCU/C0B4: U502.4 (In); also elsewhere on the board
/MCU/C0B5: U502.3 (In); also elsewhere on the board
/MCU/C0B6: U502.2 (In); also elsewhere on the board
/MCU/C0B7: U502.1 (In); also elsewhere on the board
/MCU/C0C0: U503.8 (In); also elsewhere on the board
/MCU/C0C1: U503.7 (In); also elsewhere on the board
/MCU/C0C2: U503.6 (In); also elsewhere on the board
/MCU/C0C3: U503.5 (In); also elsewhere on the board
/MCU/C0C4: U503.4 (In); also elsewhere on the board
/MCU/C0C5: U503.3 (In); also elsewhere on the board
/MCU/C0C6: U503.2 (In); also elsewhere on the board
/MCU/C0C7: U503.1 (In); also elsewhere on the board
GND: J501.2, J503.1, J504.1, J505.1, J506.3, J507.3, J508.3; also elsewhere on the board
unnamed: J502.1, U503.18 (Out)
unnamed: J502.2, U503.17 (Out)
unnamed: J502.3, U503.16 (Out)
unnamed: J502.4, U503.15 (Out)
unnamed: J502.5, U503.14 (Out)
unnamed: J502.6, U503.13 (Out)
unnamed: J502.7, U503.12 (Out)
unnamed: J502.8, U503.11 (Out)
unnamed: J502.9, U502.18 (Out)
unnamed: J502.10, U502.17 (Out)
unnamed: J502.11, U502.16 (Out)
unnamed: J502.12, U502.15 (Out)
unnamed: J502.13, U502.14 (Out)
unnamed: J502.14, U502.13 (Out)
unnamed: J502.15, U502.12 (Out)
unnamed: J502.16, U502.11 (Out)
unnamed: J502.17, U501.18 (Out)
unnamed: J502.18, U501.17 (Out)
unnamed: J502.19, U501.16 (Out)
unnamed: J502.20, U501.15 (Out)
unnamed: J502.21, U501.14 (Out)
unnamed: J502.22, U501.13 (Out)
unnamed: J502.23, U501.12 (Out)
unnamed: J502.24, U501.11 (Out)
unnamed: J503.2, U503.10 (OC)
unnamed: J504.2, U502.10 (OC)
unnamed: J505.2, U501.10 (OC)
unnamed: J506.2, U503.9 (IC)
unnamed: J507.2, U501.9 (IC)
unnamed: J508.2, U502.9 (IC)

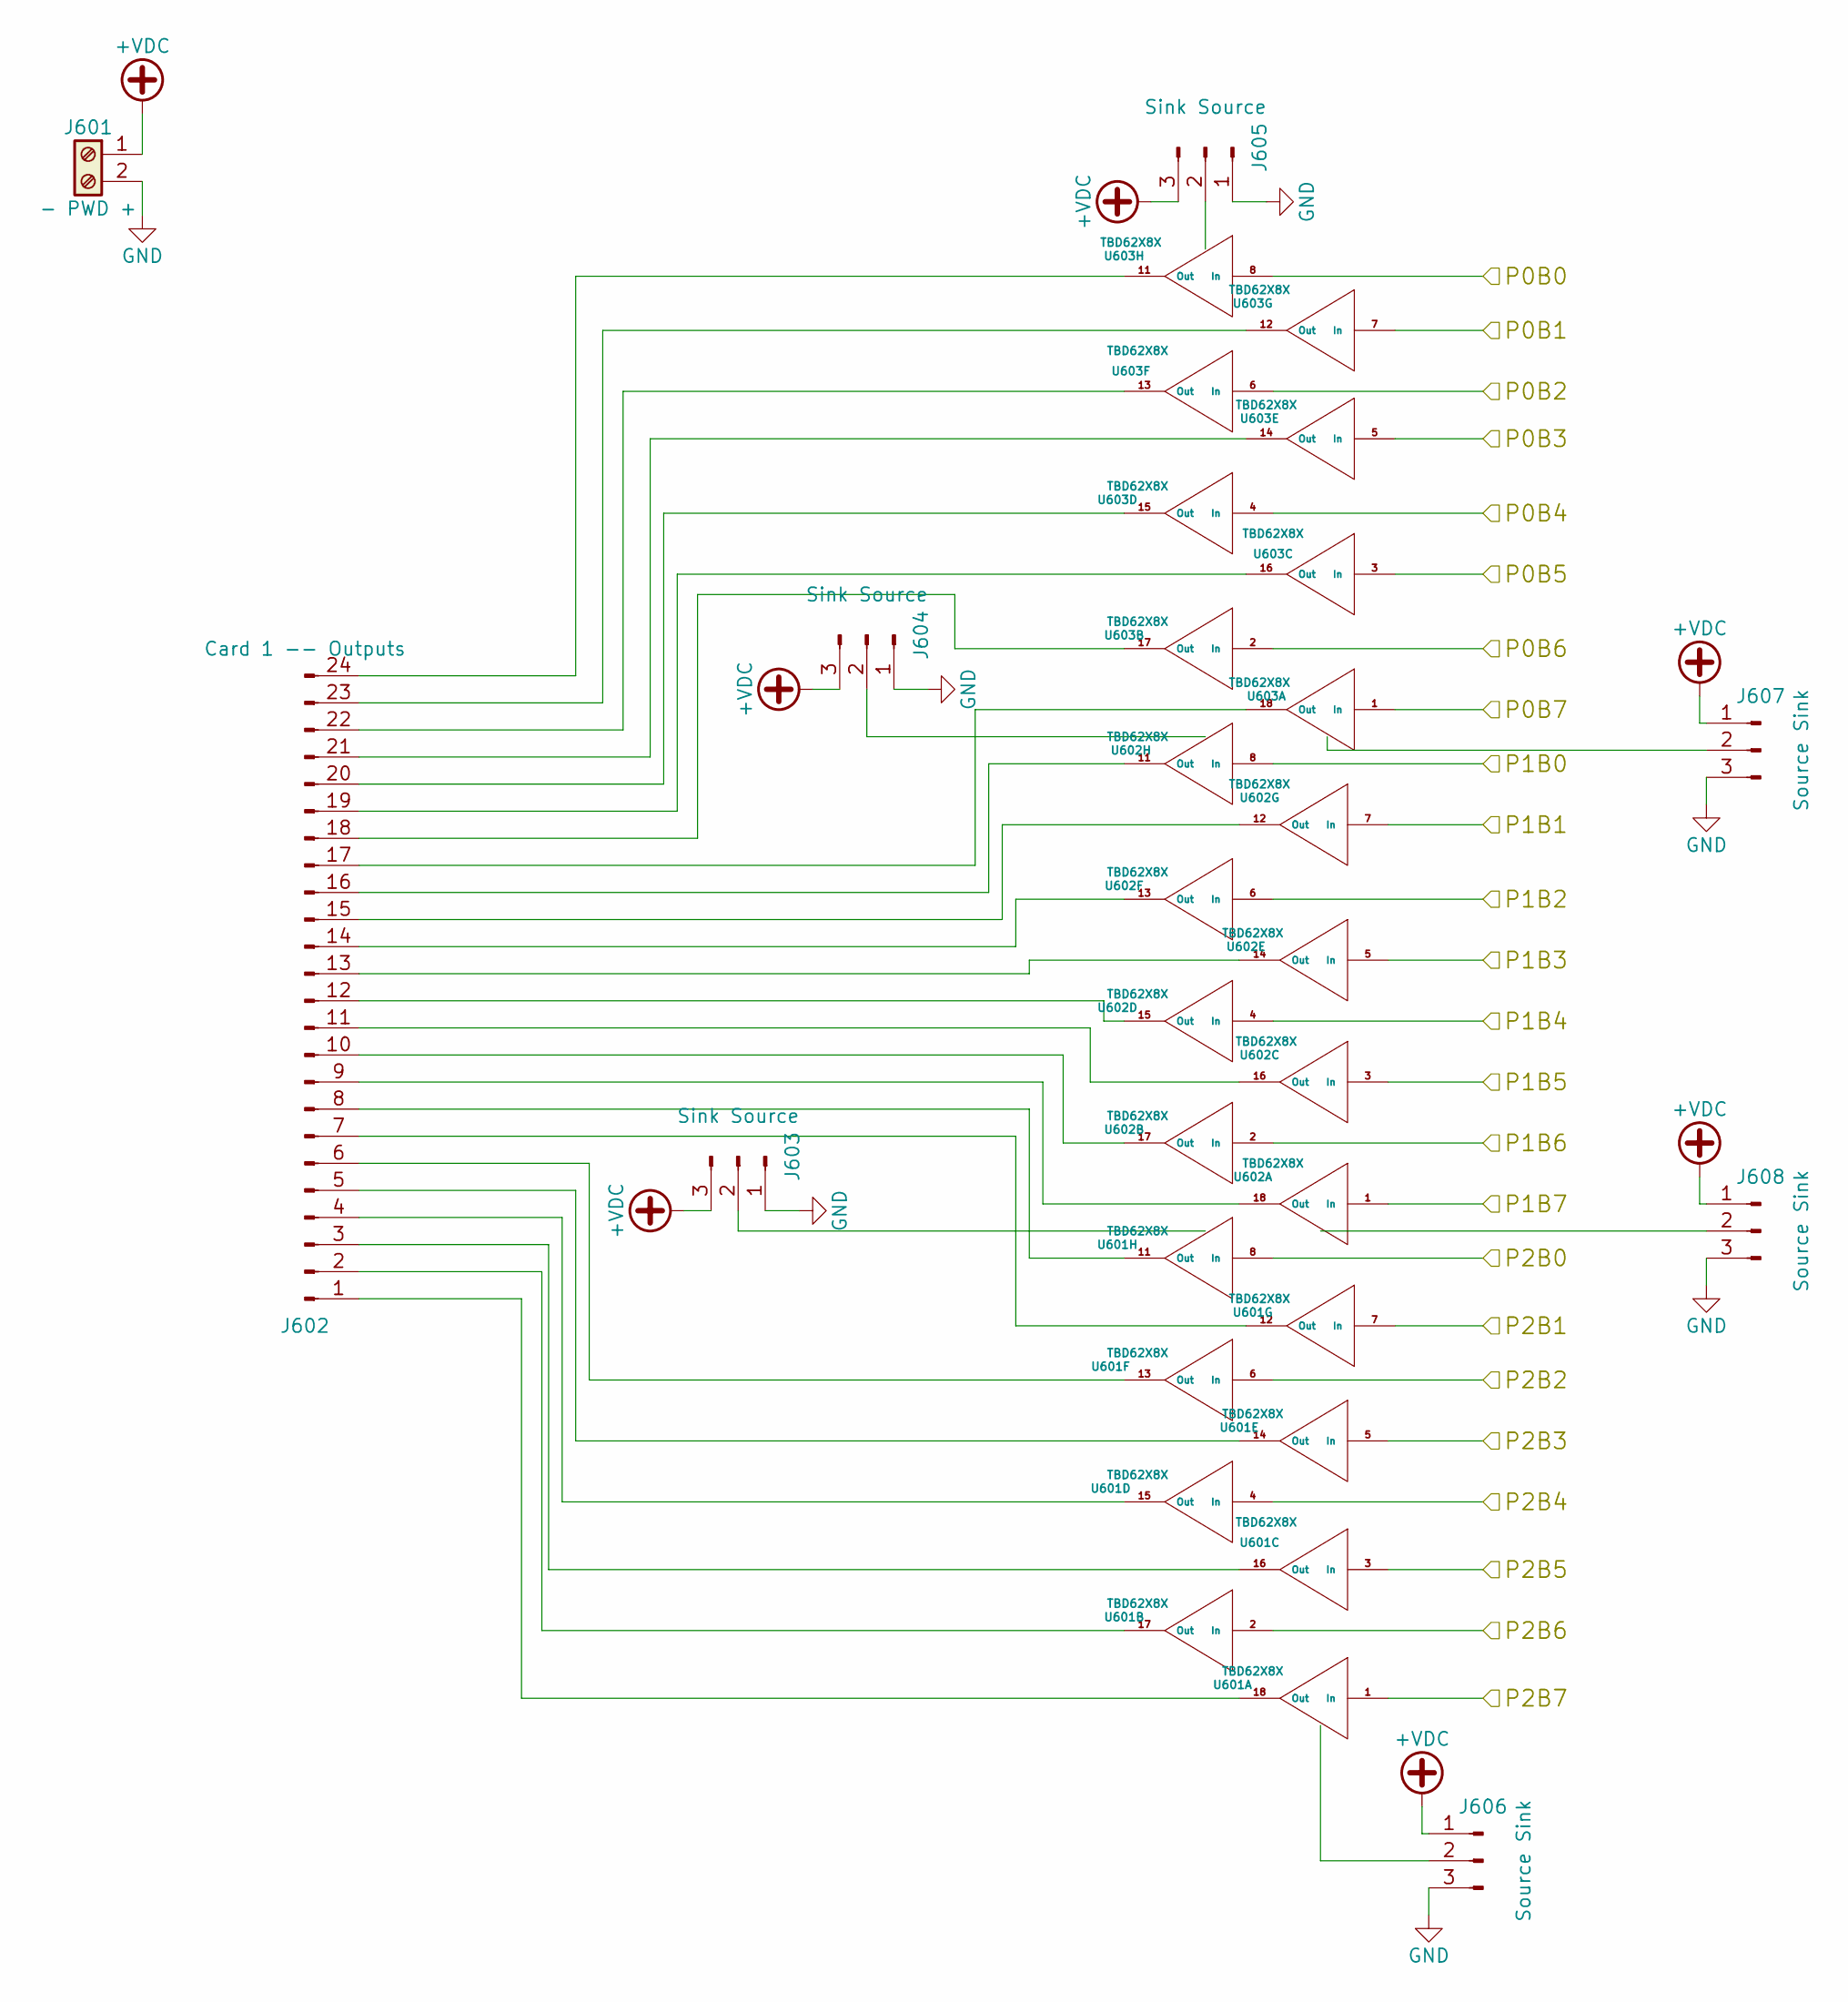
[picture p101: schematic Card1.sch]

Parts:
J601: - PWD +; TerminalBlock_Pheonix_MPT-2.54mm_2pol
J602: Card 1 -- Outputs; Molex_KK_396_01x24_3.96mm_RightAngle; Mouser Part Number 538-26-48-1242
J603, J604, J605: Sink Source; Pin_Header_Straight_1x03_Pitch2.54mm
J606, J607, J608: Source Sink; Pin_Header_Straight_1x03_Pitch2.54mm
U601, U602, U603: TBD62X8X; DIP-18_W7.62mm; Mouser Part Number 571-1-2199298-5

Connections:
+VDC: J601.1, J603.3, J604.3, J605.3, J606.1, J607.1, J608.1; also elsewhere on the board
/MCU/C1A0: U603.8 (In); also elsewhere on the board
/MCU/C1A1: U603.7 (In); also elsewhere on the board
/MCU/C1A2: U603.6 (In); also elsewhere on the board
/MCU/C1A3: U603.5 (In); also elsewhere on the board
/MCU/C1A4: U603.4 (In); also elsewhere on the board
/MCU/C1A5: U603.3 (In); also elsewhere on the board
/MCU/C1A6: U603.2 (In); also elsewhere on the board
/MCU/C1A7: U603.1 (In); also elsewhere on the board
/MCU/C1B0: U602.8 (In); also elsewhere on the board
/MCU/C1B1: U602.7 (In); also elsewhere on the board
/MCU/C1B2: U602.6 (In); also elsewhere on the board
/MCU/C1B3: U602.5 (In); also elsewhere on the board
/MCU/C1B4: U602.4 (In); also elsewhere on the board
/MCU/C1B5: U602.3 (In); also elsewhere on the board
/MCU/C1B6: U602.2 (In); also elsewhere on the board
/MCU/C1B7: U602.1 (In); also elsewhere on the board
/MCU/C1C0: U601.8 (In); also elsewhere on the board
/MCU/C1C1: U601.7 (In); also elsewhere on the board
/MCU/C1C2: U601.6 (In); also elsewhere on the board
/MCU/C1C3: U601.5 (In); also elsewhere on the board
/MCU/C1C4: U601.4 (In); also elsewhere on the board
/MCU/C1C5: U601.3 (In); also elsewhere on the board
/MCU/C1C6: U601.2 (In); also elsewhere on the board
/MCU/C1C7: U601.1 (In); also elsewhere on the board
GND: J601.2, J603.1, J604.1, J605.1, J606.3, J607.3, J608.3; also elsewhere on the board
unnamed: J602.1, U601.18 (Out)
unnamed: J602.2, U601.17 (Out)
unnamed: J602.3, U601.16 (Out)
unnamed: J602.4, U601.15 (Out)
unnamed: J602.5, U601.14 (Out)
unnamed: J602.6, U601.13 (Out)
unnamed: J602.7, U601.12 (Out)
unnamed: J602.8, U601.11 (Out)
unnamed: J602.9, U602.18 (Out)
unnamed: J602.10, U602.17 (Out)
unnamed: J602.11, U602.16 (Out)
unnamed: J602.12, U602.15 (Out)
unnamed: J602.13, U602.14 (Out)
unnamed: J602.14, U602.13 (Out)
unnamed: J602.15, U602.12 (Out)
unnamed: J602.16, U602.11 (Out)
unnamed: J602.17, U603.18 (Out)
unnamed: J602.18, U603.17 (Out)
unnamed: J602.19, U603.16 (Out)
unnamed: J602.20, U603.15 (Out)
unnamed: J602.21, U603.14 (Out)
unnamed: J602.22, U603.13 (Out)
unnamed: J602.23, U603.12 (Out)
unnamed: J602.24, U603.11 (Out)
unnamed: J603.2, U601.10 (OC)
unnamed: J604.2, U602.10 (OC)
unnamed: J605.2, U603.10 (OC)
unnamed: J606.2, U601.9 (IC)
unnamed: J607.2, U603.9 (IC)
unnamed: J608.2, U602.9 (IC)
