RobertPHeller/ESP32-LCC/ESP32-S3-MultiIO/ESP32-S3-MultiIO.kicad_pcb

## KiCad design ESP32-S3-MultiIO/ESP32-S3-MultiIO.kicad_pcb (continued)

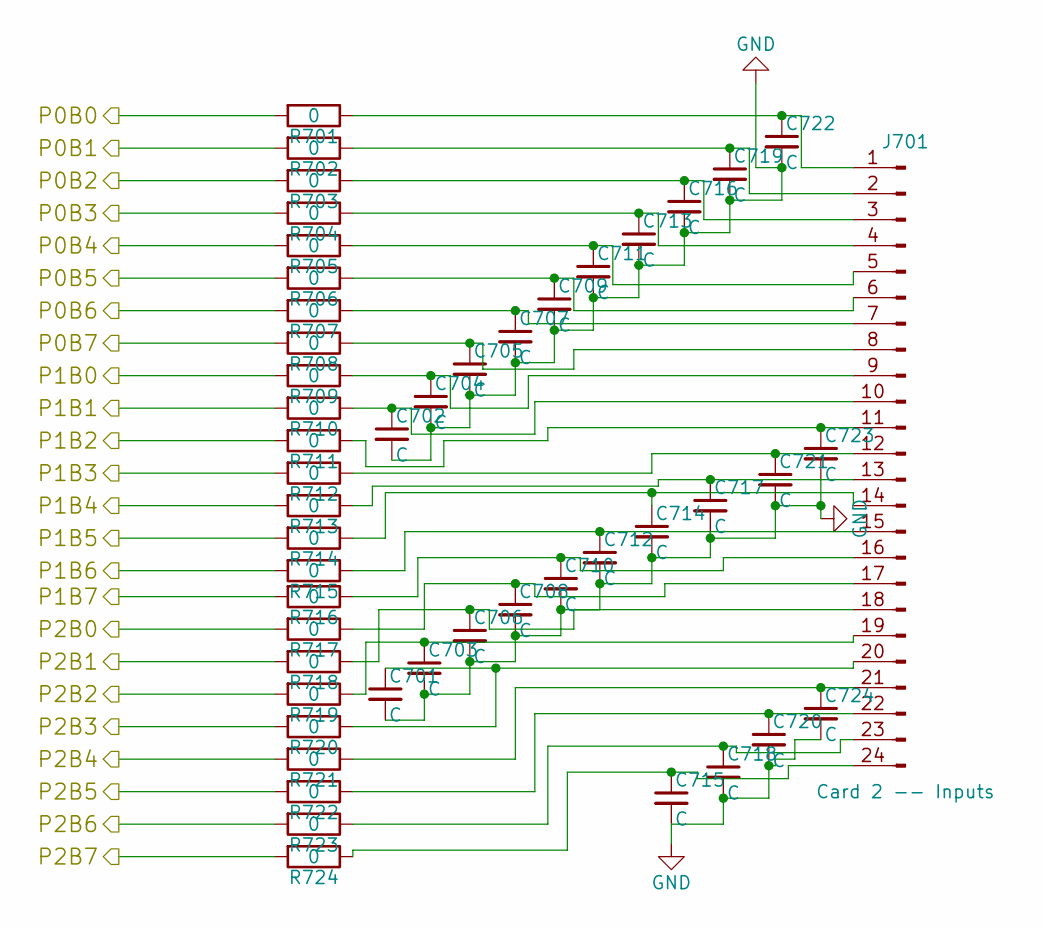
[picture p102: schematic Card2.sch]

Parts:
C701, C702, C703, C704, C705, C706, C707, C708, C709, C710, C711, C712, C713, C714, C715, C716, C717, C718, C719, C720, C721, C722, C723, C724: C; C_Disc_D3.8mm_W2.6mm_P2.50mm
J701: Card 2 -- Inputs; Molex_KK_396_01x24_3.96mm_RightAngle; Mouser Part Number 538-26-48-1242
R701, R702, R703, R704, R705, R706, R707, R708, R709, R710, R711, R712, R713, R714, R715, R716, R717, R718, R719, R720, R721, R722, R723, R724: 0; R_Axial_DIN0207_L6.3mm_D2.5mm_P10.16mm_Horizontal_WJumper

Connections:
/MCU/C2A0: R701.2; also elsewhere on the board
/MCU/C2A1: R702.2; also elsewhere on the board
/MCU/C2A2: R703.2; also elsewhere on the board
/MCU/C2A3: R704.2; also elsewhere on the board
/MCU/C2A4: R705.2; also elsewhere on the board
/MCU/C2A5: R706.2; also elsewhere on the board
/MCU/C2A6: R707.2; also elsewhere on the board
/MCU/C2A7: R708.2; also elsewhere on the board
/MCU/C2B0: R709.2; also elsewhere on the board
/MCU/C2B1: R710.2; also elsewhere on the board
/MCU/C2B2: R711.2; also elsewhere on the board
/MCU/C2B3: R712.2; also elsewhere on the board
/MCU/C2B4: R713.2; also elsewhere on the board
/MCU/C2B5: R714.2; also elsewhere on the board
/MCU/C2B6: R715.2; also elsewhere on the board
/MCU/C2B7: R716.2; also elsewhere on the board
/MCU/C2C0: R717.2; also elsewhere on the board
/MCU/C2C1: R718.2; also elsewhere on the board
/MCU/C2C2: R719.2; also elsewhere on the board
/MCU/C2C3: R720.2; also elsewhere on the board
/MCU/C2C4: R721.2; also elsewhere on the board
/MCU/C2C5: R722.2; also elsewhere on the board
/MCU/C2C6: R723.2; also elsewhere on the board
/MCU/C2C7: R724.2; also elsewhere on the board
GND: C701.2, C702.2, C703.2, C704.2, C705.2, C706.2, C707.2, C708.2, C709.2, C710.2, C711.2, C712.2, C713.2, C714.2, C715.2, C716.2, C717.2, C718.2, C719.2, C720.2, C721.2, C722.2, C723.2, C724.2; also elsewhere on the board
unnamed: C701.1, J701.20, R720.1
unnamed: C702.1, J701.10, R710.1
unnamed: C703.1, J701.19, R719.1
unnamed: C704.1, J701.9, R709.1
unnamed: C705.1, J701.8, R708.1
unnamed: C706.1, J701.18, R718.1
unnamed: C707.1, J701.7, R707.1
unnamed: C708.1, J701.17, R717.1
unnamed: C709.1, J701.6, R706.1
unnamed: C710.1, J701.16, R716.1
unnamed: C711.1, J701.5, R705.1
unnamed: C712.1, J701.15, R715.1
unnamed: C713.1, J701.4, R704.1
unnamed: C714.1, J701.14, R714.1
unnamed: C715.1, J701.24, R724.1
unnamed: C716.1, J701.3, R703.1
unnamed: C717.1, J701.13, R713.1
unnamed: C718.1, J701.23, R723.1
unnamed: C719.1, J701.2, R702.1
unnamed: C720.1, J701.22, R722.1
unnamed: C721.1, J701.12, R712.1
unnamed: C722.1, J701.1, R701.1
unnamed: C723.1, J701.11, R711.1
unnamed: C724.1, J701.21, R721.1

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
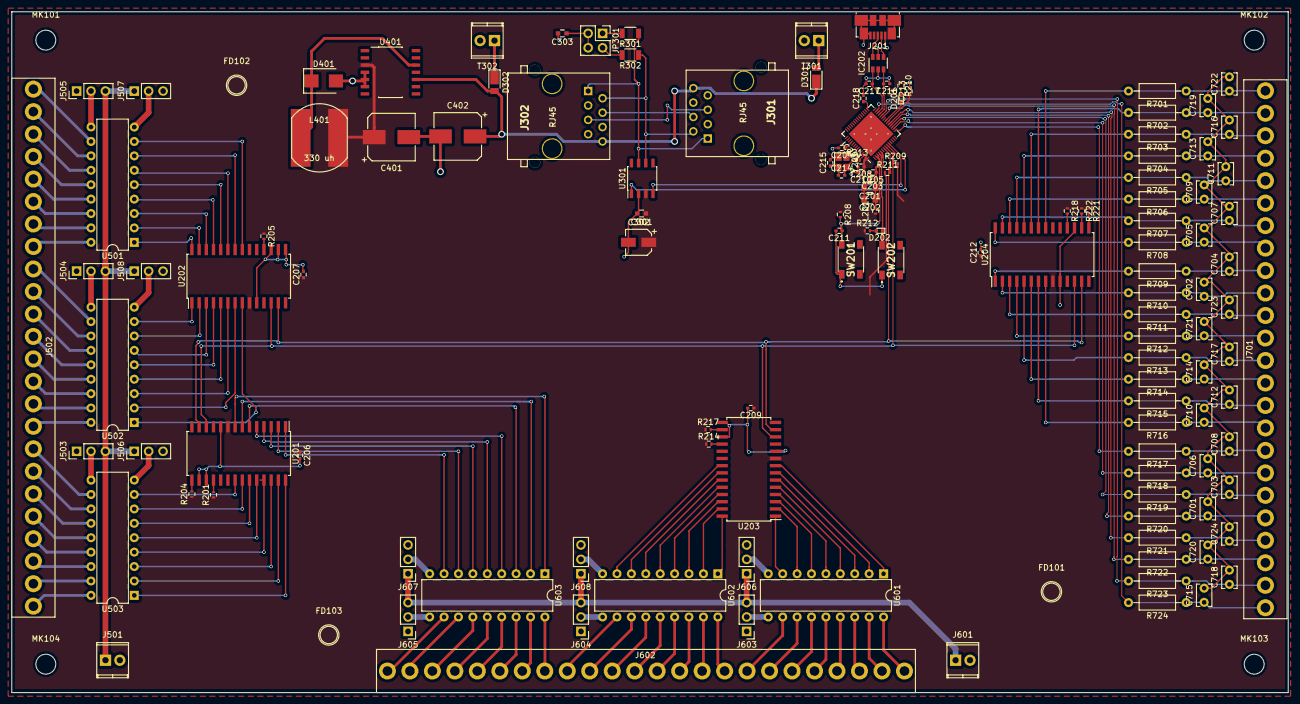
[picture p103: board ESP32-S3-MultiIO.kicad_pcb from above]

Board: 2 copper layers, 225.0 x 120.0 mm, 141 parts (0 on the bottom side), 197 nets.
