RobertPHeller/ESP32-LCC/AtlasLightBoardWiFiLCCTraction/AtlasLightBoardWiFiLCCTraction.kicad_pcb

## KiCad design AtlasLightBoardWiFiLCCTraction/AtlasLightBoardWiFiLCCTraction.kicad_pcb (2026-08-16)

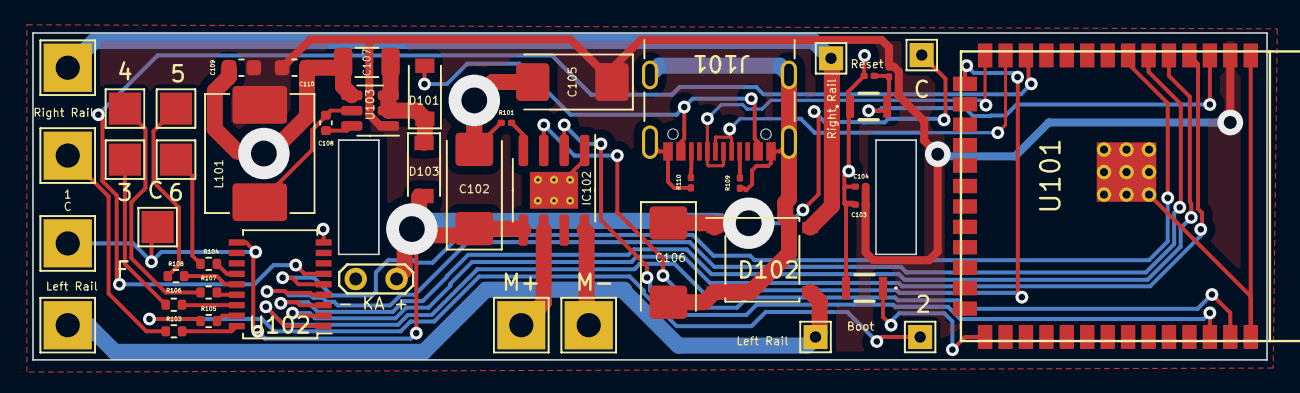
[picture p104: board AtlasLightBoardWiFiLCCTraction.kicad_pcb from above]

Board: 2 copper layers, 76.7 x 20.3 mm, 47 parts (0 on the bottom side), 38 nets.

Parts:
C101, C103, C104: 1uf; C_0201_0603Metric
C102, C105: 10uf 25V; CP_EIA-6032-28_Kemet-C
C106: 100Uf 16V; CP_EIA-6032-28_Kemet-C
C107: 10uf 25V; C_1206_3216Metric
C108: 100nf; C_0402_1005Metric
C109, C110: 22uf 6.3V; C_0603_1608Metric
D101, D103: SBR545SAFQ-13; D_SOD-123
D102: ABS15M; Diode_Bridge_Diotec_ABS
IC102: MP6614GN-Z; SOIC-8-1EP_3.9x4.9mm_P1.27mm_EP2.29x3mm_ThermalVias
J101: USB_C_Receptacle; USB_C_Receptacle_GCT_USB4105-xx-A_16P_TopMnt_Horizontal
L101: 3.9uH; L_Abracon_ASPI-0630LR
R101: 20K; R_0201_0603Metric
R102, R109, R110: 5.1K; R_0201_0603Metric
R103, R104, R105, R106, R107, R108: 1K; R_0402_1005Metric
SW101: Reset; NanoT160AS
SW102: Boot; NanoT160AS
TP101: M-; TestPoint_THTPad_3.0x3.0mm_Drill1.5mm
TP102: M+; TestPoint_THTPad_3.0x3.0mm_Drill1.5mm
TP103: C; TestPoint_THTPad_3.0x3.0mm_Drill1.5mm
TP104: - KA +; TestPoint_2Pads_Pitch2.54mm_Drill0.8mm
TP107: C; TestPoint_Pad_2.0x2.0mm
TP110: 1; TestPoint_THTPad_3.0x3.0mm_Drill1.5mm
TP111: 6; TestPoint_Pad_2.0x2.0mm
TP112: C; TestPoint_THTPad_1.5x1.5mm_Drill0.7mm
TP113: 2; TestPoint_THTPad_1.5x1.5mm_Drill0.7mm
TP114: 3; TestPoint_Pad_2.0x2.0mm
TP115: 4; TestPoint_Pad_2.0x2.0mm
TP116: 5; TestPoint_Pad_2.0x2.0mm
TP119: Right Rail; TestPoint_THTPad_3.0x3.0mm_Drill1.5mm
TP120: Left Rail; TestPoint_THTPad_3.0x3.0mm_Drill1.5mm
TP121: Right Rail; TestPoint_THTPad_1.5x1.5mm_Drill0.7mm
TP122: Left Rail; TestPoint_THTPad_1.5x1.5mm_Drill0.7mm
U101: ESP32_S3_WROOM; ESP32_S3_WROOM-1
U102: TBD62083A; SSOP-18_4.4x6.5mm_P0.65mm
U103: AP63203WU; TSOT-23-6

Connections:
+3V3: C103.1, C104.1, C105.1, C109.1, C110.1, L101.2, R102.1, U101.2 (3v3), U103.1 (FB)
/Boot0: SW102.1, U101.27 (IO0)
/D+: J101.A6 (D+), J101.B6 (D+), U101.14 (IO20)
/D-: J101.A7 (D-), J101.B7 (D-), U101.13 (IO19)
/Function1: U101.15 (IO3), U102.1 (In)
/Function2: U101.4 (IO4), U102.2 (In)
/Function3: U101.5 (IO5), U102.3 (In)
/Function4: U101.6 (IO6), U102.4 (In)
/Function5: U101.7 (IO7), U102.5 (In)
/Function6: U101.12 (IO8), U102.6 (In)
/MForward: IC102.3 (IN1), U101.39 (IO1)
/MPower: C102.1, C106.1, D102.1 (+), D103.2 (A), IC102.5 (VIN), TP103.1, TP104.2, TP107.1, TP112.1, U102.10 (OC)
/MReverse: IC102.2 (IN2), U101.38 (IO2)
/Reset: C101.1, R102.2, SW101.2, U101.3 (EN)
/VBus: D101.2 (A), J101.A4 (VBUS), J101.A9 (VBUS), J101.B4 (VBUS), J101.B9 (VBUS)
/Vin: C107.1, D101.1 (K), D103.1 (K), U103.2 (EN), U103.3 (IN)
GND: C101.2, C102.2, C103.2, C104.2, C105.2, C106.2, C107.2, C109.2, C110.2, D102.2 (-), IC102.1 (GND), IC102.9 (EP), J101.A1 (GND), J101.A12 (GND), J101.B1 (GND), J101.B12 (GND), J101.S1 (SHIELD), R101.2, R109.2, R110.2, SW101.1, SW102.2, TP104.1, U101.1 (GND), U101.40 (GND), U101.EPad (GND), U102.9 (IC), U103.4 (GND)
unnamed: C108.1, L101.1, U103.5 (SW)
unnamed: C108.2, U103.6 (BST)
unnamed: D102.3, TP120.1, TP122.1
unnamed: D102.4, TP119.1, TP121.1
unnamed: IC102.4 (ISET), R101.1
unnamed: IC102.6 (OUT1), TP102.1
unnamed: IC102.8 (OUT2), TP101.1
unnamed: J101.A5 (CC1), R109.1
unnamed: J101.B5 (CC2), R110.1
unnamed: R103.1, TP110.1
unnamed: R103.2, U102.18 (Out)
unnamed: R104.1, TP111.1
unnamed: R104.2, U102.13 (Out)
unnamed: R105.1, TP113.1
unnamed: R105.2, U102.17 (Out)
unnamed: R106.1, TP114.1
unnamed: R106.2, U102.16 (Out)
unnamed: R107.1, TP115.1
unnamed: R107.2, U102.15 (Out)
unnamed: R108.1, TP116.1
unnamed: R108.2, U102.14 (Out)
