RobertPHeller/ESP32-LCC/ESP32-PWMHalfSidingSMD/ESP32-PWMHalfSidingSMD_CA.kicad_pcb

## KiCad design ESP32-PWMHalfSidingSMD/ESP32-PWMHalfSidingSMD_CA.kicad_pcb (2023-06-04)

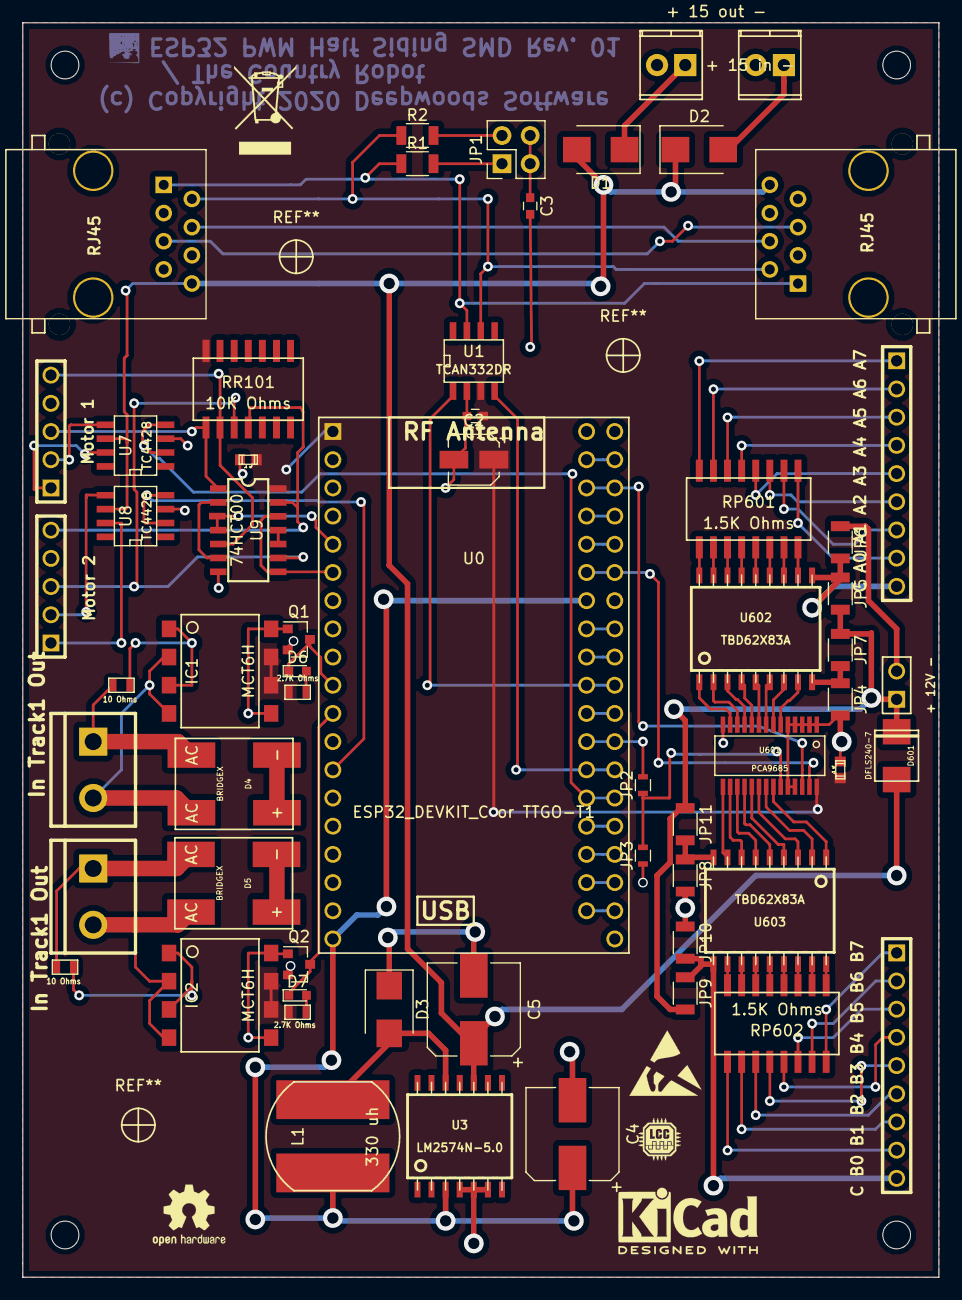
[picture p105: board ESP32-PWMHalfSidingSMD_CA.kicad_pcb from above]

Board: 2 copper layers, 82.5 x 113.0 mm, 64 parts (0 on the bottom side), 101 nets.

Parts:
C1: .1 uf; C_0603
C2: 15 uf 15V; CP_Elec_4x5.7
C3: 47 nf; C_0603
C4: 220 uf 25V; CP_Elec_8x10
C5: 22 uf 100V; CP_Elec_8x10
C7, C601: .1 uf; c_0603
D1, D2: DFLS240-7; D_SMB
D3: CMSH1-60 TR13; D_SMB
D4, D5: BRIDGEX; Z4DGP
D6, D7: LED; LED_0603
D601: DFLS240-7; SMB
IC1, IC2: MCT6H; SMT8
J1, J2: RJ45; RJ45_8N-S
JP1: Termination; Pin_Header_Straight_2x02_Pitch2.54mm
JP2, JP3: 0; R_0603
JP4, JP5, JP6, JP7, JP8, JP9, JP10, JP11: 0; R_1206
L1: 330 uh; SRN1060
MH: MountingHole_2-5mm_RevA_Date21Jun2010
MH#2, MH#3, MH#4: MountingHole_2-5mm_RevA_Date21Jun2010
P601: C A0 A1 A2 A3 A4 A5 A6 A7; ScrewTerm_2.54-9
P602: C B0 B1 B2 B3 B4 B5 B6 B7; ScrewTerm_2.54-9
Q1, Q2: MMBT3904; SOT-23
R1, R2: 60 Ohms; R_1206
R3, R5: 10 Ohms; SM0603
R4, R6: 2.7K Ohms; SM0603
RP601, RP602: 1.5K Ohms; 4816P
RR101: 10K Ohms; 4814P
T1: + 15 in -; TerminalBlock_Pheonix_MPT-2.54mm_2pol
T2: + 15 out -; TerminalBlock_Pheonix_MPT-2.54mm_2pol
T3, T6: In Track1 Out; bornier2
T4: Motor 1; ScrewTerm_2.54-5
T5: Motor 2; ScrewTerm_2.54-5
T601: + 12V -; ScrewTerm2.54-2
U0: ESP32_DEVKIT_C or TTGO-T1; ESP32-Combo
U1: TCAN332DR; SOIC-8_N
U3: LM2574N-5.0; soic-14
U7, U8: TC4428; SOIC-8_N
U9: 74HCT00; SOIC-14_Narrow
U601: PCA9685; tssop-28
U602, U603: TBD62X83A; soic-18

Connections:
3V3: C1.1, C2.1, C7.1, C601.1, IC1.6, IC1.7, IC2.6, IC2.7, R4.1, R6.1, RR101.14, U0.1, U1.3, U9.14, U601.28
+5V: C4.1, L1.1, U0.19, U3.3
+12V: D601.2, JP5.2, JP7.1, JP9.2, JP11.1, T601.1
/CAN Transceiver/CANH: J1.1, J2.1, R1.1, U1.7
/CAN Transceiver/CANL: J1.2, J2.2, R2.1, U1.6
/CAN_RX: U0.26, U1.4
/CAN_TX: U0.29, U1.1
/Motor1A: T4.1, U7.7
/Motor1B: T4.2, U7.5
/Motor2A: T5.1, U8.7
/Motor2B: T5.2, U8.5
/Motor 1: U0.25, U7.2, U7.4
/Motor 2: U0.13, U8.2, U8.4
/OD1: D6.1, Q1.3, U0.10
/OD2: D7.1, Q2.3, U0.11
/OE: JP2.2, U0.27
/SCL: U0.36, U601.26
/SDA: U0.33, U601.27
/Sense1A: RR101.1, T4.3, U9.1
/Sense1B: RR101.2, T4.5, U9.5
/Sense2A: RR101.3, T5.3, U9.9
/Sense2B: RR101.4, T5.5, U9.13
/Sense 1: U0.5, U9.3, U9.4
/Sense 2: U0.6, U9.8, U9.12
CAN +12V: C5.1, D1.2, D2.1, D601.1, J1.8, J2.8, U3.10, U7.6, U8.6
GND: C1.2, C2.2, C3.2, C4.2, C5.2, C7.2, C601.2, D3.1, J1.3, J1.6, J1.7, J2.3, J2.6, J2.7, JP3.1, JP4.2, JP6.1, JP8.2, JP10.1, Q1.2, Q2.2, T1.2, T2.2, T4.4, T5.4, T601.2, U0.14, U0.38, U1.2, U3.4, U3.5, U3.6, U7.3, U8.3, U9.7, U601.1, U601.2, U601.3, U601.4, U601.5, U601.14, U601.24, U601.25
unnamed: C3.1, JP1.3, JP1.4
unnamed: D1.1, T1.1
unnamed: D2.2, T2.1
unnamed: D3.2, L1.2, U3.12
unnamed: D4.1, D4.4
unnamed: D4.2, IC1.2, IC1.4, T3.2
unnamed: D4.3, R3.1, T3.1
unnamed: D5.1, D5.4
unnamed: D5.2, IC2.2, IC2.4, T6.2
unnamed: D5.3, R5.1, T6.1
unnamed: D6.2, R4.2
unnamed: D7.2, R6.2
unnamed: IC1.1, IC1.3, R3.2
unnamed: IC1.5, IC1.8, Q1.1
unnamed: IC2.1, IC2.3, R5.2
unnamed: IC2.5, IC2.8, Q2.1
unnamed: J1.4, J2.4
unnamed: J1.5, J2.5
unnamed: JP1.1, R1.2
unnamed: JP1.2, R2.2
unnamed: JP2.1, JP3.2, U601.23
unnamed: JP4.1, JP7.2, U602.9
unnamed: JP5.1, JP6.2, P601.9, U602.10
unnamed: JP9.1, JP10.2, P602.9, U603.10
unnamed: JP8.1, JP11.2, U603.9
unnamed: P601.1, RP601.16
unnamed: P601.2, RP601.15
unnamed: P601.3, RP601.14
unnamed: P601.4, RP601.13
unnamed: P601.5, RP601.12
unnamed: P601.6, RP601.11
unnamed: P601.7, RP601.10
unnamed: P601.8, RP601.9
unnamed: P602.1, RP602.16
unnamed: P602.2, RP602.15
unnamed: P602.3, RP602.14
unnamed: P602.4, RP602.13
unnamed: P602.5, RP602.12
unnamed: P602.6, RP602.11
unnamed: P602.7, RP602.10
unnamed: P602.8, RP602.9
unnamed: RP601.1, U602.18
unnamed: RP601.2, U602.17
unnamed: RP601.3, U602.16
unnamed: RP601.4, U602.15
unnamed: RP601.5, U602.14
unnamed: RP601.6, U602.13
unnamed: RP601.7, U602.12
unnamed: RP601.8, U602.11
unnamed: RP602.1, U603.18
unnamed: RP602.2, U603.17
unnamed: RP602.3, U603.16
unnamed: RP602.4, U603.15
unnamed: RP602.5, U603.14
unnamed: RP602.6, U603.13
unnamed: RP602.7, U603.12
unnamed: RP602.8, U603.11
unnamed: U9.2, U9.6
unnamed: U9.10, U9.11
unnamed: U601.6, U602.8
unnamed: U601.7, U602.7
unnamed: U601.8, U602.6
unnamed: U601.9, U602.5
unnamed: U601.10, U602.4
unnamed: U601.11, U602.3
unnamed: U601.12, U602.2
unnamed: U601.13, U602.1
unnamed: U601.15, U603.8
unnamed: U601.16, U603.7
unnamed: U601.17, U603.6
unnamed: U601.18, U603.5
unnamed: U601.19, U603.4
unnamed: U601.20, U603.3
unnamed: U601.21, U603.2
unnamed: U601.22, U603.1
