RobertPHeller/ESP32-LCC/ESP32-OctalBufferOpenMRNIDF/main/idf_component.yml

dependencies:
  NVSManager:
    path: ../../CommonComponents/NVSManager
  FS:
    path: ../../CommonComponents/FS
  HealthMonitor:
    path: ../../CommonComponents/HealthMonitor
  RebootHelpers:
    path: ../../CommonComponents/RebootHelpers
  WiFiManager:
    path: ../../CommonComponents/WiFiManager
  espressif/mdns: '*'
