RobertPHeller/ESP32-LCC/ESP32-S3-MultiFunctionOpenMRNIDF/main/idf_component.yml

dependencies:
  PCA9685PWM:
    path: ../../CommonComponents/PCA9685PWM
  NVSManager:
    path: ../../CommonComponents/NVSManager
  FS:
    path: ../../CommonComponents/FS
  HealthMonitor:
    path: ../../CommonComponents/HealthMonitor
  RebootHelpers:
    path: ../../CommonComponents/RebootHelpers
  GeneralIO:
    path: ../../CommonComponents/GeneralIO
  Signals:
    path: ../../CommonComponents/Signals
  Logic:
    path: ../../CommonComponents/Logic
  WiFiManager:
    path: ../../CommonComponents/WiFiManager          
  espressif/mdns: '*'
