RobertPHeller/ESP32-LCC/ESP32-T7S3-ArduinoBase/firmware/main/idf_component.yml

dependencies:
  OpenMRNIDF:
    version: idf-v5
    git: https://github.com/atanisoft/OpenMRNIDF.git
  NVSManager:
    path: ../../../CommonComponents/NVSManager
  FS:
    path: ../../../CommonComponents/FS
  HealthMonitor:
    path: ../../../CommonComponents/HealthMonitor
  RebootHelpers:
    path: ../../../CommonComponents/RebootHelpers
  Azatrax:
    path: ../../../CommonComponents/Azatrax  
