RobertPHeller/ESP32-LCC/CommonComponents/NVSManager/NvsManager.cpp

// -!- C++ -!- //////////////////////////////////////////////////////////////
//
//  System        : 
//  Module        : 
//  Object Name   : $RCSfile$
//  Revision      : $Revision$
//  Date          : $Date$
//  Author        : $Author$
//  Created By    : Robert Heller
//  Created       : Sat Dec 17 14:03:56 2022
//  Last Modified : <260327.2057>
//
//  Description	
//
//  Notes
//
//  History
//	
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
static const char rcsid[] = "@(#) : $Id$";

#include "sdkconfig.h"
#include <esp_err.h>
#include <esp_partition.h>
#include <nvs.h>
#include <nvs_flash.h>
#include <utils/Singleton.hxx>
#include "NvsManager.hxx"
#include "NodeIdMemoryConfigSpace.hxx"
#include "WiFiMemoryConfigSpace.hxx"
#include <esp_wifi_types.h>
#include <freertos_drivers/esp32/Esp32WiFiManager.hxx>
#include <utils/logging.h>
#include <openlcb/SimpleStack.hxx>

#ifndef CONFIG_WIFI_STATION_SSID
#define CONFIG_WIFI_STATION_SSID ""
#endif

#ifndef CONFIG_WIFI_STATION_PASSWORD
#define CONFIG_WIFI_STATION_PASSWORD ""
#endif

#ifndef CONFIG_WIFI_HOSTNAME_PREFIX
#define CONFIG_WIFI_HOSTNAME_PREFIX "esp32multifunc_"
#endif

#ifndef CONFIG_WIFI_MODE
#define CONFIG_WIFI_MODE 0
#endif

namespace nvsmanager
{

static uninitialized<NodeIdMemoryConfigSpace> node_id_memoryspace;
static uninitialized<WiFiMemoryConfigSpace> wifi_memory_space;

void NvsManager::init(uint8_t reset_reason)
{
    LOG(VERBOSE, "NVS.init(%d)", reset_reason);
    
    nvs_handle_t nvs;
    size_t config_size = sizeof(config_);
    
    // Initialize NVS before we do any other initialization as it may be
    // internally used by various components even if we disable it's usage in
    // the WiFi connection stack.
    LOG(INFO, "[NVS] Initializing NVS");
    if (ESP_ERROR_CHECK_WITHOUT_ABORT(nvs_flash_init()) == ESP_ERR_NVS_NO_FREE_PAGES)
    {
        const esp_partition_t *partition =
              esp_partition_find_first(ESP_PARTITION_TYPE_DATA,
                                       ESP_PARTITION_SUBTYPE_DATA_NVS, NULL);
        if (partition != NULL)
        {
            LOG(INFO, "[NVS] Erasing partition %s...", partition->label);
            ESP_ERROR_CHECK(esp_partition_erase_range(partition, 0, partition->size));
            ESP_ERROR_CHECK(nvs_flash_init());
        }
    }
    LOG(INFO, "[NVS] Loading configuration");
    // load non-CDI based config from NVS
    ESP_ERROR_CHECK(nvs_open(NVS_NAMESPACE, NVS_READWRITE, &nvs));
    esp_err_t res = ESP_ERROR_CHECK_WITHOUT_ABORT(
                 nvs_get_blob(nvs, NVS_CFG_KEY, &config_, &config_size));
    need_persist_ = false;
    if (config_size != sizeof(config_) || res != ESP_OK)
    {
        LOG_ERROR("[NVS] Configuration missing or corrupt, using defaults");
        memset(&config_, 0, sizeof(config_));
        config_.node_id = CONFIG_OLCB_NODE_ID;
        config_.force_reset = false;
        config_.reset_events_req = false;
        config_.bootloader_req = false;
//#ifdef CONFIG_ESP32_WIFI_ENABLED
        config_.wifi_mode = (wifi_mode_t)CONFIG_WIFI_MODE;
        const char *s = CONFIG_WIFI_HOSTNAME_PREFIX;
        char *d = config_.hostname_prefix;
        int i;
        for (i = 0; i <= sizeof(config_.hostname_prefix) && *s != '\0';i++)
            *d++ = *s++;
        config_.hostname_prefix[sizeof(config_.hostname_prefix)-1] = 0;
        s = CONFIG_WIFI_STATION_SSID;
        d = config_.station_ssid;
        for (i = 0; i <= sizeof(config_.station_ssid) && *s != '\0';i++)
            *d++ = *s++;
        config_.station_ssid[sizeof(config_.station_ssid)-1] = 0;
        s = CONFIG_WIFI_STATION_PASSWORD;
        d = config_.station_pass;
        for (i = 0; i <= sizeof(config_.station_ssid) && *s != '\0';i++)
            *d++ = *s++;
        config_.station_pass[sizeof(config_.station_pass)-1] = 0;
//#endif
        need_persist_ = true;
    }
    CheckPersist();
    DisplayNvsConfiguration();
}

void NvsManager::register_virtual_memory_spaces(openlcb::SimpleStackBase *stack)
{
    LOG(VERBOSE, "NVS.register_virtual_memory_spaces()");
    node_id_memoryspace.emplace(stack, this);
//#ifdef CONFIG_ESP32_WIFI_ENABLED
    wifi_memory_space.emplace(stack, this);
//#endif
}

void NvsManager::DisplayNvsConfiguration()
{
    static constexpr const char *const WIFI_MODES[] =
    {
        "Disabled",
        "Station"
    };
    // display current configuration settings.
    LOG(INFO, "[NVS] Node ID: 0x%llX", config_.node_id);
    LOG(INFO, "[NVS] Force Reset: %s",
        config_.force_reset ? "true" : "false");
    LOG(INFO, "[NVS] Reset events: %s",
        config_.reset_events_req ? "true" : "false");
    LOG(INFO, "[NVS] Bootloader: %s",
        config_.bootloader_req ? "true" : "false");
//#ifdef CONFIG_ESP32_WIFI_ENABLED
    uint8_t m = (uint8_t)config_.wifi_mode;
    if (m > 1)
    {
        config_.wifi_mode = (wifi_mode_t) 1;
        persist_configuration();
    }
    LOG(INFO, "[NVS] WiFi Mode: %s (%d)", WIFI_MODES[config_.wifi_mode],
        config_.wifi_mode);
    LOG(INFO, "[NVS] Hostname Prefix: %s", config_.hostname_prefix);
    if (config_.wifi_mode != 0)
    {
        LOG(INFO, "[NVS] Station SSID: %s", config_.station_ssid);
    }
    
//#endif
}


DEFINE_SINGLETON_INSTANCE(NvsManager);

/// NVS Persistence namespace.
const char NvsManager::NVS_NAMESPACE[];

/// NVS Persistence key.
const char NvsManager::NVS_CFG_KEY[];


}
