RobertPHeller/ESP32-LCC/ESP32-S3-QuadNeoPixelOpenMRNIDF/components/NeoPixel/Esp32NeoPixel.cpp

// -!- C++ -!- //////////////////////////////////////////////////////////////
//
//  System        : 
//  Module        : 
//  Object Name   : $RCSfile$
//  Revision      : $Revision$
//  Date          : $Date$
//  Author        : $Author$
//  Created By    : Robert Heller
//  Created       : Fri Mar 10 11:36:16 2023
//  Last Modified : <230311.1217>
//
//  Description	
//
//  Notes
//
//  History
//	
/////////////////////////////////////////////////////////////////////////////
//
//    Copyright (C) 2023  Robert Heller D/B/A Deepwoods Software
//			51 Locke Hill Road
//			Wendell, MA 01379-9728
//
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
// 
//
//////////////////////////////////////////////////////////////////////////////

static const char rcsid[] = "@(#) : $Id$";

#include <stdint.h>
#include <string.h>
#include <esp_timer.h>
#include "Esp32NeoPixel.hxx"
#include "driver/rmt.h"

#include <esp_err.h>
#include <driver/gpio.h>
#include <esp_idf_version.h>

#define HIGH 0x1
#define LOW  0x0

#define INPUT 0x0
#define OUTPUT 0x1

static inline void pinMode(uint8_t pin, uint8_t mode)
{
    switch (mode) {
    case OUTPUT:
        {
            gpio_config_t cfg;
            memset(&cfg, 0, sizeof(gpio_config_t));
            cfg.pin_bit_mask = BIT64(pin);
            cfg.mode = GPIO_MODE_OUTPUT;
            ESP_ERROR_CHECK(gpio_config(&cfg));
            break;
        }
    case INPUT:
        {
            gpio_config_t cfg;
            memset(&cfg, 0, sizeof(gpio_config_t));
            cfg.pin_bit_mask = BIT64(pin);
            cfg.mode = GPIO_MODE_INPUT;
            ESP_ERROR_CHECK(gpio_config(&cfg));
            break;
        }
    }
}

static inline void digitalWrite(uint8_t pin, uint8_t val)
{
    ESP_ERROR_CHECK(gpio_set_level((gpio_num_t)pin,val));
}

/*!
 *   @brief   NeoPixel constructor when length, pin and pixel type are known
 *            at compile-time.
 *   @param   n  Number of NeoPixels in strand.
 *   @param   p  Arduino pin number which will drive the NeoPixel data in.
 *   @param   t  Pixel type -- add together NEO_* constants defined in
 *               Esp32NeoPixel.hxx, for example NEO_GRB+NEO_KHZ800 for
 *               NeoPixels expecting an 800 KHz (vs 400 KHz) data stream
 *               with color bytes expressed in green, red, blue order per
 *               pixel.
 *   @return  Esp32NeoPixel object. Call the begin() function before use.
 * */
Esp32NeoPixel::Esp32NeoPixel(uint16_t n, int16_t p, neoPixelType t)
      : begun(false), brightness(0), pixels(NULL), endTime(0) 
{
    updateType(t);
    updateLength(n);
    setPin(p);
}

/*!
 *   @brief   "Empty" NeoPixel constructor when length, pin and/or pixel type
 *            are not known at compile-time, and must be initialized later with
 *            updateType(), updateLength() and setPin().
 *   @return  Esp32NeoPixel object. Call the begin() function before use.
 *   @note    This function is deprecated, here only for old projects that
 *            may still be calling it. New projects should instead use the
 *            'new' keyword with the first constructor syntax (length, pin,
 *            type).
 * */
Esp32NeoPixel::Esp32NeoPixel()
      :
#if defined(NEO_KHZ400)
is800KHz(true),
#endif
begun(false), numLEDs(0), numBytes(0), pin(-1), brightness(0),
pixels(NULL), rOffset(1), gOffset(0), bOffset(2), wOffset(1), endTime(0) 
{
}

/*!
 *   @brief   Deallocate Esp32NeoPixel object, set data pin back to INPUT.
 * */
Esp32NeoPixel::~Esp32NeoPixel() 
{
    free(pixels);
    if (pin >= 0) pinMode(pin, INPUT);
}

/*!
   @brief   Configure NeoPixel pin for output.
 */
void Esp32NeoPixel::begin(void) {
    if (pin >= 0) {
        pinMode(pin, OUTPUT);
        digitalWrite(pin, LOW);
    }
    begun = true;
}

/*!
 *   @brief   Change the length of a previously-declared Esp32NeoPixel
 *            strip object. Old data is deallocated and new data is cleared.
 *            Pin number and pixel format are unchanged.
 *   @param   n  New length of strip, in pixels.
 *   @note    This function is deprecated, here only for old projects that
 *            may still be calling it. New projects should instead use the
 *            'new' keyword with the first constructor syntax (length, pin,
 *            type).
 * */
void Esp32NeoPixel::updateLength(uint16_t n) {
    free(pixels); // Free existing data (if any)
    
    // Allocate new data -- note: ALL PIXELS ARE CLEARED
    numBytes = n * ((wOffset == rOffset) ? 3 : 4);
    if ((pixels = (uint8_t *)malloc(numBytes))) {
        memset(pixels, 0, numBytes);
        numLEDs = n;
    } else {
        numLEDs = numBytes = 0;
    }
}

/*!
 *   @brief   Change the pixel format of a previously-declared
 *            Esp32NeoPixel strip object. If format changes from one of
 *            the RGB variants to an RGBW variant (or RGBW to RGB), the old
 *            data will be deallocated and new data is cleared. Otherwise,
 *            the old data will remain in RAM and is not reordered to the
 *            new format, so it's advisable to follow up with clear().
 *   @param   t  Pixel type -- add together NEO_* constants defined in
 *               Esp32NeoPixel.hxx, for example NEO_GRB+NEO_KHZ800 for
 *               NeoPixels expecting an 800 KHz (vs 400 KHz) data stream
 *               with color bytes expressed in green, red, blue order per
 *               pixel.
 *   @note    This function is deprecated, here only for old projects that
 *            may still be calling it. New projects should instead use the
 *            'new' keyword with the first constructor syntax
 *            (length, pin, type).
 * */
void Esp32NeoPixel::updateType(neoPixelType t) {
    bool oldThreeBytesPerPixel = (wOffset == rOffset); // false if RGBW
    
    wOffset = (t >> 6) & 0b11; // See notes in header file
    rOffset = (t >> 4) & 0b11; // regarding R/G/B/W offsets
    gOffset = (t >> 2) & 0b11;
    bOffset = t & 0b11;
#if defined(NEO_KHZ400)
    is800KHz = (t < 256); // 400 KHz flag is 1<<8
#endif
    // If bytes-per-pixel has changed (and pixel data was previously
    // allocated), re-allocate to new size. Will clear any data.
    if (pixels) {
        bool newThreeBytesPerPixel = (wOffset == rOffset);
        if (newThreeBytesPerPixel != oldThreeBytesPerPixel)
            updateLength(numLEDs);
    }
}

extern "C" void espShow(uint16_t pin, uint8_t *pixels, uint32_t numBytes,
                        uint8_t type);


/*!
 *   @brief   Transmit pixel data in RAM to NeoPixels.
 *   @note    On most architectures, interrupts are temporarily disabled in
 *            order to achieve the correct NeoPixel signal timing. This means
 *            that the Arduino millis() and micros() functions, which require
 *            interrupts, will lose small intervals of time whenever this
 *            function is called (about 30 microseconds per RGB pixel, 40 for
 *            RGBW pixels). There's no easy fix for this, but a few
 *            specialized alternative or companion libraries exist that use
 *            very device-specific peripherals to work around it.
 * */
void Esp32NeoPixel::show(void) {
    
    if (!pixels)
        return;
    
    // Data latch = 300+ microsecond pause in the output stream. Rather than
    // put a delay at the end of the function, the ending time is noted and
    // the function will simply hold off (if needed) on issuing the
    // subsequent round of data until the latch time has elapsed. This
    // allows the mainline code to start generating the next frame of data
    // rather than stalling for the latch.
    while (!canShow())
        ;
    // endTime is a private member (rather than global var) so that multiple
    // instances on different pins can be quickly issued in succession (each
    // instance doesn't delay the next).
    
    espShow(pin, pixels, numBytes, is800KHz);
    
    endTime = micros(); // Save EOD time for latch on next call
}

/*!
 *   @brief   Set/change the NeoPixel output pin number. Previous pin,
 *            if any, is set to INPUT and the new pin is set to OUTPUT.
 *   @param   p  Arduino pin number (-1 = no pin).
 * */
void Esp32NeoPixel::setPin(int16_t p) {
    if (begun && (pin >= 0))
        pinMode(pin, INPUT); // Disable existing out pin
    pin = p;
    if (begun) {
        pinMode(p, OUTPUT);
        digitalWrite(p, LOW);
    }
}

/*!
 *   @brief   Set a pixel's color using separate red, green and blue
 *            components. If using RGBW pixels, white will be set to 0.
 *   @param   n  Pixel index, starting from 0.
 *   @param   r  Red brightness, 0 = minimum (off), 255 = maximum.
 *   @param   g  Green brightness, 0 = minimum (off), 255 = maximum.
 *   @param   b  Blue brightness, 0 = minimum (off), 255 = maximum.
 * */
void Esp32NeoPixel::setPixelColor(uint16_t n, uint8_t r, uint8_t g,
                                      uint8_t b) {
    
    if (n < numLEDs) {
        if (brightness) { // See notes in setBrightness()
            r = (r * brightness) >> 8;
            g = (g * brightness) >> 8;
            b = (b * brightness) >> 8;
        }
        uint8_t *p;
        if (wOffset == rOffset) { // Is an RGB-type strip
            p = &pixels[n * 3];     // 3 bytes per pixel
        } else {                  // Is a WRGB-type strip
            p = &pixels[n * 4];     // 4 bytes per pixel
            p[wOffset] = 0;         // But only R,G,B passed -- set W to 0
        }
        p[rOffset] = r; // R,G,B always stored
        p[gOffset] = g;
        p[bOffset] = b;
    }
}

/*!
 *   @brief   Set a pixel's color using separate red, green, blue and white
 *            components (for RGBW NeoPixels only).
 *   @param   n  Pixel index, starting from 0.
 *   @param   r  Red brightness, 0 = minimum (off), 255 = maximum.
 *   @param   g  Green brightness, 0 = minimum (off), 255 = maximum.
 *   @param   b  Blue brightness, 0 = minimum (off), 255 = maximum.
 *   @param   w  White brightness, 0 = minimum (off), 255 = maximum, ignored
 *               if using RGB pixels.
 * */
void Esp32NeoPixel::setPixelColor(uint16_t n, uint8_t r, uint8_t g,
                                      uint8_t b, uint8_t w) {
    
    if (n < numLEDs) {
        if (brightness) { // See notes in setBrightness()
            r = (r * brightness) >> 8;
            g = (g * brightness) >> 8;
            b = (b * brightness) >> 8;
            w = (w * brightness) >> 8;
        }
        uint8_t *p;
        if (wOffset == rOffset) { // Is an RGB-type strip
            p = &pixels[n * 3];     // 3 bytes per pixel (ignore W)
        } else {                  // Is a WRGB-type strip
            p = &pixels[n * 4];     // 4 bytes per pixel
            p[wOffset] = w;         // Store W
        }
        p[rOffset] = r; // Store R,G,B
        p[gOffset] = g;
        p[bOffset] = b;
    }
}

/*!
 *   @brief   Set a pixel's color using a 32-bit 'packed' RGB or RGBW value.
 *   @param   n  Pixel index, starting from 0.
 *   @param   c  32-bit color value. Most significant byte is white (for RGBW
 *               pixels) or ignored (for RGB pixels), next is red, then green,
 *               and least significant byte is blue.
 * */
void Esp32NeoPixel::setPixelColor(uint16_t n, uint32_t c) {
    if (n < numLEDs) {
        uint8_t *p, r = (uint8_t)(c >> 16), g = (uint8_t)(c >> 8), b = (uint8_t)c;
        if (brightness) { // See notes in setBrightness()
            r = (r * brightness) >> 8;
            g = (g * brightness) >> 8;
            b = (b * brightness) >> 8;
        }
        if (wOffset == rOffset) {
            p = &pixels[n * 3];
        } else {
            p = &pixels[n * 4];
            uint8_t w = (uint8_t)(c >> 24);
            p[wOffset] = brightness ? ((w * brightness) >> 8) : w;
        }
        p[rOffset] = r;
        p[gOffset] = g;
        p[bOffset] = b;
    }
}

/*!
 *   @brief   Fill all or part of the NeoPixel strip with a color.
 *   @param   c      32-bit color value. Most significant byte is white (for
 *                   RGBW pixels) or ignored (for RGB pixels), next is red,
 *                   then green, and least significant byte is blue. If all
 *                   arguments are unspecified, this will be 0 (off).
 *   @param   first  Index of first pixel to fill, starting from 0. Must be
 *                   in-bounds, no clipping is performed. 0 if unspecified.
 *   @param   count  Number of pixels to fill, as a positive value. Passing
 *                   0 or leaving unspecified will fill to end of strip.
 * */
void Esp32NeoPixel::fill(uint32_t c, uint16_t first, uint16_t count) {
    uint16_t i, end;
    
    if (first >= numLEDs) {
        return; // If first LED is past end of strip, nothing to do
    }
    
    // Calculate the index ONE AFTER the last pixel to fill
    if (count == 0) {
        // Fill to end of strip
        end = numLEDs;
    } else {
        // Ensure that the loop won't go past the last pixel
        end = first + count;
        if (end > numLEDs)
            end = numLEDs;
    }
    
    for (i = first; i < end; i++) {
        this->setPixelColor(i, c);
    }
}

/*!
 *   @brief   Convert hue, saturation and value into a packed 32-bit RGB color
 *            that can be passed to setPixelColor() or other RGB-compatible
 *            functions.
 *   @param   hue  An unsigned 16-bit value, 0 to 65535, representing one full
 *                 loop of the color wheel, which allows 16-bit hues to "roll
 *                 over" while still doing the expected thing (and allowing
 *                 more precision than the wheel() function that was common to
 *                 prior NeoPixel examples).
 *   @param   sat  Saturation, 8-bit value, 0 (min or pure grayscale) to 255
 *                 (max or pure hue). Default of 255 if unspecified.
 *   @param   val  Value (brightness), 8-bit value, 0 (min / black / off) to
 *                 255 (max or full brightness). Default of 255 if unspecified.
 *   @return  Packed 32-bit RGB with the most significant byte set to 0 -- the
 *            white element of WRGB pixels is NOT utilized. Result is linearly
 *            but not perceptually correct, so you may want to pass the result
 *            through the gamma32() function (or your own gamma-correction
 *            operation) else colors may appear washed out. This is not done
 *            automatically by this function because coders may desire a more
 *            refined gamma-correction function than the simplified
 *            one-size-fits-all operation of gamma32(). Diffusing the LEDs also
 *            really seems to help when using low-saturation colors.
 * */
uint32_t Esp32NeoPixel::ColorHSV(uint16_t hue, uint8_t sat, uint8_t val) {
    
    uint8_t r, g, b;
    
    // Remap 0-65535 to 0-1529. Pure red is CENTERED on the 64K rollover;
    // 0 is not the start of pure red, but the midpoint...a few values above
    // zero and a few below 65536 all yield pure red (similarly, 32768 is the
    // midpoint, not start, of pure cyan)re on that below)y allowing hue to roll over in either direction.
    hue = (hue * 1530L + 32768) / 65536;
    // Because red is centered on the rollover point (the +32768 above,
    // essentially a fixed-point +0.5)operator, 1530 is handled as a special case below.
    
    // So you'd think that the color "hexcone" (the thing that ramps from
    // pure red, to pure yellow, to pure green and so forth back to red,
    // yielding six slices)lity there's 1530. This is because the last element in
    // each 256-element slice is equal to the first element of the next
    // slice, and keeping those in there this would create small
    // discontinuities in the color wheel. So the last element of each
    // slice is dropped...we regard only elements 0-254, with item 255
    // being picked up as element 0 of the next slice. Like this:
    // Red to not-quite-pure-yellow is:        255,   0, 0 to 255, 254,   0
    // Pure yellow to not-quite-pure-green is: 255, 255, 0 to   1, 255,   0
    // Pure green to not-quite-pure-cyan is:     0, 255, 0 to   0, 255, 254
    // and so forth. Hence, 1530 distinct hues (0 to 1529), and hence why
    // the constants below are not the multiples of 256 you might expect.
    
    // Convert hue to R,G,B (nested ifs faster than divide+mod+switch):
    if (hue < 510) { // Red to Green-1
        b = 0;
        if (hue < 255) { //   Red to Yellow-1
            r = 255;
            g = hue;       //     g = 0 to 254
        } else {         //   Yellow to Green-1
            r = 510 - hue; //     r = 255 to 1
            g = 255;
        }
    } else if (hue < 1020) { // Green to Blue-1
        r = 0;
        if (hue < 765) { //   Green to Cyan-1
            g = 255;
            b = hue - 510;  //     b = 0 to 254
        } else {          //   Cyan to Blue-1
            g = 1020 - hue; //     g = 255 to 1
            b = 255;
        }
    } else if (hue < 1530) { // Blue to Red-1
        g = 0;
        if (hue < 1275) { //   Blue to Magenta-1
            r = hue - 1020; //     r = 0 to 254
            b = 255;
        } else { //   Magenta to Red-1
            r = 255;
            b = 1530 - hue; //     b = 255 to 1
        }
    } else { // Last 0.5 Red (quicker than % operator)
        r = 255;
        g = b = 0;
    }
    
    // Apply saturation and value to R,G,B, pack into 32-bit result:
    uint32_t v1 = 1 + val;  // 1 to 256; allows >>8 instead of /255
    uint16_t s1 = 1 + sat;  // 1 to 256; same reason
    uint8_t s2 = 255 - sat; // 255 to 0
    return ((((((r * s1) >> 8) + s2) * v1) & 0xff00) << 8) |
          (((((g * s1) >> 8) + s2) * v1) & 0xff00) |
          (((((b * s1) >> 8) + s2) * v1) >> 8);
}

/*!
 *   @brief   Query the color of a previously-set pixel.
 *   @param   n  Index of pixel to read (0 = first).
 *   @return  'Packed' 32-bit RGB or WRGB value. Most significant byte is white
 *            (for RGBW pixels) or 0 (for RGB pixels), next is red, then green,
 *            and least significant byte is blue.
 *   @note    If the strip brightness has been changed from the default value
 *            of 255, the color read from a pixel may not exactly match what
 *            was previously written with one of the setPixelColor() functions.
 *            This gets more pronounced at lower brightness levels.
 * */
uint32_t Esp32NeoPixel::getPixelColor(uint16_t n) const {
    if (n >= numLEDs)
        return 0; // Out of bounds, return no color.
    
    uint8_t *p;
    
    if (wOffset == rOffset) { // Is RGB-type device
        p = &pixels[n * 3];
        if (brightness) {
            // Stored color was decimated by setBrightness(). Returned value
            // attempts to scale back to an approximation of the original 24-bit
            // value used when setting the pixel color, but there will always be
            // some error -- those bits are simply gone. Issue is most
            // pronounced at low brightness levels.
            return (((uint32_t)(p[rOffset] << 8) / brightness) << 16) |
                  (((uint32_t)(p[gOffset] << 8) / brightness) << 8) |
                  ((uint32_t)(p[bOffset] << 8) / brightness);
        } else {
            // No brightness adjustment has been made -- return 'raw' color
            return ((uint32_t)p[rOffset] << 16) | ((uint32_t)p[gOffset] << 8) |
                  (uint32_t)p[bOffset];
        }
    } else { // Is RGBW-type device
        p = &pixels[n * 4];
        if (brightness) { // Return scaled color
            return (((uint32_t)(p[wOffset] << 8) / brightness) << 24) |
                  (((uint32_t)(p[rOffset] << 8) / brightness) << 16) |
                  (((uint32_t)(p[gOffset] << 8) / brightness) << 8) |
                  ((uint32_t)(p[bOffset] << 8) / brightness);
        } else { // Return raw color
            return ((uint32_t)p[wOffset] << 24) | ((uint32_t)p[rOffset] << 16) |
                  ((uint32_t)p[gOffset] << 8) | (uint32_t)p[bOffset];
        }
    }
}

/*!
 *   @brief   Adjust output brightness. Does not immediately affect what's
 *            currently displayed on the LEDs. The next call to show() will
 *            refresh the LEDs at this level.
 *   @param   b  Brightness setting, 0=minimum (off), 255=brightest.
 *   @note    This was intended for one-time use in one's setup() function,
 *            not as an animation effect in itself. Because of the way this
 *            library "pre-multiplies" LED colors in RAM, changing the
 *            brightness is often a "lossy" operation -- what you write to
 *            pixels isn't necessary the same as what you'll read back.
 *            Repeated brightness changes using this function exacerbate the
 *            problem. Smart programs therefore treat the strip as a
 *            write-only resource, maintaining their own state to render each
 *            frame of an animation, not relying on read-modify-write.
 * */
void Esp32NeoPixel::setBrightness(uint8_t b) {
    // Stored brightness value is different than what's passed.
    // This simplifies the actual scaling math later, allowing a fast
    // 8x8-bit multiply and taking the MSB. 'brightness' is a uint8_t,
    // adding 1 here may (intentionally) roll over...so 0 = max brightness
    // (color values are interpreted literally; no scaling), 1 = min
    // brightness (off), 255 = just below max brightness.
    uint8_t newBrightness = b + 1;
    if (newBrightness != brightness) { // Compare against prior value
        // Brightness has changed -- re-scale existing data in RAM,
        // This process is potentially "lossy," especially when increasing
        // brightness. The tight timing in the WS2811/WS2812 code means there
        // aren't enough free cycles to perform this scaling on the fly as data
        // is issued. So we make a pass through the existing color data in RAM
        // and scale it (subsequent graphics commands also work at this
        // brightness level). If there's a significant step up in brightness,
        // the limited number of steps (quantization) in the old data will be
        // quite visible in the re-scaled version. For a non-destructive
        // change, you'll need to re-render the full strip data. C'est la vie.
        uint8_t c, *ptr = pixels,
              oldBrightness = brightness - 1; // De-wrap old brightness value
        uint16_t scale;
        if (oldBrightness == 0)
            scale = 0; // Avoid /0
        else if (b == 255)
            scale = 65535 / oldBrightness;
        else
            scale = (((uint16_t)newBrightness << 8) - 1) / oldBrightness;
        for (uint16_t i = 0; i < numBytes; i++) {
            c = *ptr;
            *ptr++ = (c * scale) >> 8;
        }
        brightness = newBrightness;
    }
}

/*!
 *   @brief   Retrieve the last-set brightness value for the strip.
 *   @return  Brightness value: 0 = minimum (off), 255 = maximum.
 * */
uint8_t Esp32NeoPixel::getBrightness(void) const { return brightness - 1; }

/*!
 *   @brief   Fill the whole NeoPixel strip with 0 / black / off.
 * */
void Esp32NeoPixel::clear(void) { memset(pixels, 0, numBytes); }

// A 32-bit variant of gamma8() that applies the same function
// to all components of a packed RGB or WRGB value.
uint32_t Esp32NeoPixel::gamma32(uint32_t x) {
    uint8_t *y = (uint8_t *)&x;
    // All four bytes of a 32-bit value are filtered even if RGB (not WRGB),
    // to avoid a bunch of shifting and masking that would be necessary for
    // properly handling different endianisms (and each byte is a fairly
    // trivial operation, so it might not even be wasting cycles vs a check
    // and branch for the RGB case)value, but this seems exceedingly rare and if it's
    // encountered in reality they can mask values going in or coming out.
    for (uint8_t i = 0; i < 4; i++)
        y[i] = gamma8(y[i]);
    return x; // Packed 32-bit return
}

/*!
 *   @brief   Fill NeoPixel strip with one or more cycles of hues.
 *            Everyone loves the rainbow swirl so much, now it's canon!
 *   @param   first_hue   Hue of first pixel, 0-65535, representing one full
 *                        cycle of the color wheel. Each subsequent pixel will
 *                        be offset to complete one or more cycles over the
 *                        length of the strip.
 *   @param   reps        Number of cycles of the color wheel over the length
 *                        of the strip. Default is 1. Negative values can be
 *                        used to reverse the hue order.
 *   @param   saturation  Saturation (optional), 0-255 = gray to pure hue,
 *                        default = 255.
 *   @param   brightness  Brightness/value (optional), 0-255 = off to max,
 *                        default = 255. This is distinct and in combination
 *                        with any configured global strip brightness.
 *   @param   gammify     If true (default), apply gamma correction to colors
 *                        for better appearance.
 * */
void Esp32NeoPixel::rainbow(uint16_t first_hue, int8_t reps,
                                uint8_t saturation, uint8_t brightness, bool gammify) {
    for (uint16_t i=0; i<numLEDs; i++) {
        uint16_t hue = first_hue + (i * reps * 65536) / numLEDs;
        uint32_t color = ColorHSV(hue, saturation, brightness);
        if (gammify) color = gamma32(color);
        setPixelColor(i, color);
    }
}
