RobertPHeller/ESP32-LCC/ESP32-Feather-6B6L/ESP32-Feather-6B6L/LED.h

// -!- c++ -!- //////////////////////////////////////////////////////////////
//
//  System        : 
//  Module        : 
//  Object Name   : $RCSfile$
//  Revision      : $Revision$
//  Date          : $Date$
//  Author        : $Author$
//  Created By    : Robert Heller
//  Created       : Mon Jun 21 22:27:50 2021
//  Last Modified : <241215.1336>
//
//  Description	
//
//  Notes
//
//  History
//	
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
#ifndef __LED_H
#define __LED_H

#include "openlcb/EventHandlerTemplates.hxx"
#include "openlcb/ConfigRepresentation.hxx"
#include "utils/ConfigUpdateListener.hxx"
#include "utils/ConfigUpdateService.hxx"
#include "openlcb/RefreshLoop.hxx"
#include <stdio.h>
#include "LEDConfig.h"

#include "Blink.h"



class LED 
      : public ConfigUpdateListener
, public Blinking
{
public:
    using Impl = openlcb::MemoryBit<uint8_t>;
    
    enum LEDPhase {Steady, Pulse, A_Slow, A_Medium, A_Fast, 
              B_Slow, B_Medium, B_Fast};

    LED(openlcb::Node *node, const LEDConfig &cfg, const Gpio *gpio)
                : impl_(node, 0, 0, &state_, 1)
          , consumer_(&impl_)
          , cfg_(cfg)
          , gpio_(gpio)
          , phase_(Steady)
    {
        ConfigUpdateService::instance()->register_update_listener(this);
        BlinkTimer::instance()->AddMe(this);
    }
    template <class HW>
    LED(openlcb::Node *node, const LEDConfig &cfg, const HW &, const Gpio* g = HW::instance())
                : impl_(node, 0, 0, &state_, 1)
          , consumer_(&impl_)
          , cfg_(cfg)
          , gpio_(g)
          , phase_(Steady)
    {
        ConfigUpdateService::instance()->register_update_listener(this);
        BlinkTimer::instance()->AddMe(this);
    }
    UpdateAction apply_configuration(int fd, bool initial_load,
                                     BarrierNotifiable *done) OVERRIDE
    {
        AutoNotify n(done);
        openlcb::EventId cfg_event_on = cfg_.event_on().read(fd);
        openlcb::EventId cfg_event_off = cfg_.event_off().read(fd);
        phase_ = (LEDPhase) cfg_.phase().read(fd);
        if (initial_load) {
            gpio_->clr();
        }
        pulseWidth_ = cfg_.pulsewidth().read(fd)  << 1;
        if (cfg_event_off != impl_.event_on() ||
            cfg_event_on != impl_.event_on())
        {
            auto saved_node = impl_.node();
            // Need to reinitialize the consumer. We do this with in-place
            // destruction and construction.
            consumer_.~BitEventConsumer();
            impl_.Impl::~Impl();
            new (&impl_)
                Impl(saved_node, cfg_event_on, cfg_event_off, &state_, 1);
            new (&consumer_) openlcb::BitEventConsumer(&impl_);
            return REINIT_NEEDED; // Causes events identify.
        }
        return UPDATED;
    }
    void factory_reset(int fd) OVERRIDE
    {
        CDI_FACTORY_RESET(cfg_.phase);
        CDI_FACTORY_RESET(cfg_.pulsewidth);
    }
    const LEDPhase Phase() const {return phase_;}
    const uint8_t PulseWidth() const {return pulseWidth_;}
    virtual void blink(bool AFast, bool AMedium, bool ASlow)
    {
        if (gpio_ == nullptr) return;
        if (!IsOn()) {
            gpio_->clr();
            return;
        }
        switch (phase_) {
        case Steady:
            gpio_->set();
            break;
        case Pulse:
            if (pulseCount_ > 0)
            {
                gpio_->set();
                if (AFast) pulseCount_--;
            } else {
                gpio_->clr();
                state_ = 0;
            }
            break;
        case A_Slow: 
            if (ASlow) 
            {
                gpio_->set();
            } else {
                gpio_->clr();
            }
            break;
        case A_Medium: 
            if (AMedium)
            {
                gpio_->set();
            } else {
                gpio_->clr();
            }
            break;
        case A_Fast: 
            if (AFast)
            {
                gpio_->set();
            } else {
                gpio_->clr();
            }
            break;
        case B_Slow: 
            if (ASlow)
            {
                gpio_->clr();
            } else {
                gpio_->set();
            }
            break;
        case B_Medium: 
            if (AMedium)
            {
                gpio_->clr();
            } else {
                gpio_->set();
            }
            break;
        case B_Fast: 
            if (AFast)
            {
                gpio_->clr();
            } else {
                gpio_->set();
            }
            break;
        }
    }
    bool IsOn() const 
    {
        return ((state_ & 1) != 0);
    }
private:
    Impl impl_;
    openlcb::BitEventConsumer consumer_;
    const LEDConfig cfg_;
    const Gpio* gpio_;
    LEDPhase phase_;
    uint8_t state_{0};
    uint8_t pulseWidth_;
    uint8_t pulseCount_;
};

    
    

#endif // __LED_H
