RobertPHeller/ESP32-LCC/P9WiFiLCCTraction_Sound/firmware/main/SoundData.cpp

// -!- C++ -!- //////////////////////////////////////////////////////////////
//
//  System        : 
//  Module        : 
//  Object Name   : $RCSfile$
//  Revision      : $Revision$
//  Date          : $Date$
//  Author        : $Author$
//  Created By    : Robert Heller
//  Created       : Thu Aug 20 07:39:39 2026
//  Last Modified : <260822.1042>
//
//  Description	
//
//  Notes
//
//  History
//	
/////////////////////////////////////////////////////////////////////////////
//
//    Copyright (C) 2026  Robert Heller D/B/A Deepwoods Software
//			51 Locke Hill Road
//			Wendell, MA 01379-9728
//
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
// 
//
//////////////////////////////////////////////////////////////////////////////

static const char rcsid[] = "@(#) : $Id$";

#include <fcntl.h>
#include <unistd.h>
#include "utils/logging.h"
#include <math.h>

#include "SoundData.hxx"

#include "PCMDATA/EMD576_16.pcmdat"
#include "PCMDATA/EMD710G3.pcmdat"
//#include "PCMDATA/EMD576_8.pcmdat"
//#include "PCMDATA/EMD576_12.pcmdat"
//#include "PCMDATA/EMD645_8.pcmdat"
//#include "PCMDATA/EMD645_12.pcmdat"
//#include "PCMDATA/EMD645_16.pcmdat"
//#include "PCMDATA/EMD645T_12.pcmdat"
//#include "PCMDATA/EMD645T_16.pcmdat"
//#include "PCMDATA/EMD645T_20.pcmdat"

static SoundData::SoundFileEntry EngineData[] = {
    {EMD576_16_PCM, EMD576_16_BYTES},
    {EMD710G3_PCM, EMD710G3_BYTES},
    //{EMD576_8_PCM, EMD576_8_BYTES},
    //{EMD576_12_PCM, EMD576_12_BYTES},
    //{EMD645_8_PCM, EMD645_8_BYTES},
    //{EMD645_12_PCM, EMD645_12_BYTES},
    //{EMD645_16_PCM, EMD645_16_BYTES},
    //{EMD645T_12_PCM, EMD645T_12_BYTES},
    //{EMD645T_16_PCM, EMD645T_16_BYTES},
    //{EMD645T_20_PCM, EMD645T_20_BYTES},
    {NULL, 0}
};
#define EngineDataSize (sizeof(EngineData) / sizeof(EngineData[0]))

void SoundData::EngineSound(int i2s_fp, uint8_t engineIndex, uint16_t speed)
{
    LOG(INFO, "[SoundData::EngineSound] i2s_fp=%d, engineIndex=%d, speed=%d", i2s_fp,engineIndex,speed);
    if (engineIndex >= EngineDataSize) return;
    double compression = (speed / 100.0) + 1;
    static uint16_t compressed_pcm[COMPRESSION_BUFFER_SIZE];
    size_t wordCount = EngineData[engineIndex].pcmBytes/sizeof(uint16_t);
    const uint16_t *pcm = EngineData[engineIndex].pcmData;
    //write(i2s_fp,EngineData[engineIndex].pcmData,EngineData[engineIndex].pcmBytes);
    size_t comp_words;
    for (size_t k = 0; k < wordCount; k+=COMPRESSION_BUFFER_SIZE)
    {
        comp_words = 0;
        for (size_t i = 0; i < COMPRESSION_BUFFER_SIZE; i++)
        {
            if ((i+k) >= wordCount) break;
            size_t si = ((size_t)round((i+k)*compression)) % wordCount;
            compressed_pcm[i] = pcm[si];
            comp_words++;
        }
        write(i2s_fp,compressed_pcm,comp_words*sizeof(uint16_t));
    }
}

//#include "PCMDATA/Leslie_RS3L.pcmdat"
//#include "PCMDATA/NathanAirChime.pcmdat"

static SoundData::SoundFileEntry HornData[] = {
    //{Leslie_RS3L_PCM, Leslie_RS3L_BYTES},
    //{NathanAirChime_PCM, NathanAirChime_BYTES},
    {NULL, 0}
};
#define HornDataSize (sizeof(HornData) / sizeof(HornData[0])) 

void SoundData::HornSound(int i2s_fp, uint8_t hornIndex)
{
    LOG(INFO, "[SoundData::HornSound] i2s_fp=%d, hornIndex=%d",i2s_fp,hornIndex);
    if (hornIndex >= HornDataSize) return;
    write(i2s_fp,HornData[hornIndex].pcmData,HornData[hornIndex].pcmBytes);
}

//#include "PCMDATA/StandardBell.pcmdat"

static SoundData::SoundFileEntry BellData[] = {
    //{StandardBell_PCM, StandardBell_BYTES},
    {NULL, 0}
};
#define BellDataSize (sizeof(BellData) / sizeof(BellData[0])) 

void SoundData::BellSound(int i2s_fp, uint8_t bellIndex)
{
    LOG(INFO, "[SoundData:BellSound] i2s_fp=%d, bellIndex=%d",i2s_fp,bellIndex);
    if (bellIndex >= BellDataSize) return;
    write(i2s_fp,BellData[bellIndex].pcmData,BellData[bellIndex].pcmBytes);
}
